SimeonSimeonovIvanov/AVR-LPC/Scheme and Board/v.0.0.5/v.0.0.5 (Bottom - Component Side - Mirror).pdf

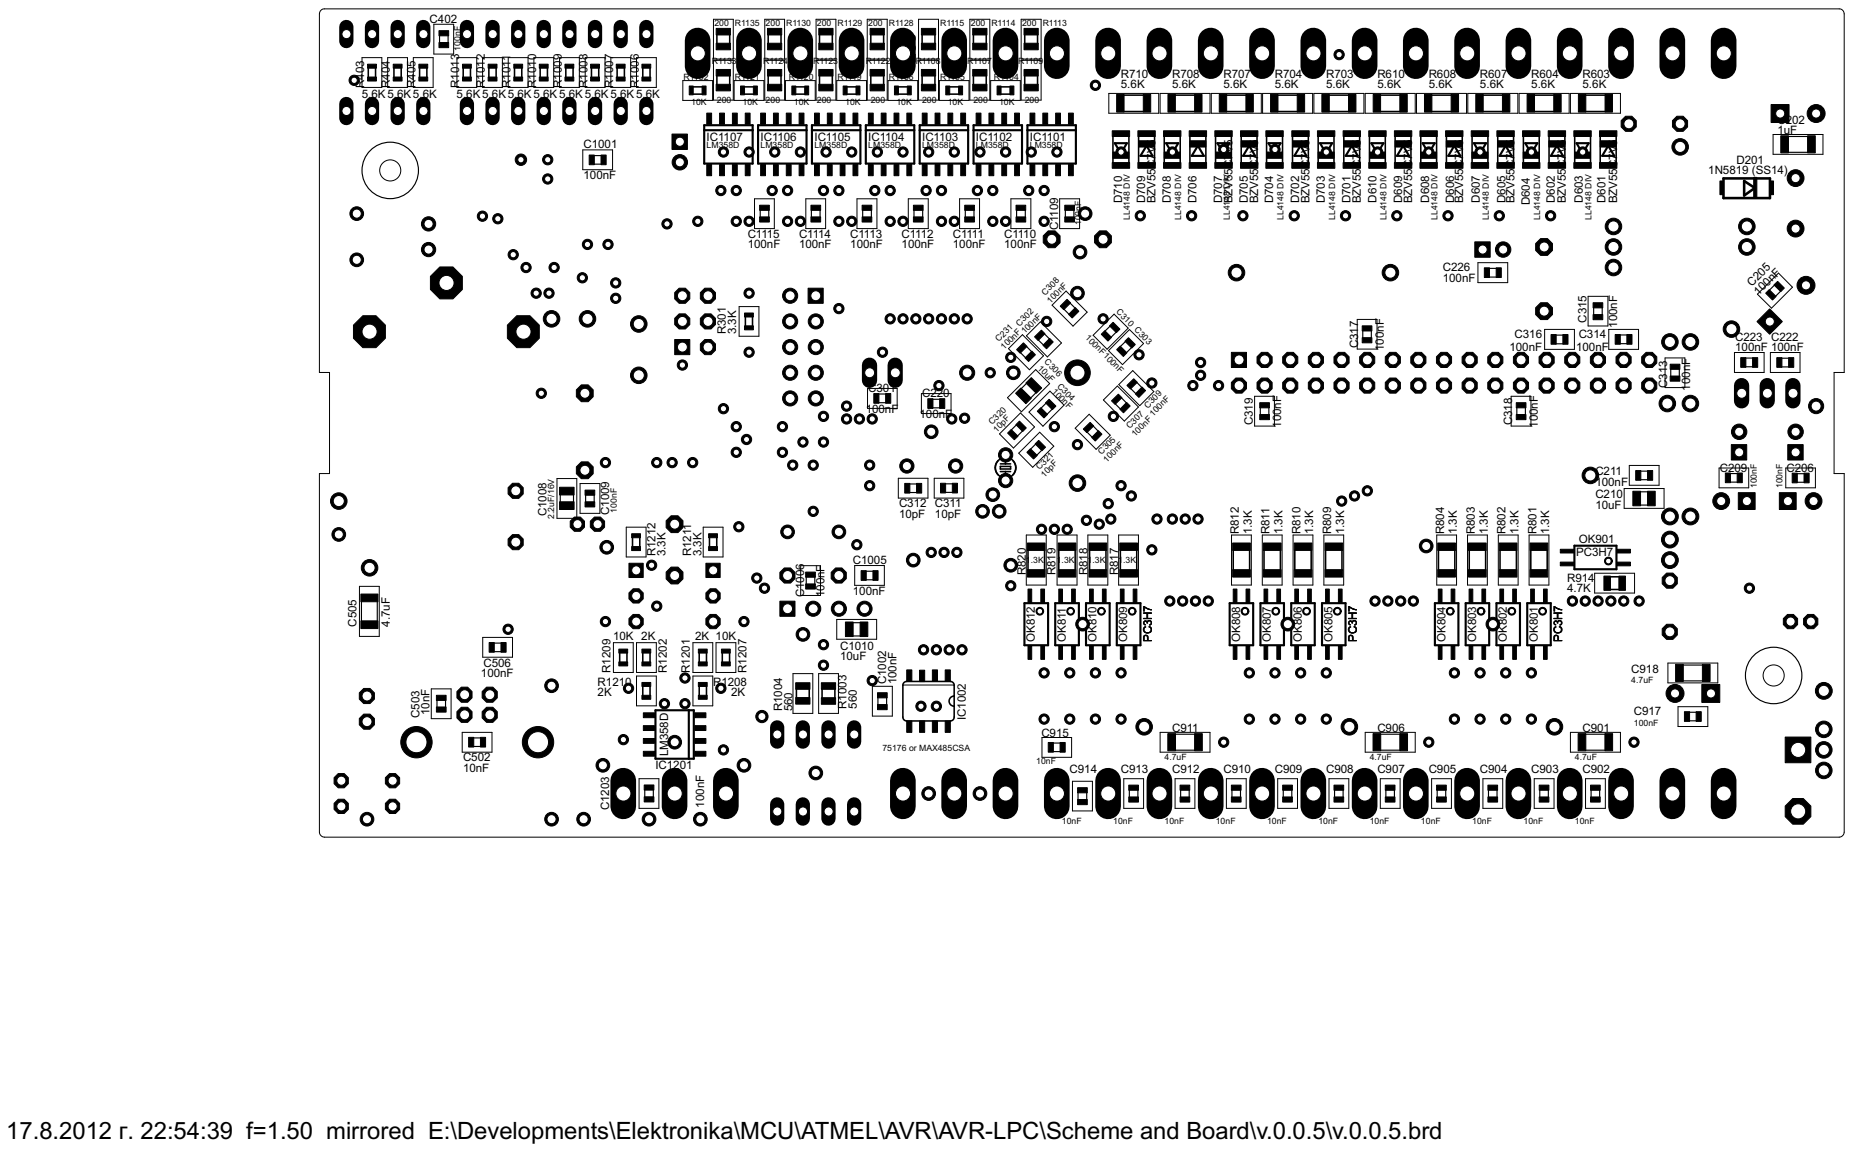
[picture p32: page 1]

17.8.2012 г. 22:54:39 f=1.50 mirrored E:\Developments\Elektronika\MCU\ATMEL\AVR\AVR-LPC\Scheme and Board\v.0.0.5\v.0.0.5.brd
