SimeonSimeonovIvanov/AVR-LPC/Scheme and Board/v.0.0.3/v.0.0.3 (Component Side).pdf

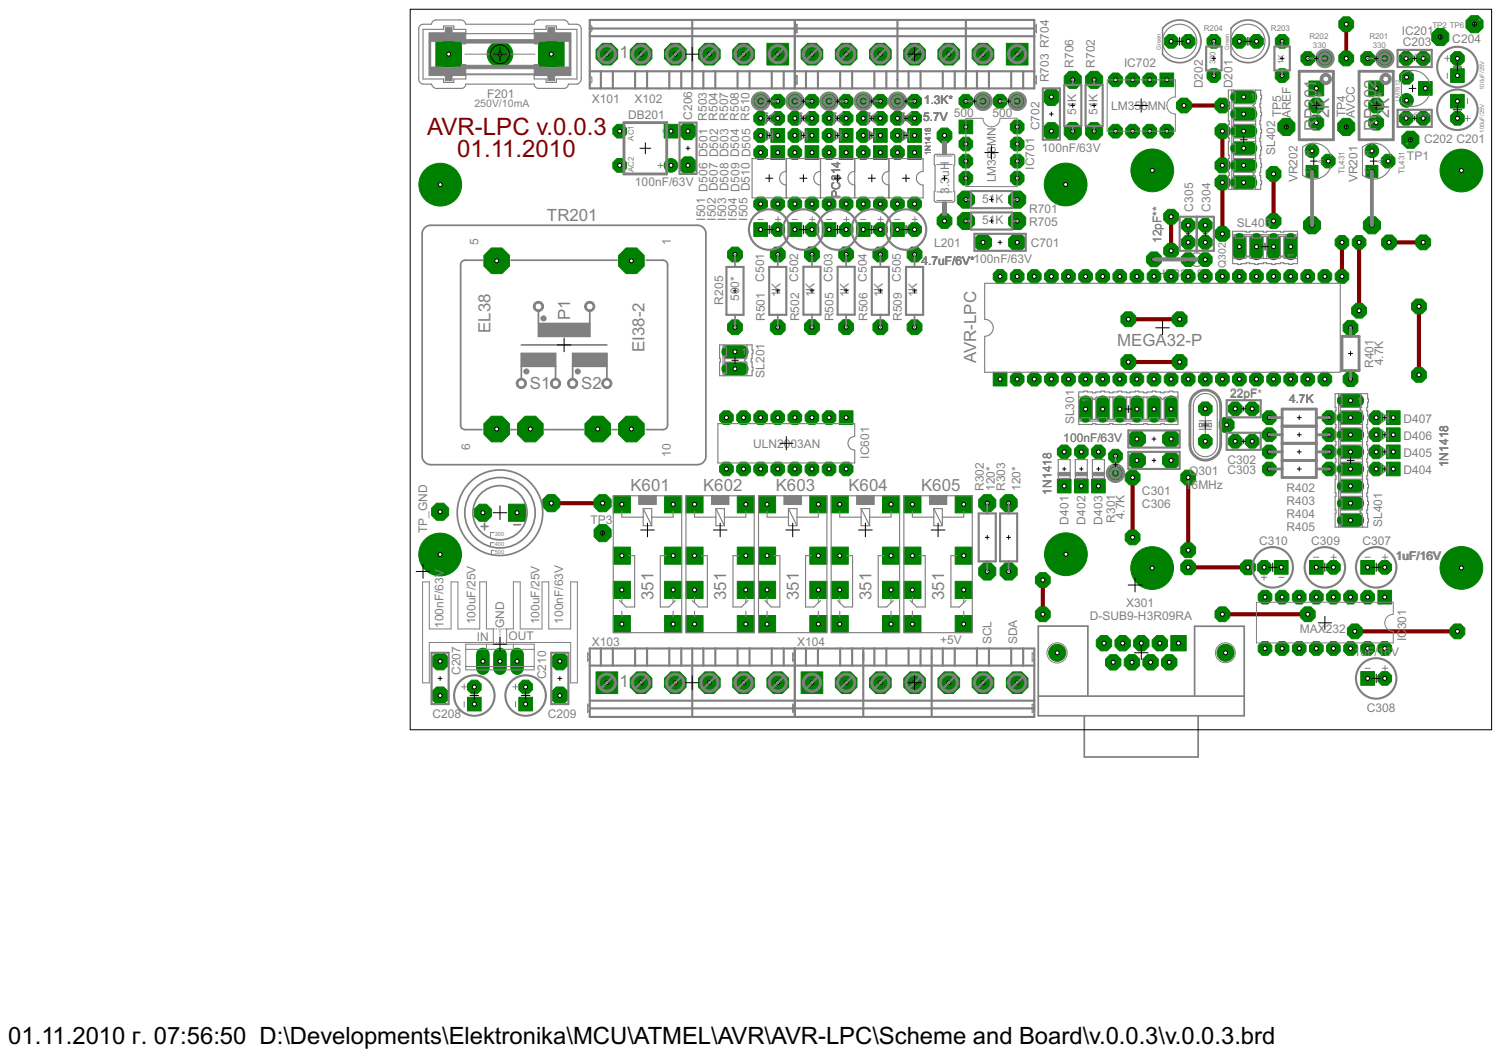
[picture p33: page 1]

01.11.2010 г. 07:56:50 D:\Developments\Elektronika\MCU\ATMEL\AVR\AVR-LPC\Scheme and Board\v.0.0.3\v.0.0.3.brd
