SimeonSimeonovIvanov/AVR-LPC/Scheme and Board/v.0.0.6/v.0.0.6 (All Side).pdf

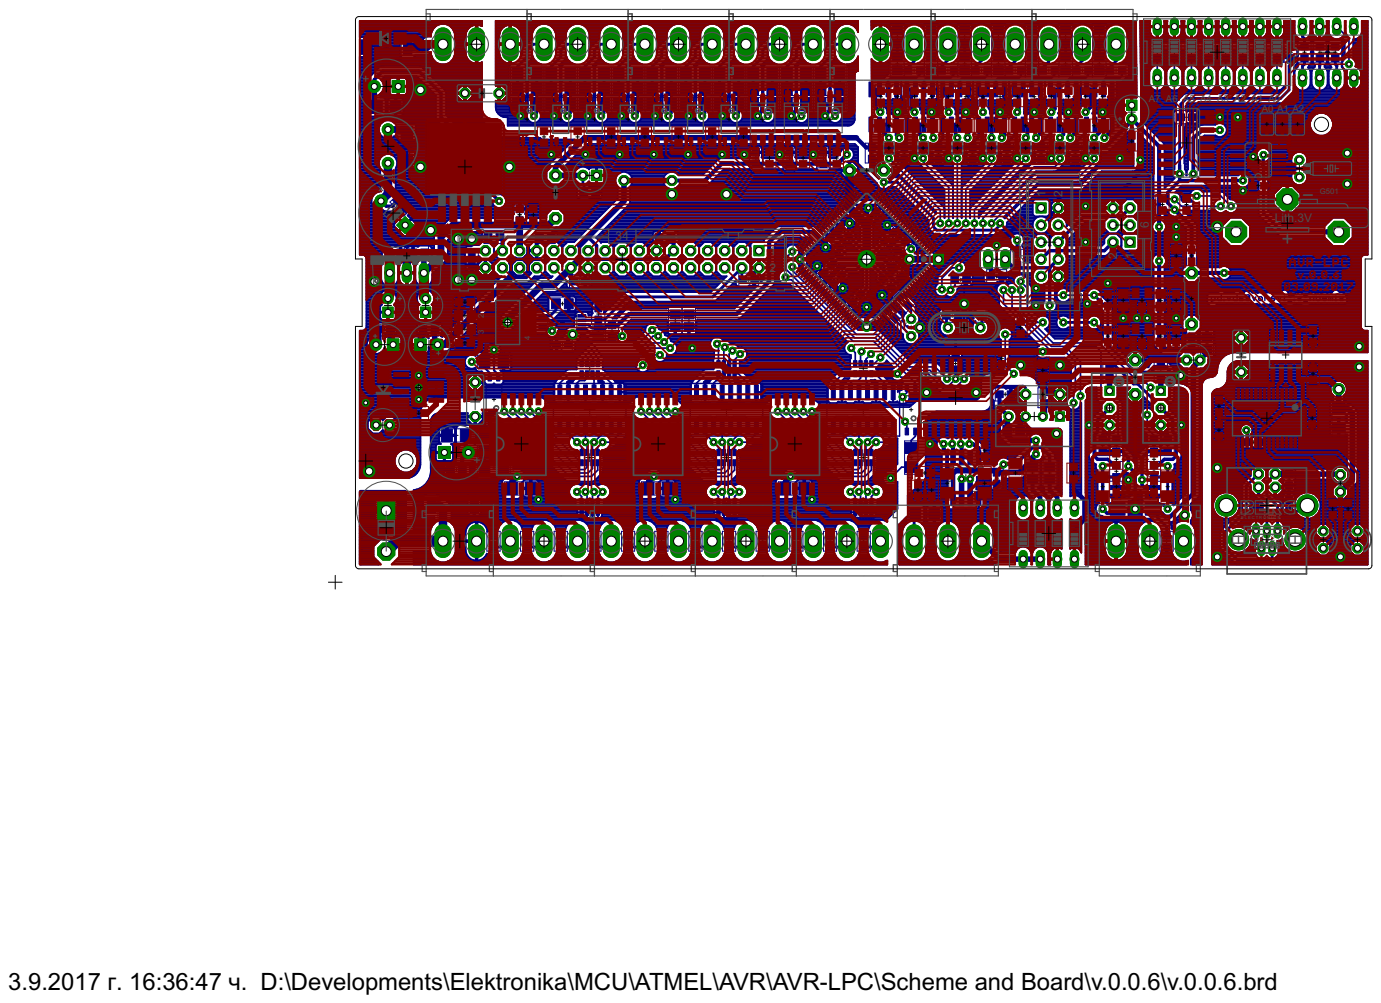
[picture p34: page 1]

3.9.2017 г. 16:36:47 ч. D:\Developments\Elektronika\MCU\ATMEL\AVR\AVR-LPC\Scheme and Board\v.0.0.6\v.0.0.6.brd
