SimeonSimeonovIvanov/AVR-LPC/Scheme and Board/v.0.0.9/v.0.0.9 (All Side).pdf

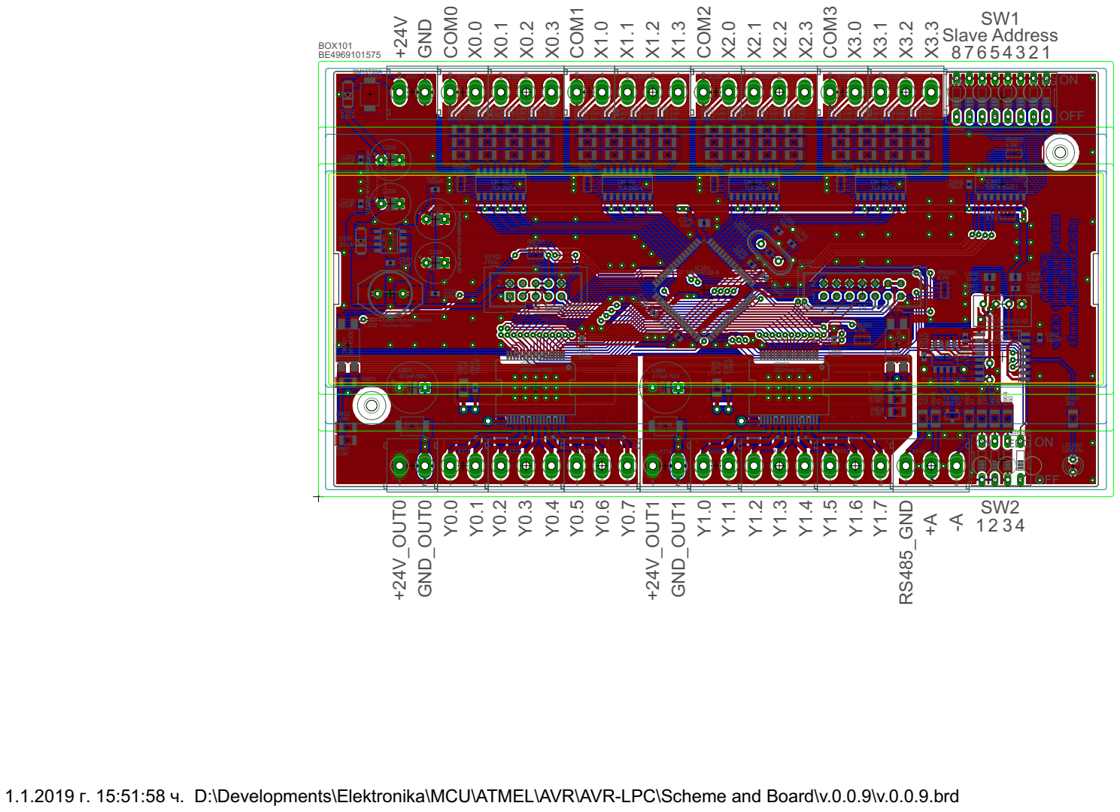
[picture p35: page 1]

D102 SS14 | OFF

E 220uF 50V LOW ESR-Fujicon CE 220uF 50V LOW ESR-Fujicon

CE 68uF 50V LOW ESR-Fujicon

CE 68uF 50V LOW ESR-Fujico

1.1.2019 г. 15:51:58 ч. D:\Developments\Elektronika\MCU\ATMEL\AVR\AVR-LPC\Scheme and Board\v.0.0.9\v.0.0.9.brd
