SimeonSimeonovIvanov/AVR-LPC/Scheme and Board/v.0.1.0/v.0.1.0 (All Side).pdf

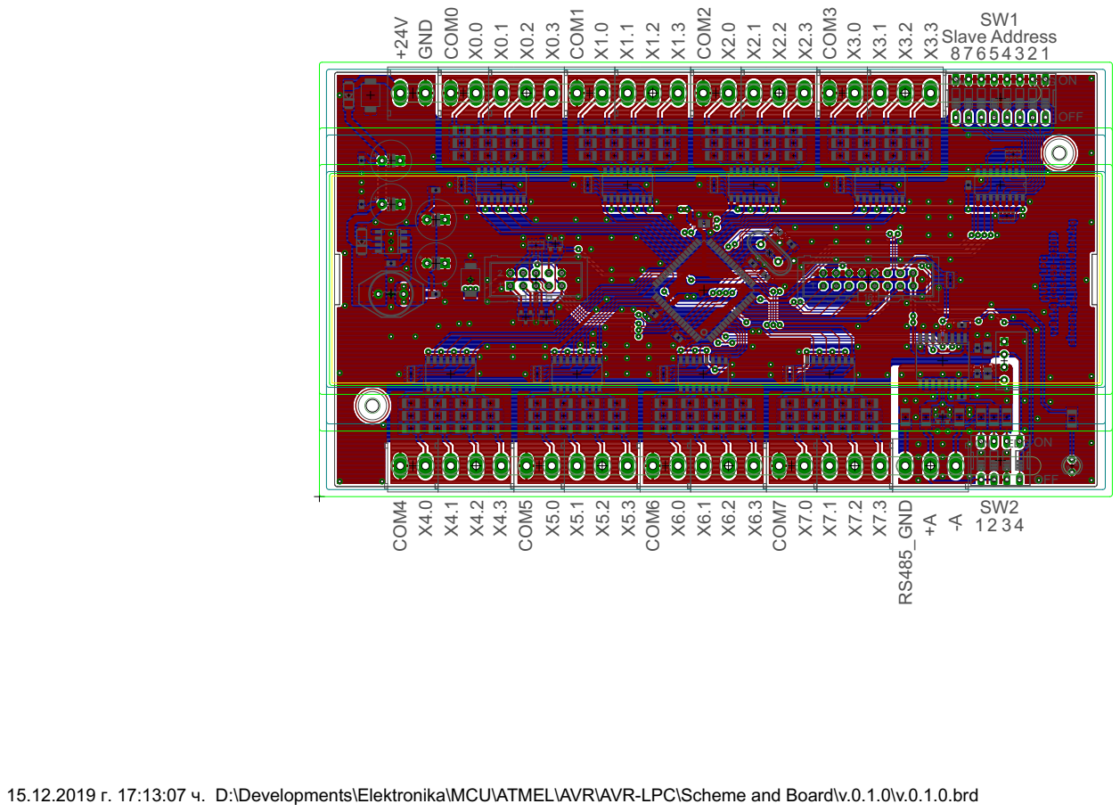
[picture p36: page 1]

15.12.2019 г. 17:13:07 ч. D:\Developments\Elektronika\MCU\ATMEL\AVR\AVR-LPC\Scheme and Board\v.0.1.0\v.0.1.0.brd
