SimeonSimeonovIvanov/AVR-LPC/Scheme and Board/v.0.1.6/v.0.1.6 (All Side).pdf

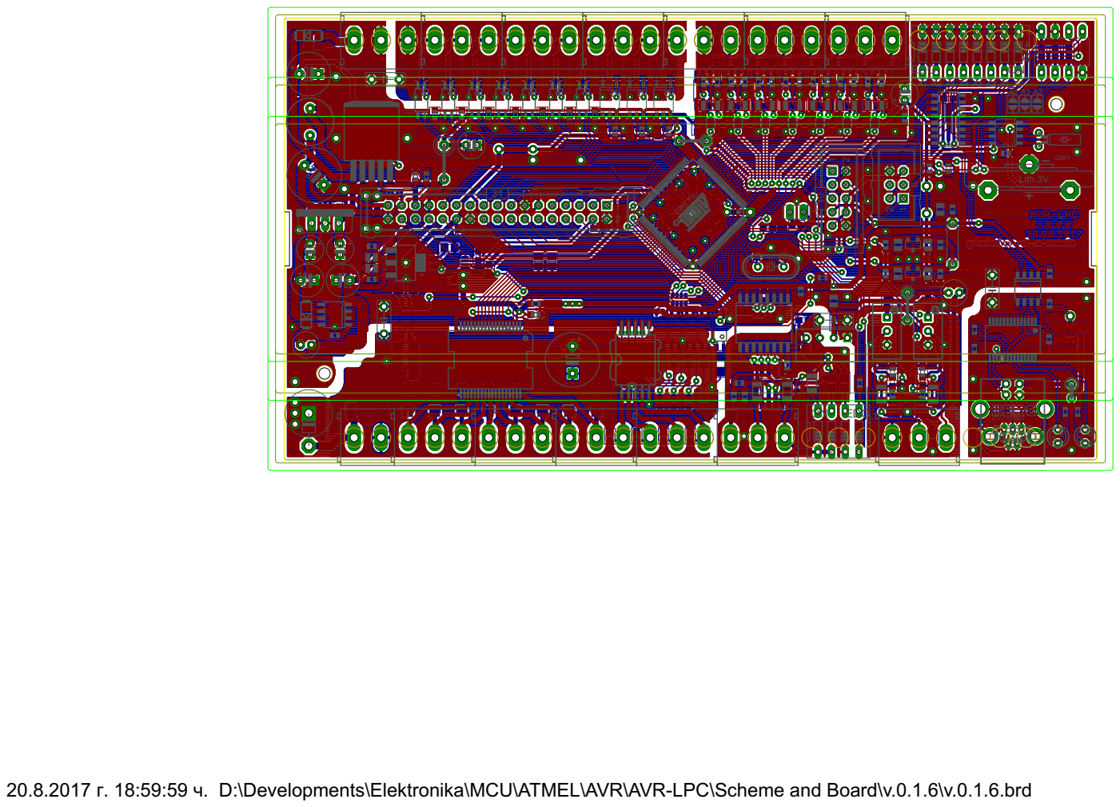
[picture p37: page 1]

20.8.2017 г. 18:59:59 ч. D:\Developments\Elektronika\MCU\ATMEL\AVR\AVR-LPC\Scheme and Board\v.0.1.6\v.0.1.6.brd
