SimeonSimeonovIvanov/AVR-LPC/Scheme and Board/v.0.1.8/v.0.1.8 (All Side).pdf

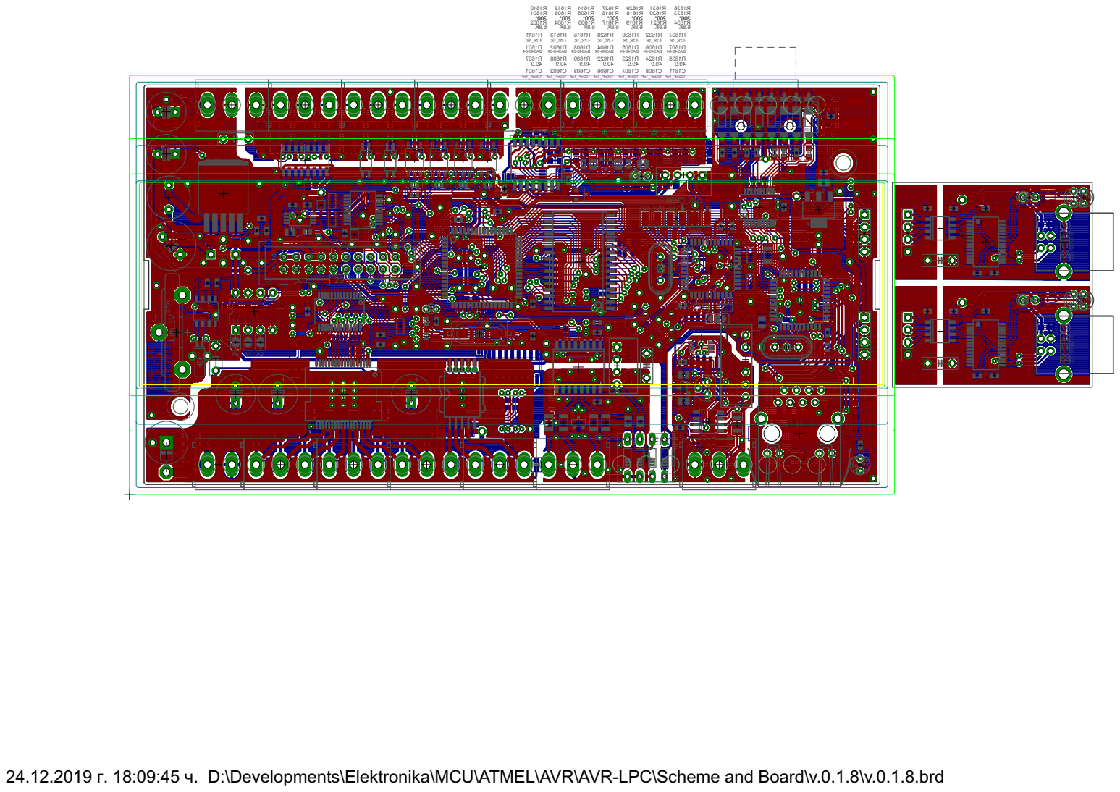
[picture p38: page 1]

24.12.2019 г. 18:09:45 ч. D:\Developments\Elektronika\MCU\ATMEL\AVR\AVR-LPC\Scheme and Board\v.0.1.8\v.0.1.8.brd
