SimeonSimeonovIvanov/AVR-LPC/Scheme and Board/v.0.0.8/v.0.0.8 (Top Place).pdf

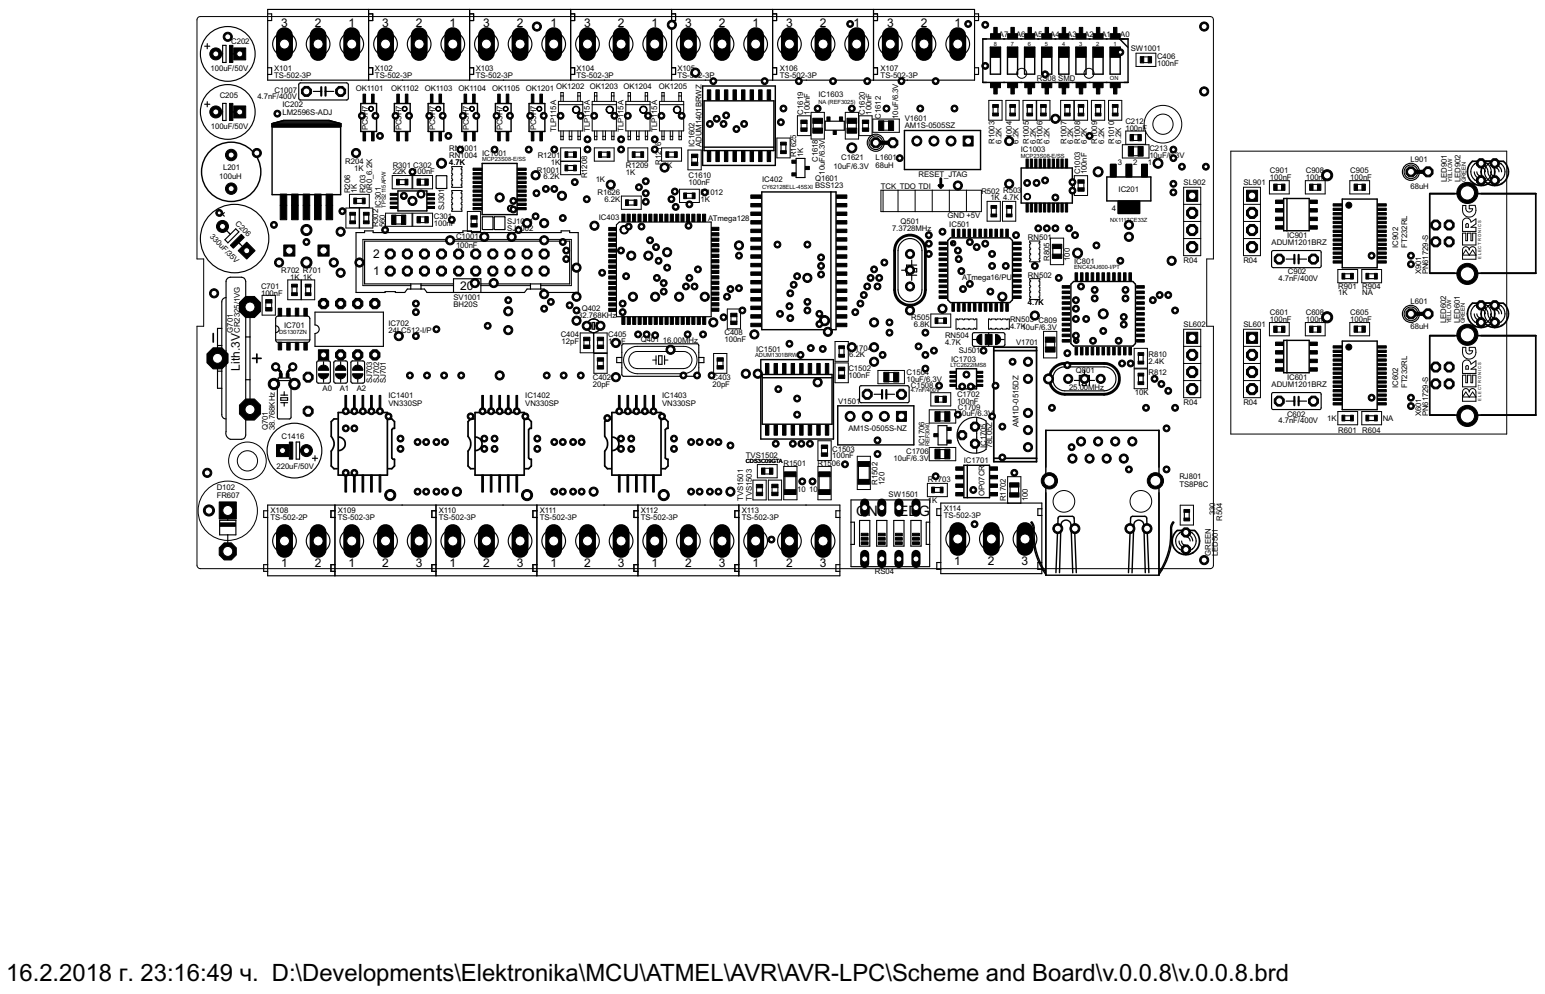
[picture p39: page 1]

16.2.2018 г. 23:16:49 ч. D:\Developments\Elektronika\MCU\ATMEL\AVR\AVR-LPC\Scheme and Board\v.0.0.8\v.0.0.8.brd
