SimeonSimeonovIvanov/AVR-LPC/Scheme and Board/v.0.0.0/v.0.0.0 (Bottom Side).pdf

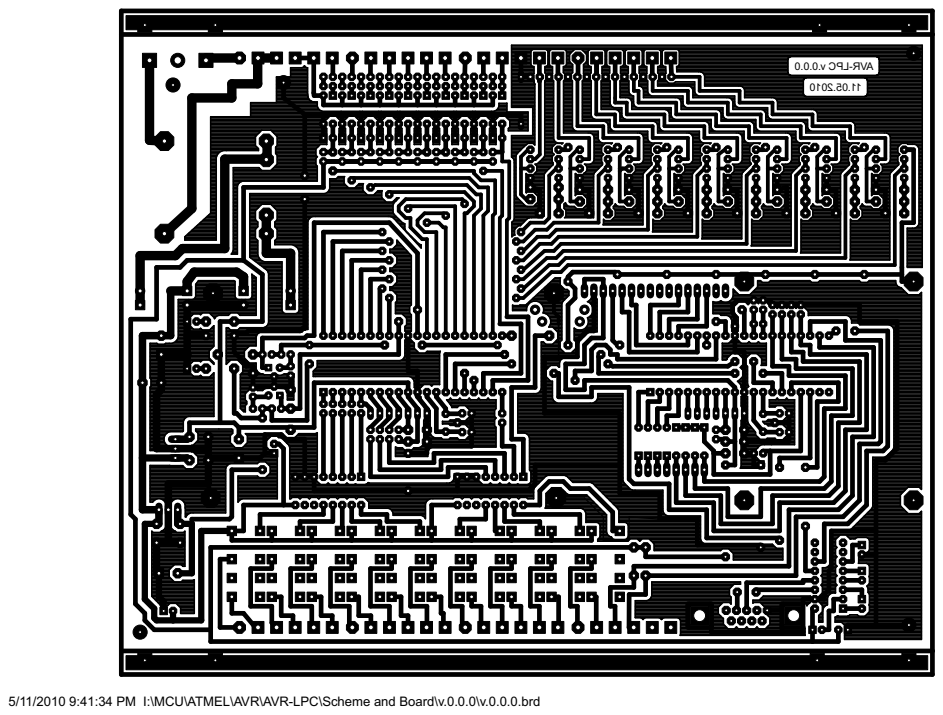
[picture p40: page 1]

5/11/2010 9:41:34 PM I:\MCU\ATMEL\AVR\AVR-LPC\Scheme and Board\v.0.0.0\v.0.0.0.brd
