SimeonSimeonovIvanov/AVR-LPC/Scheme and Board/v.0.0.0/v.0.0.0.pdf

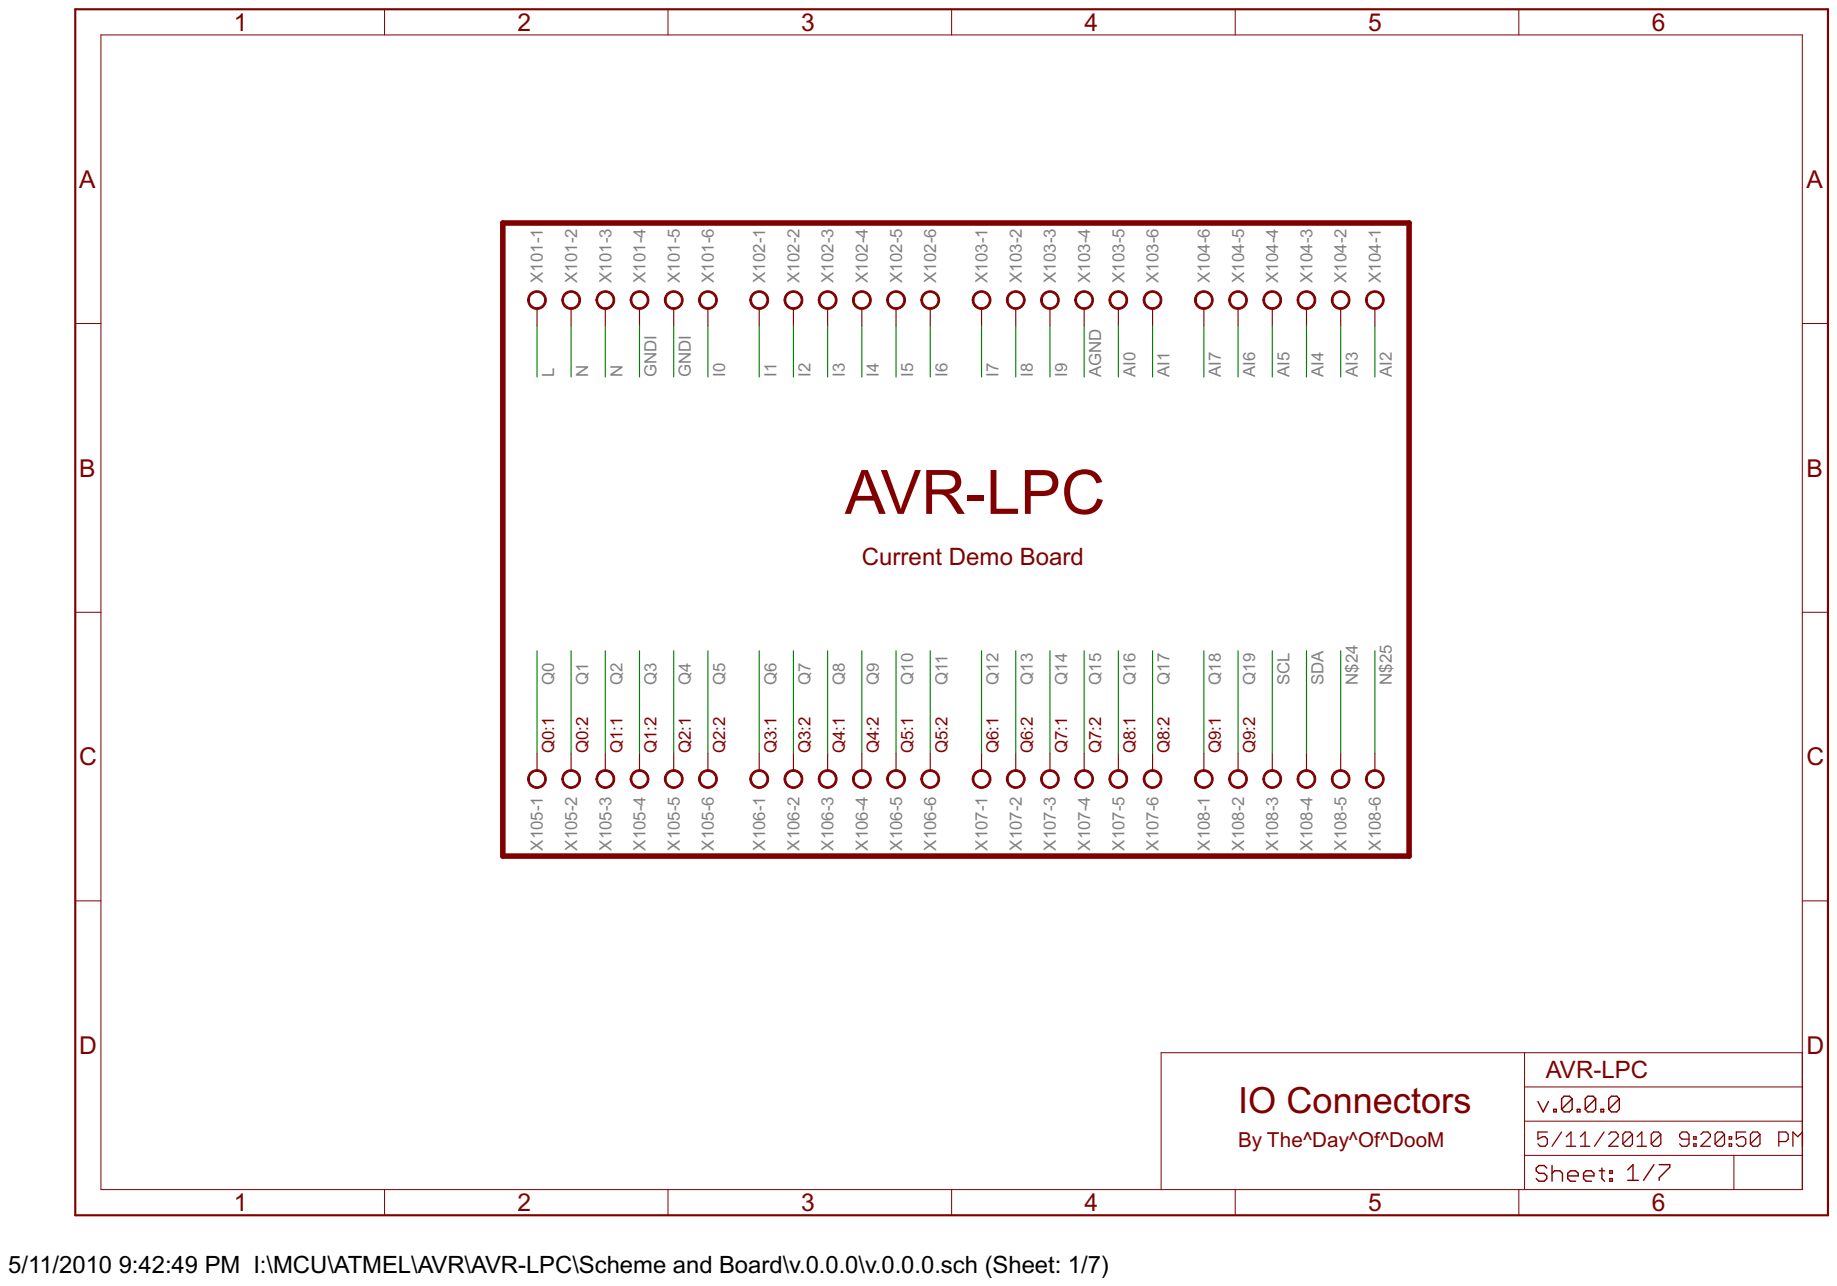
[picture p41: page 1]

By The^Day^Of^DooM

5/11/2010 9:42:49 PM I:\MCU\ATMEL\AVR\AVR-LPC\Scheme and Board\v.0.0.0\v.0.0.0.sch (Sheet: 1/7)

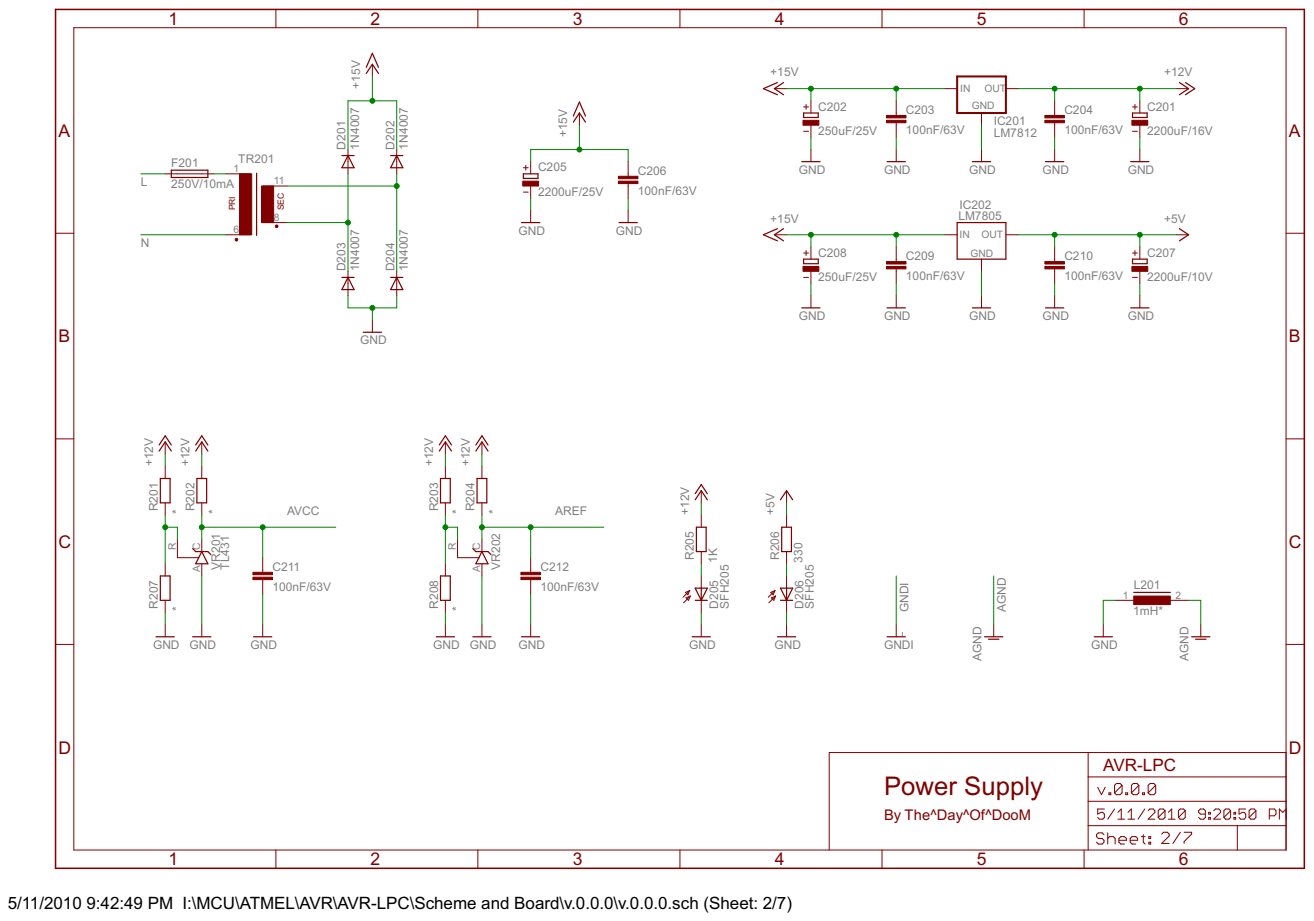
[picture p42: page 2]

By The^Day^Of^DooM

5/11/2010 9:42:49 PM I:\MCU\ATMEL\AVR\AVR-LPC\Scheme and Board\v.0.0.0\v.0.0.0.sch (Sheet: 2/7)

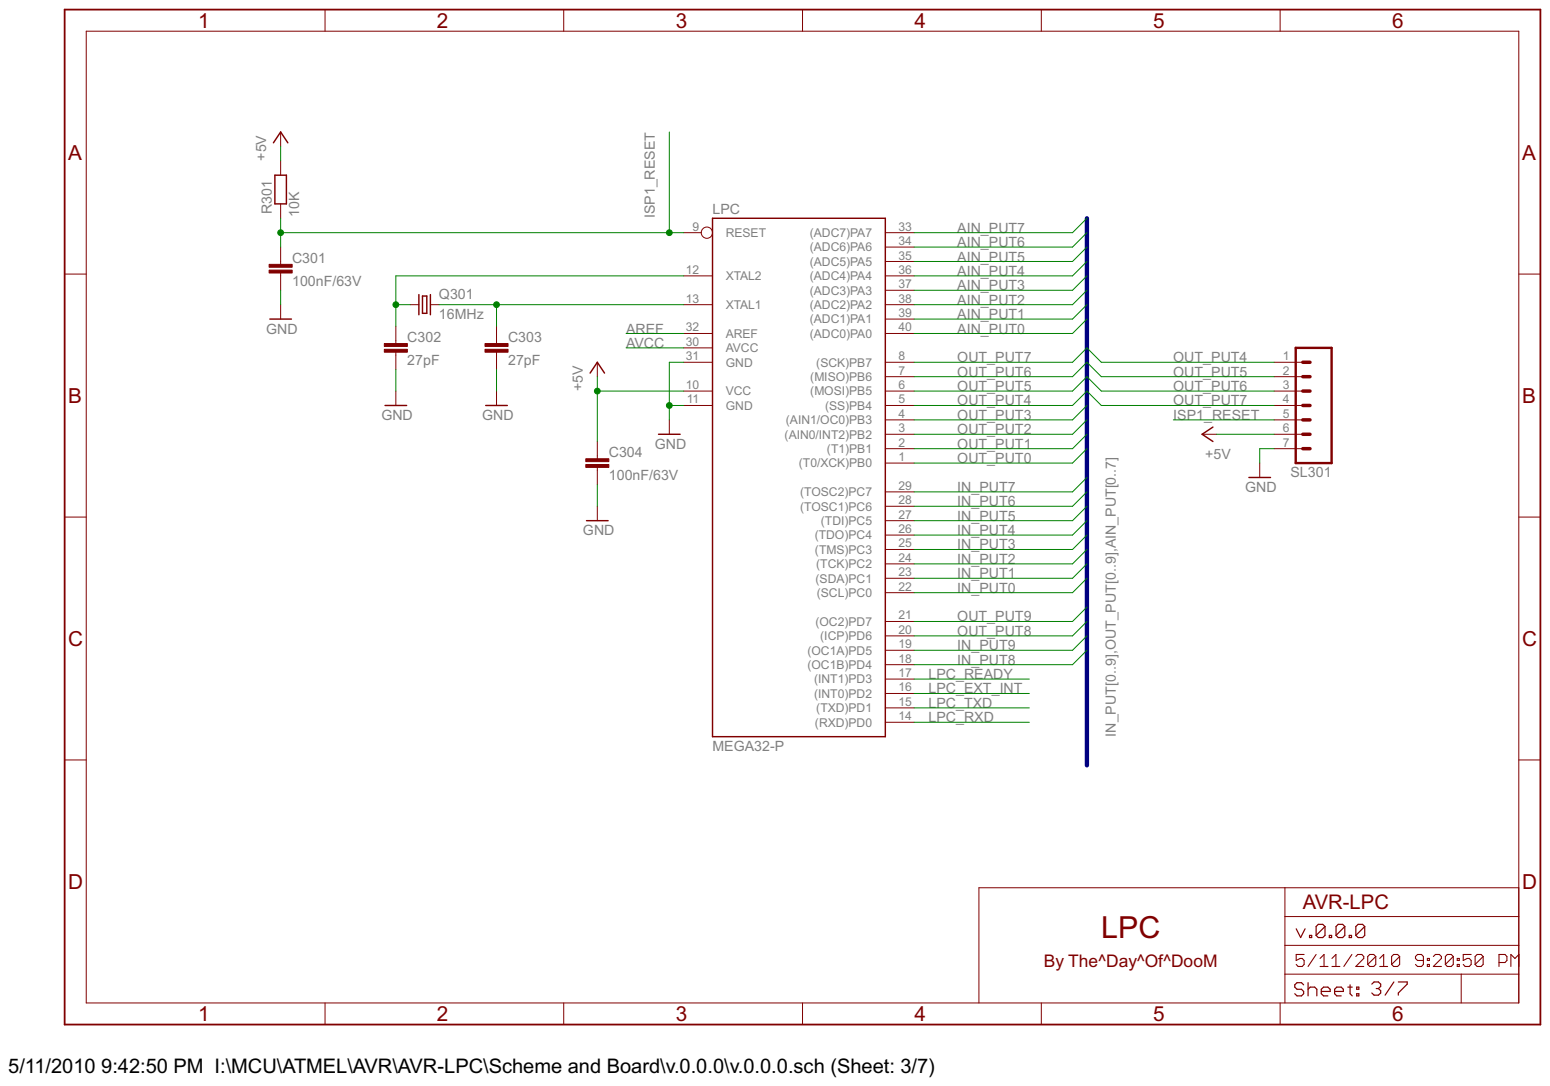
[picture p43: page 3]

By The^Day^Of^DooM

5/11/2010 9:42:50 PM I:\MCU\ATMEL\AVR\AVR-LPC\Scheme and Board\v.0.0.0\v.0.0.0.sch (Sheet: 3/7)

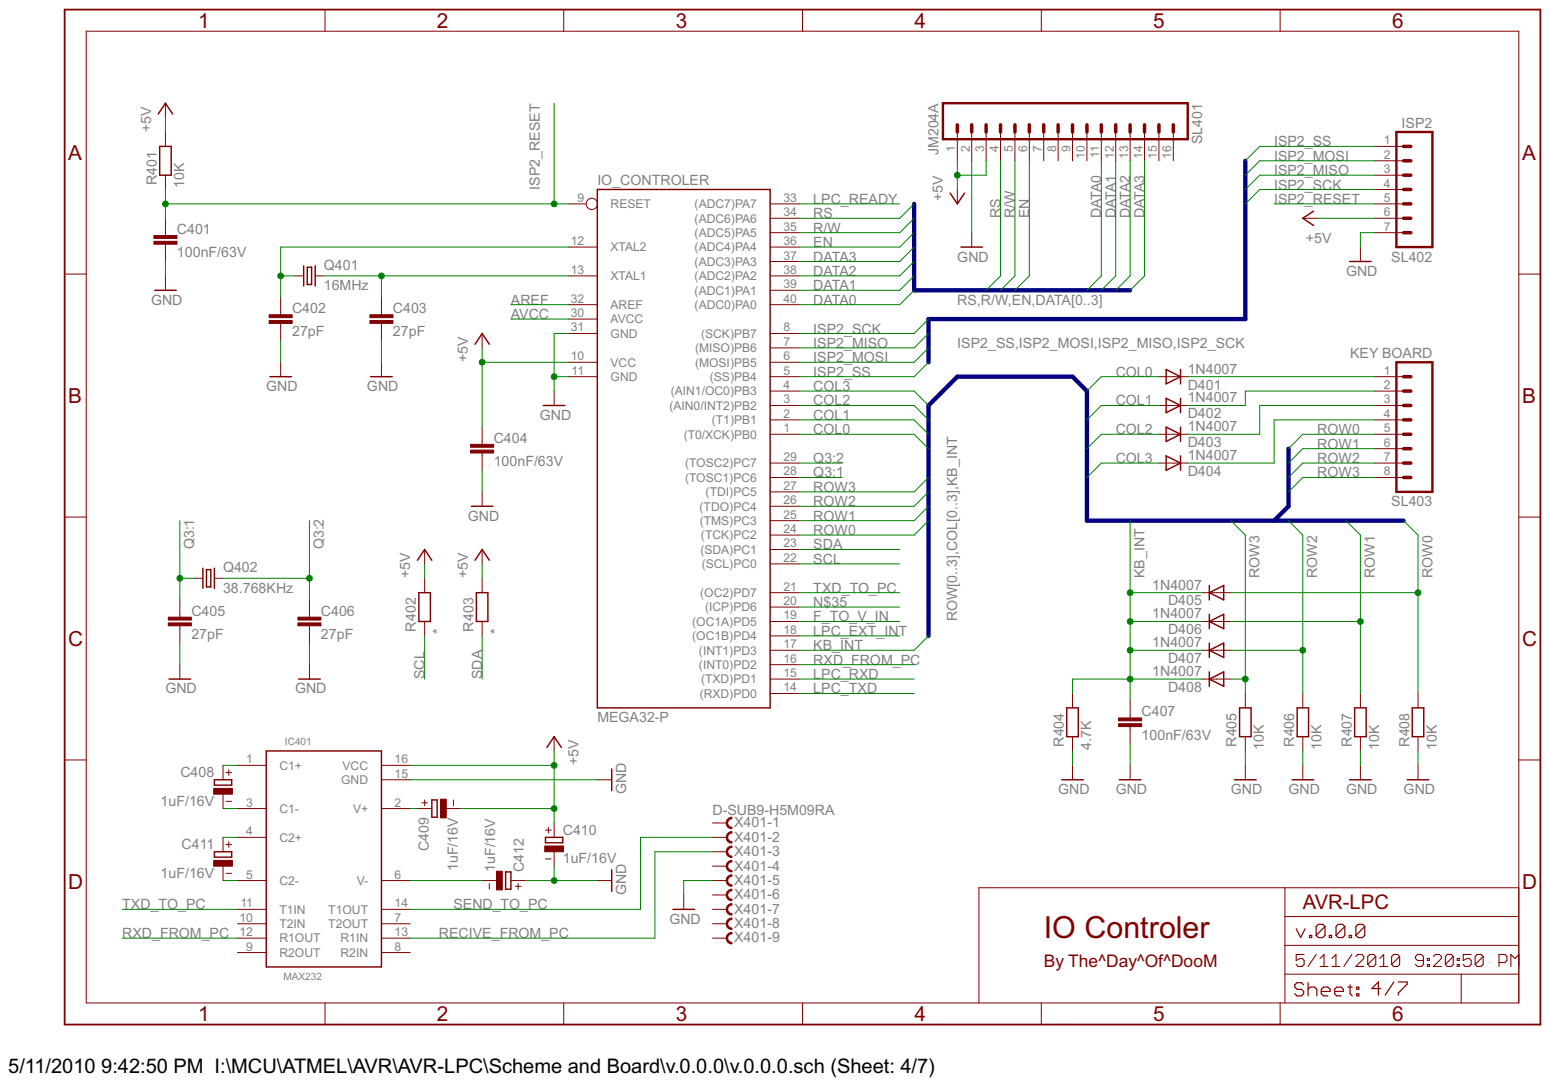
[picture p44: page 4]

W[0..3],COL[0..3],KB_INT RS,R/W,EN,DATA[0..3]

By The^Day^Of^DooM

5/11/2010 9:42:50 PM I:\MCU\ATMEL\AVR\AVR-LPC\Scheme and Board\v.0.0.0\v.0.0.0.sch (Sheet: 4/7)

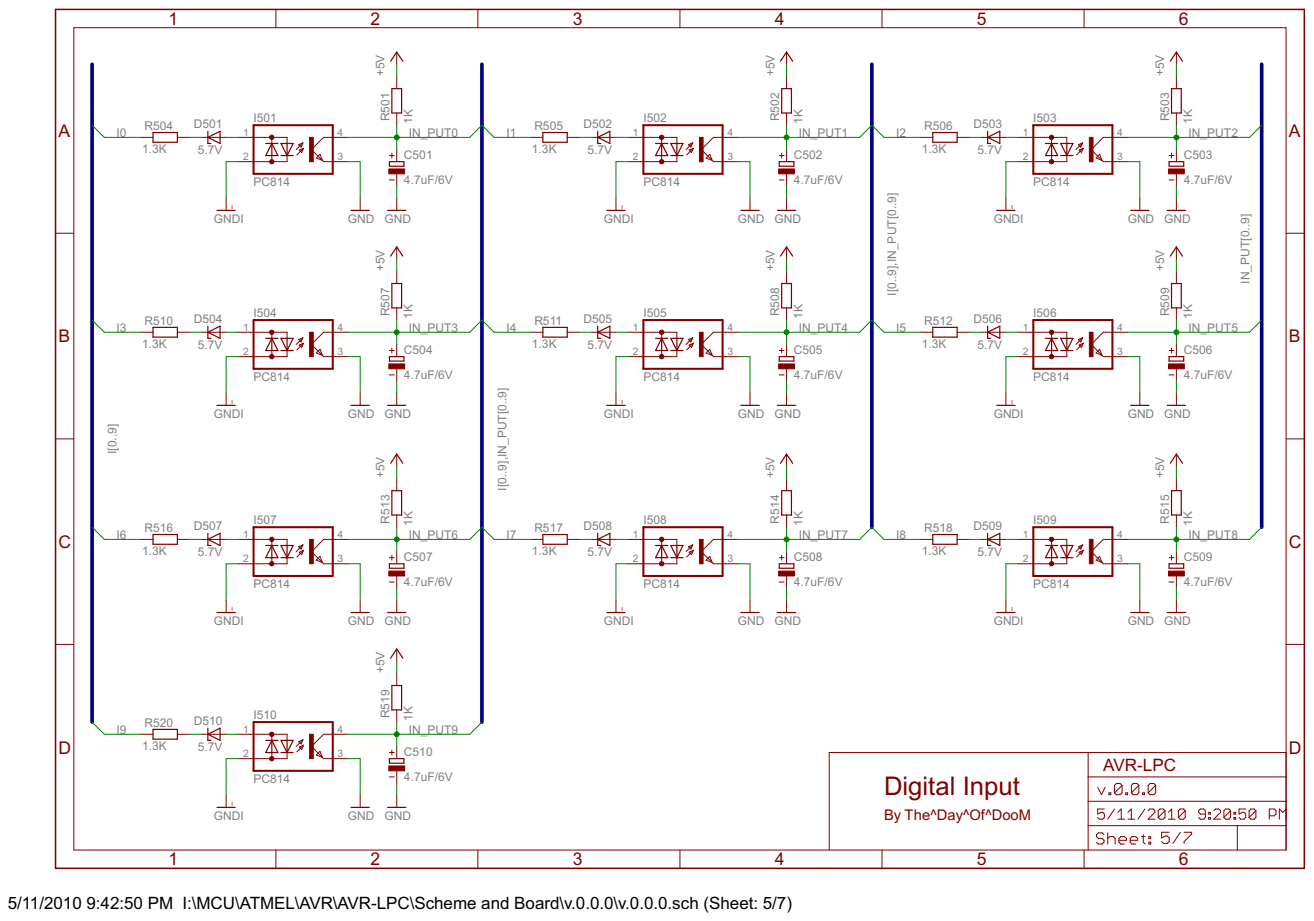
[picture p45: page 5]

By The^Day^Of^DooM

5/11/2010 9:42:50 PM I:\MCU\ATMEL\AVR\AVR-LPC\Scheme and Board\v.0.0.0\v.0.0.0.sch (Sheet: 5/7)

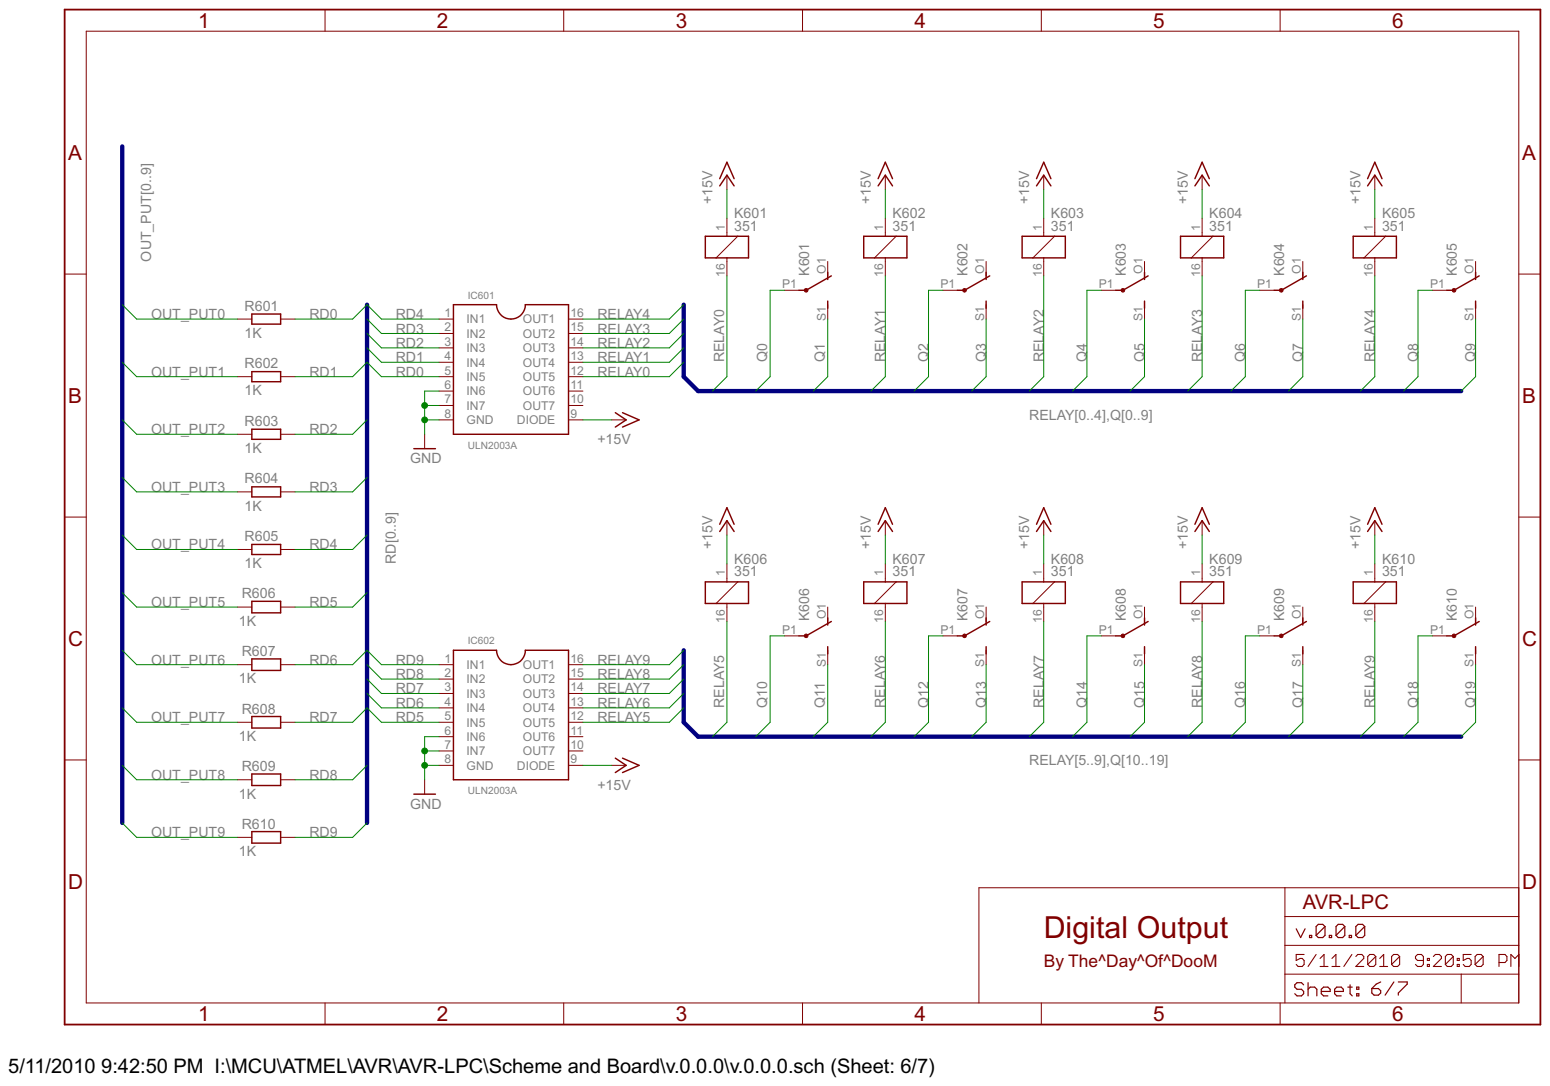
[picture p46: page 6]

By The^Day^Of^DooM

5/11/2010 9:42:50 PM I:\MCU\ATMEL\AVR\AVR-LPC\Scheme and Board\v.0.0.0\v.0.0.0.sch (Sheet: 6/7)

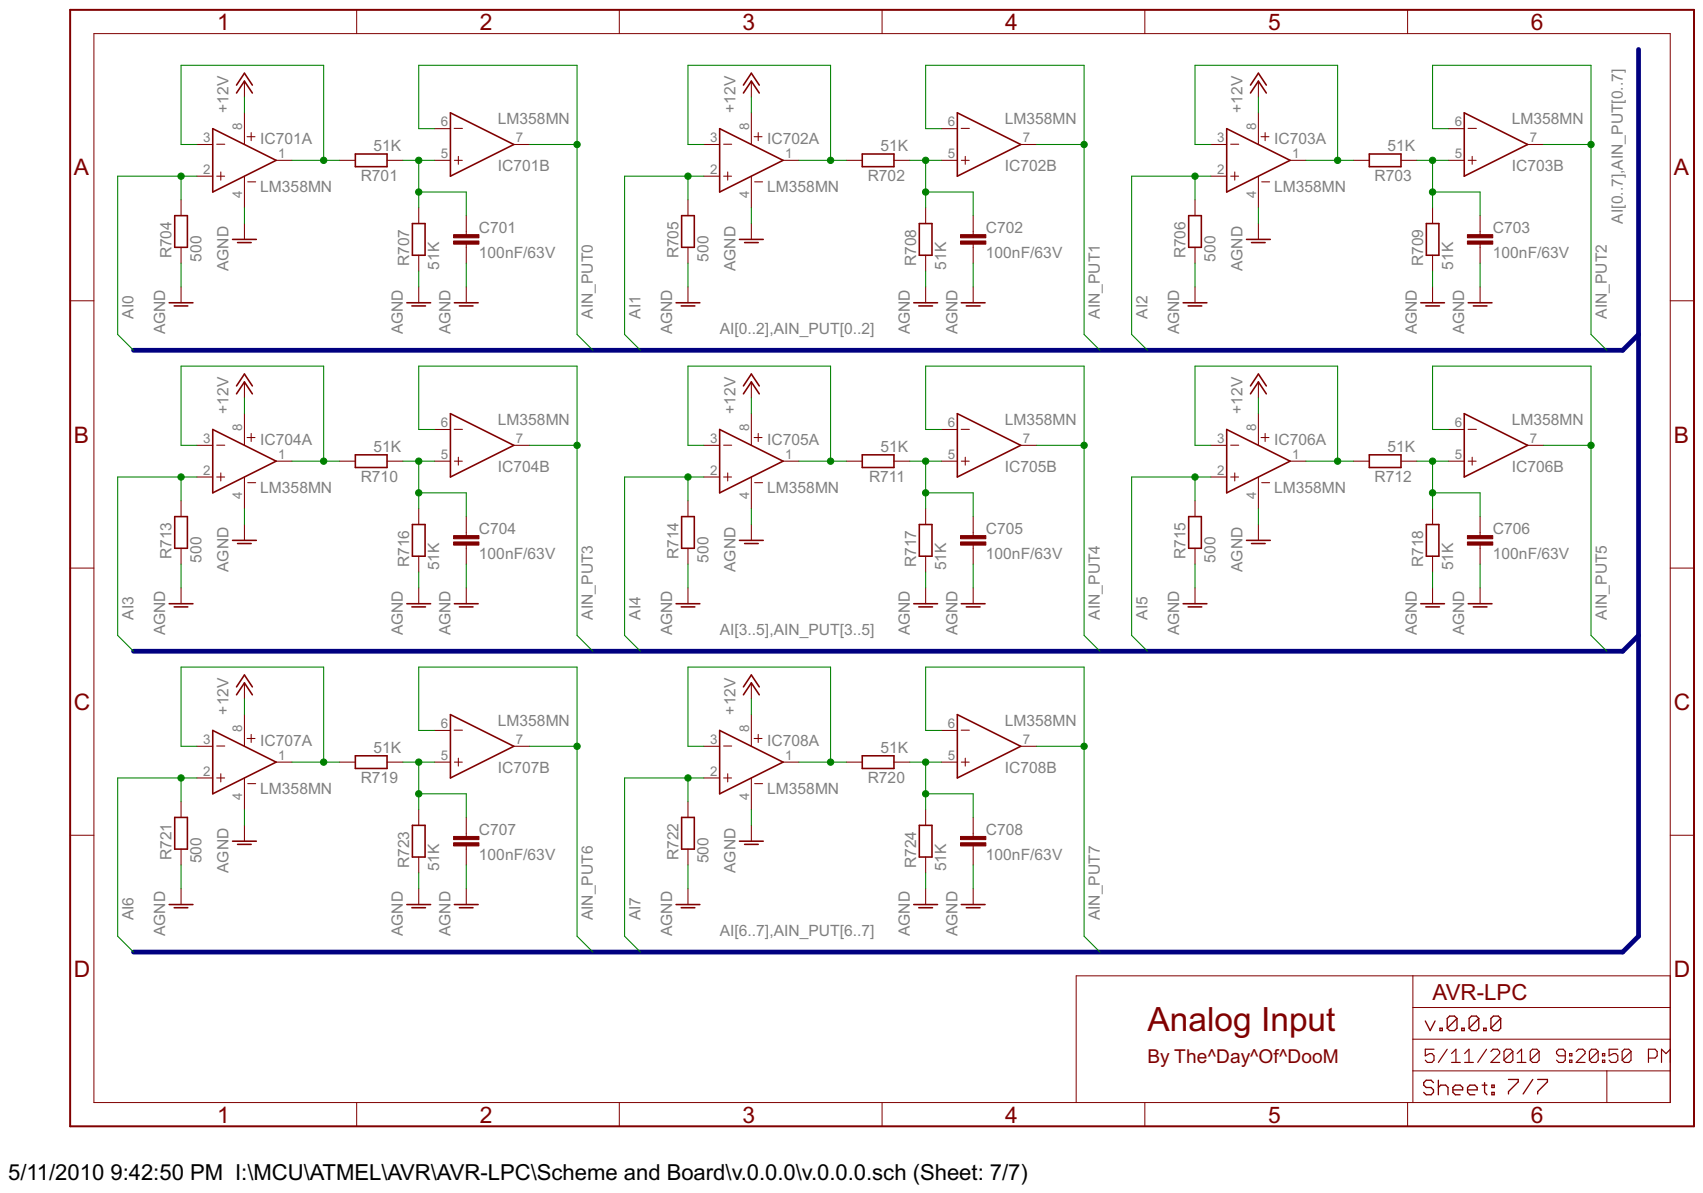
[picture p47: page 7]

By The^Day^Of^DooM

5/11/2010 9:42:50 PM I:\MCU\ATMEL\AVR\AVR-LPC\Scheme and Board\v.0.0.0\v.0.0.0.sch (Sheet: 7/7)
