SimeonSimeonovIvanov/AVR-LPC/Scheme and Board/v.0.0.1/v.0.0.1 (Bottom Side).pdf

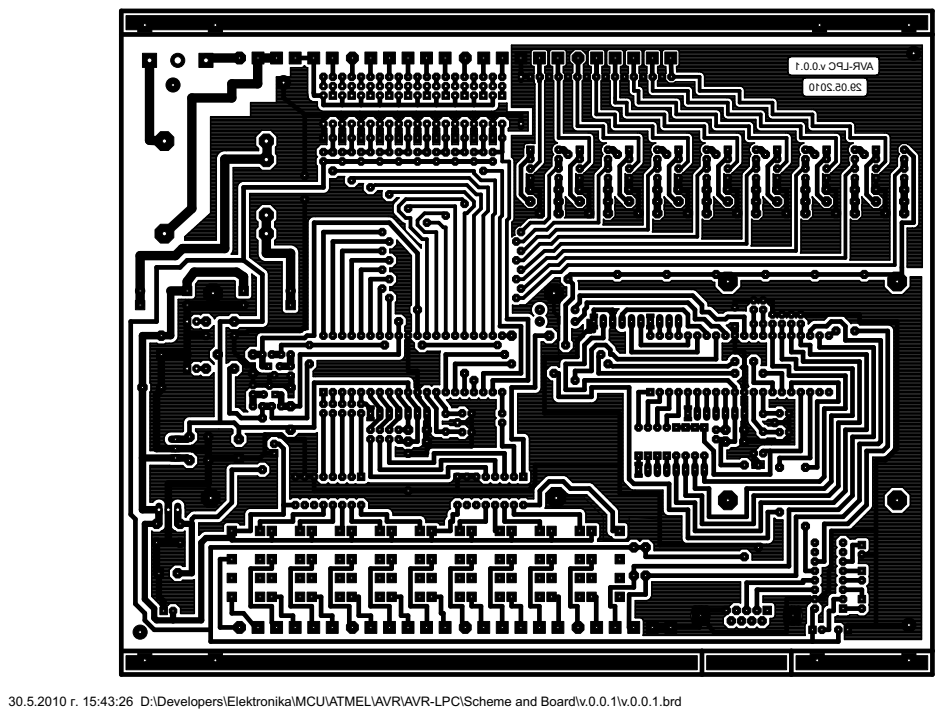
[picture p48: page 1]

30.5.2010 г. 15:43:26 D:\Developers\Elektronika\MCU\ATMEL\AVR\AVR-LPC\Scheme and Board\v.0.0.1\v.0.0.1.brd
