SimeonSimeonovIvanov/AVR-LPC/Scheme and Board/v.0.0.1/v.0.0.1.pdf

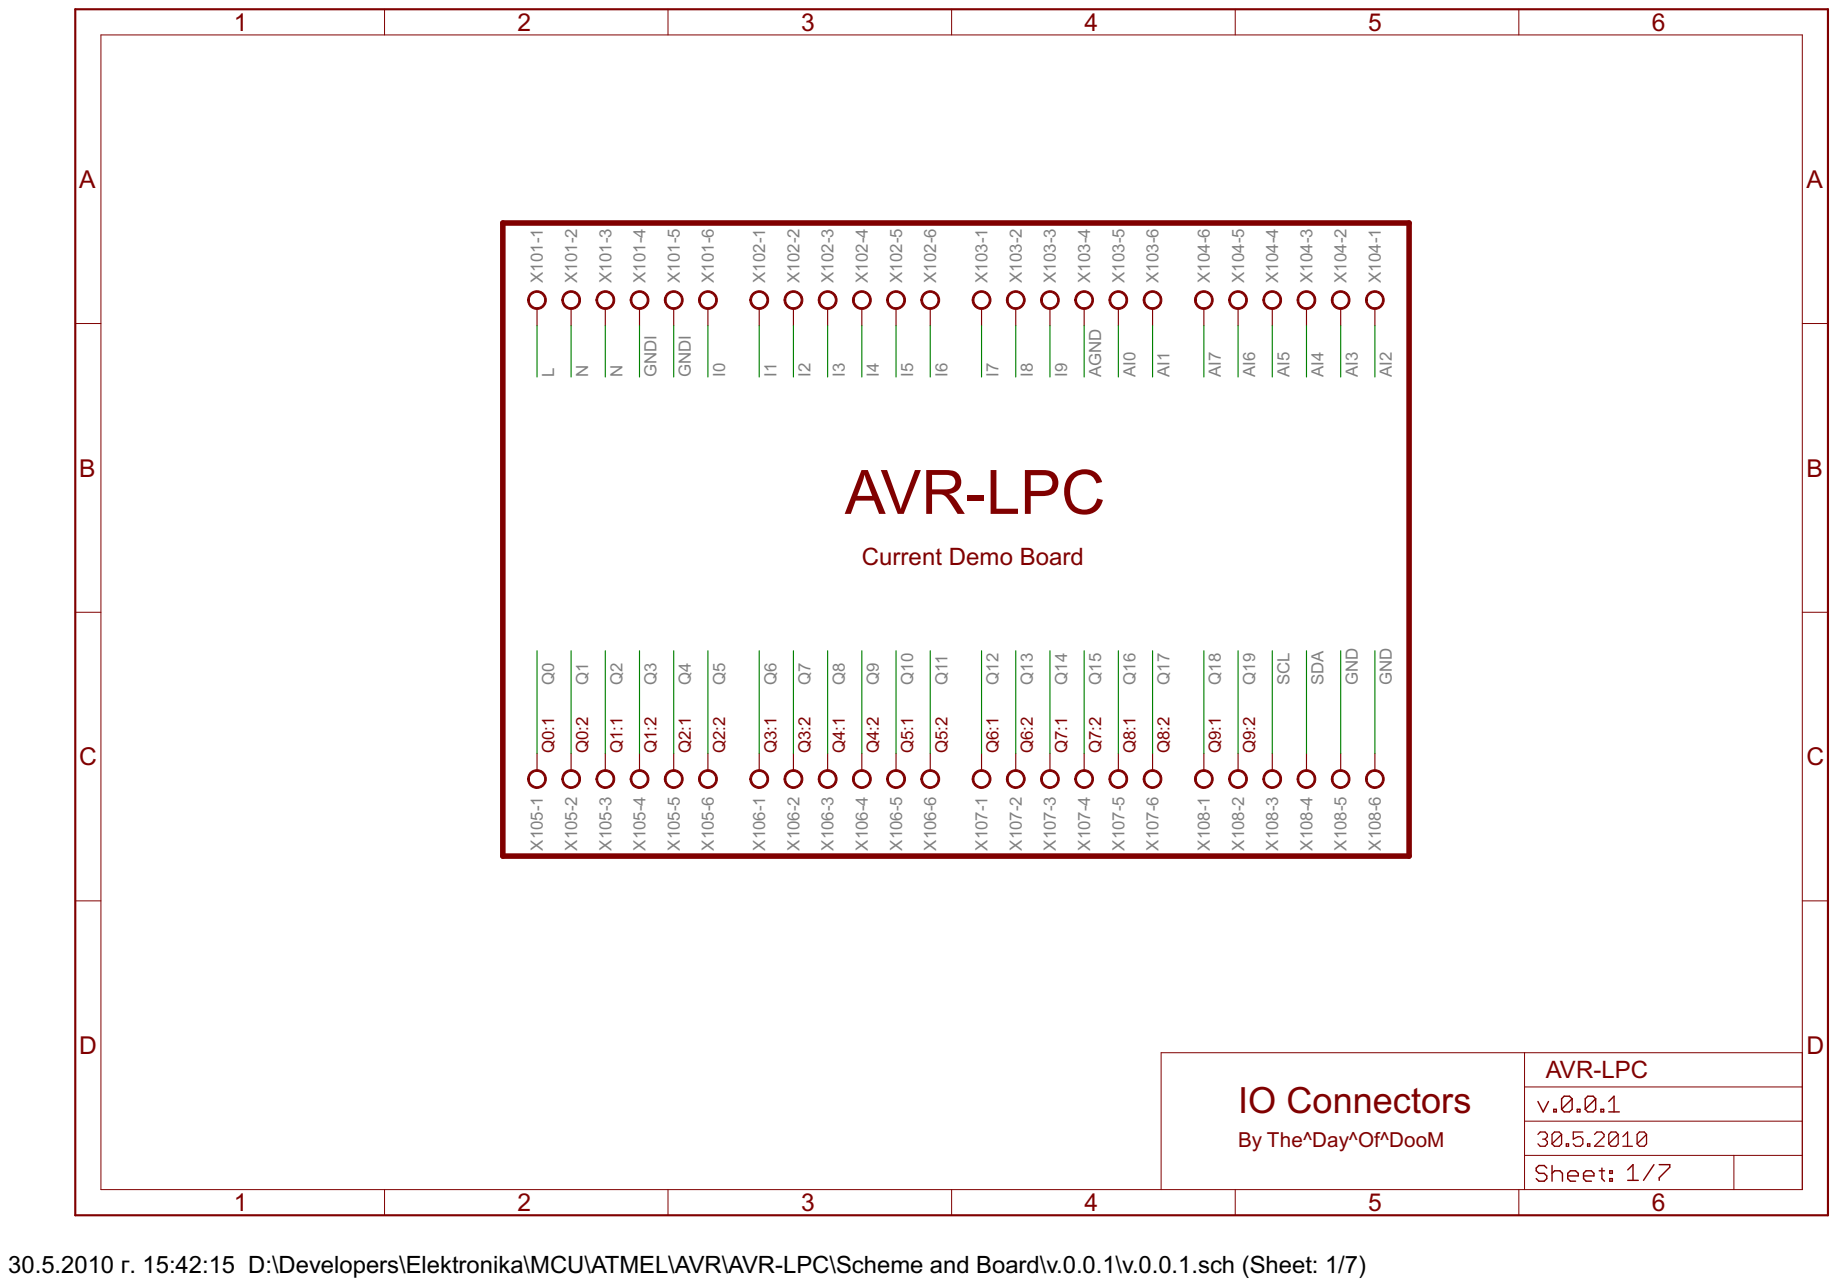
[picture p49: page 1]

By The^Day^Of^DooM

30.5.2010 г. 15:42:15 D:\Developers\Elektronika\MCU\ATMEL\AVR\AVR-LPC\Scheme and Board\v.0.0.1\v.0.0.1.sch (Sheet: 1/7)

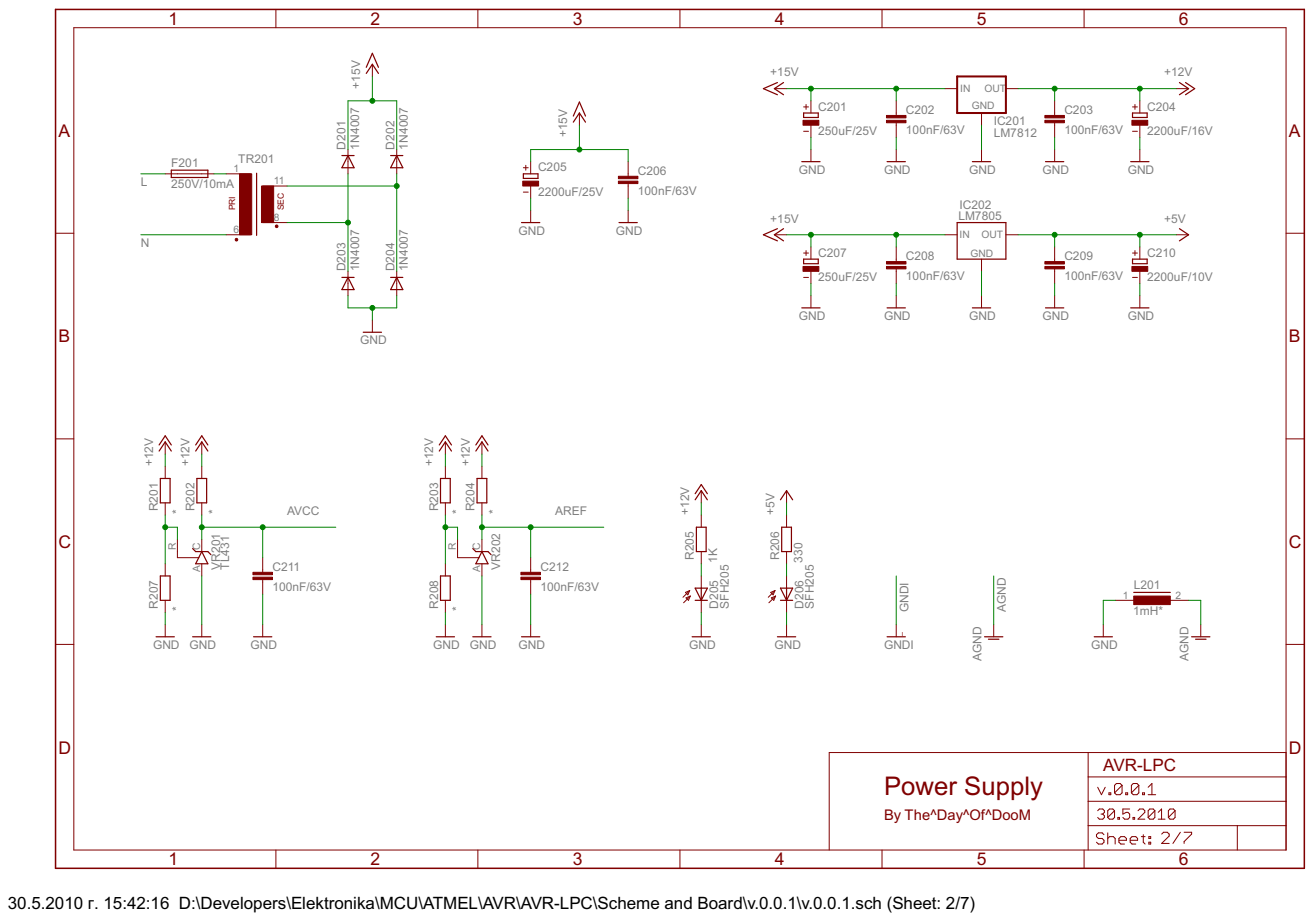
[picture p50: page 2]

By The^Day^Of^DooM

30.5.2010 г. 15:42:16 D:\Developers\Elektronika\MCU\ATMEL\AVR\AVR-LPC\Scheme and Board\v.0.0.1\v.0.0.1.sch (Sheet: 2/7)

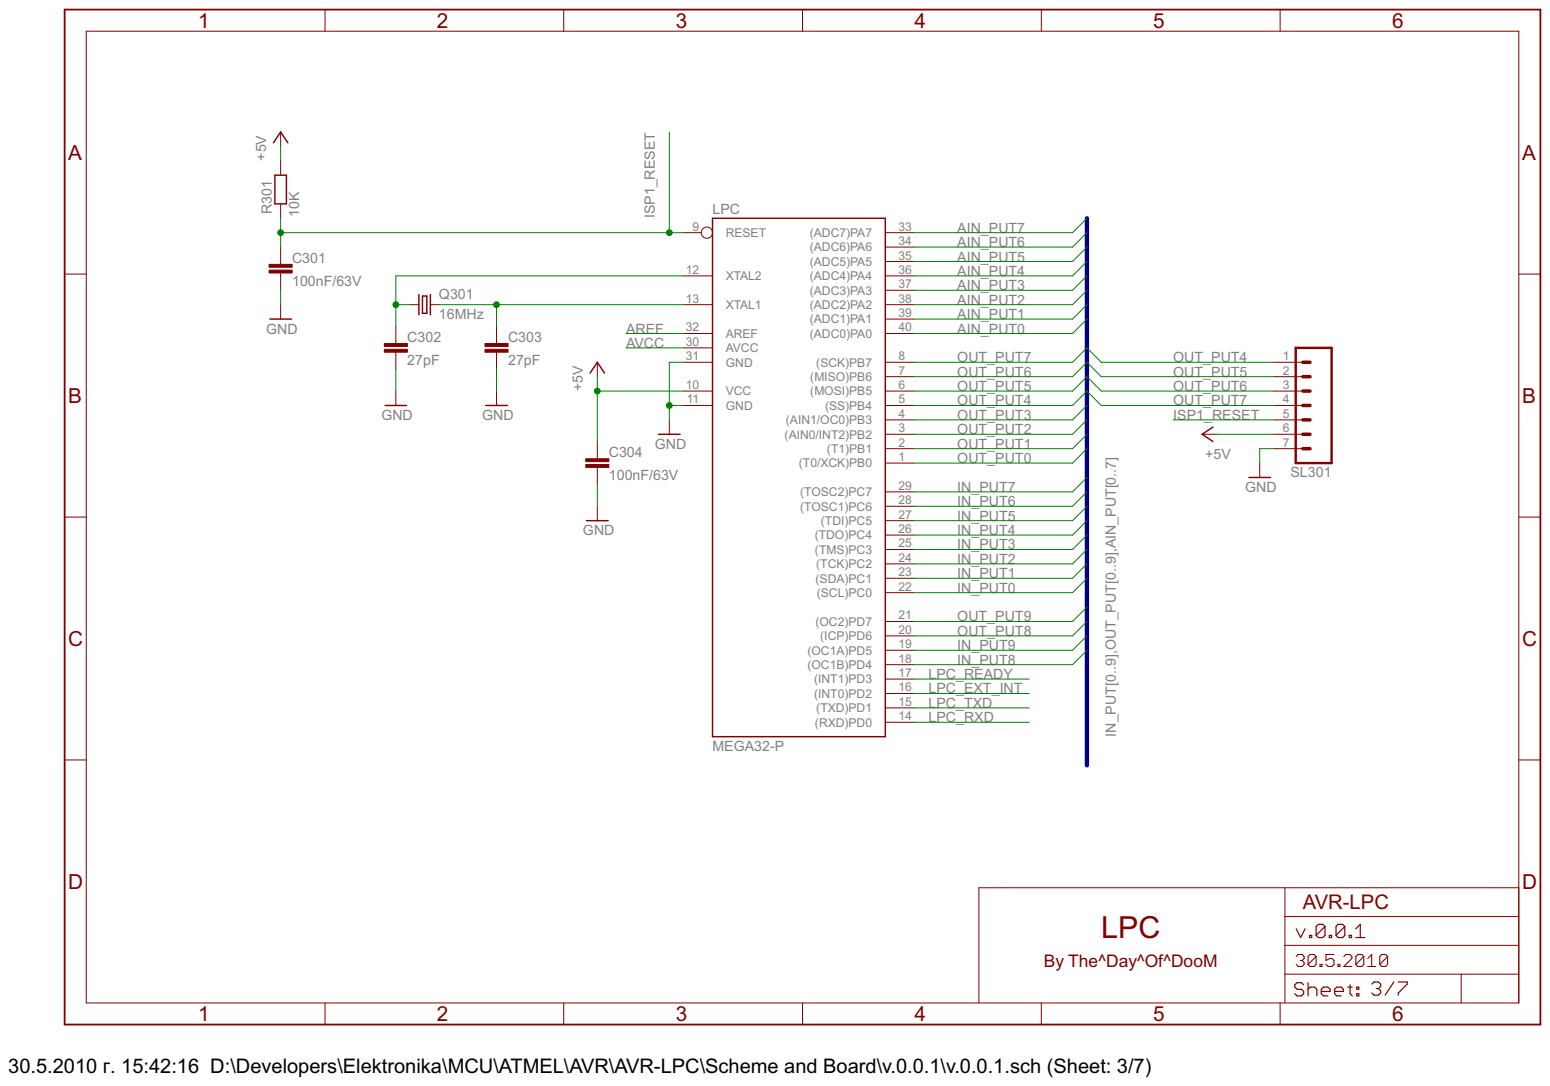
[picture p51: page 3]

By The^Day^Of^DooM

30.5.2010 г. 15:42:16 D:\Developers\Elektronika\MCU\ATMEL\AVR\AVR-LPC\Scheme and Board\v.0.0.1\v.0.0.1.sch (Sheet: 3/7)

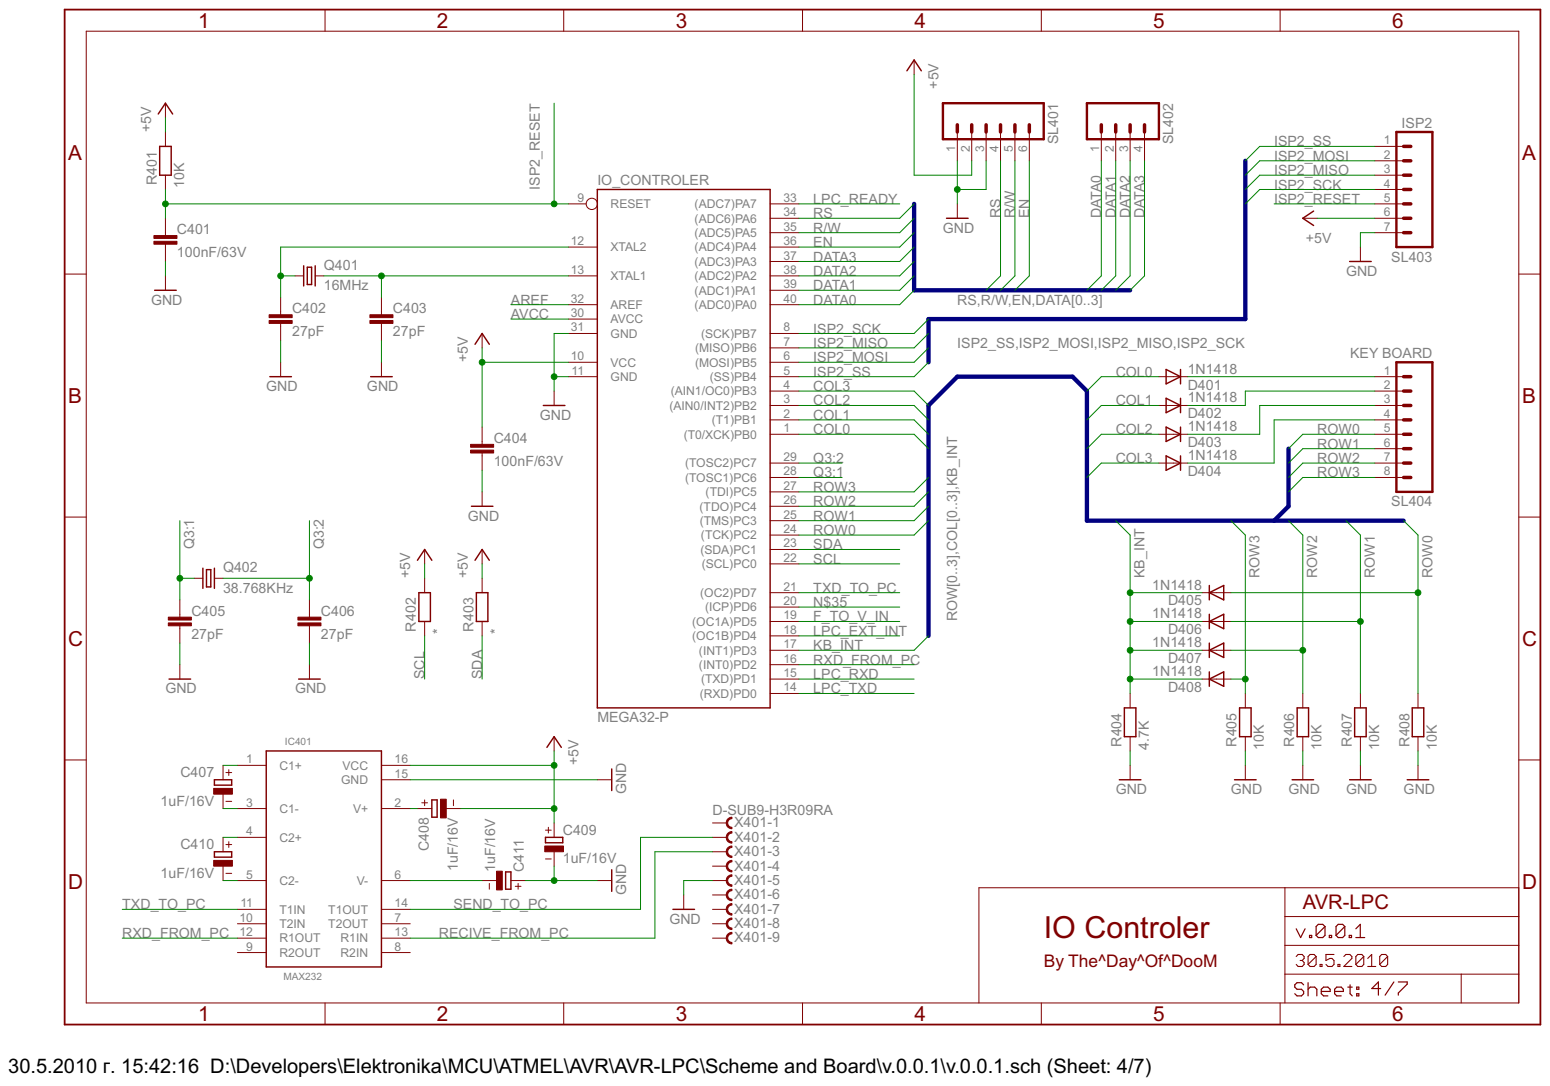
[picture p52: page 4]

W[0..3],COL[0..3],KB_INT RS,R/W,EN,DATA[0..3]

By The^Day^Of^DooM

30.5.2010 г. 15:42:16 D:\Developers\Elektronika\MCU\ATMEL\AVR\AVR-LPC\Scheme and Board\v.0.0.1\v.0.0.1.sch (Sheet: 4/7)

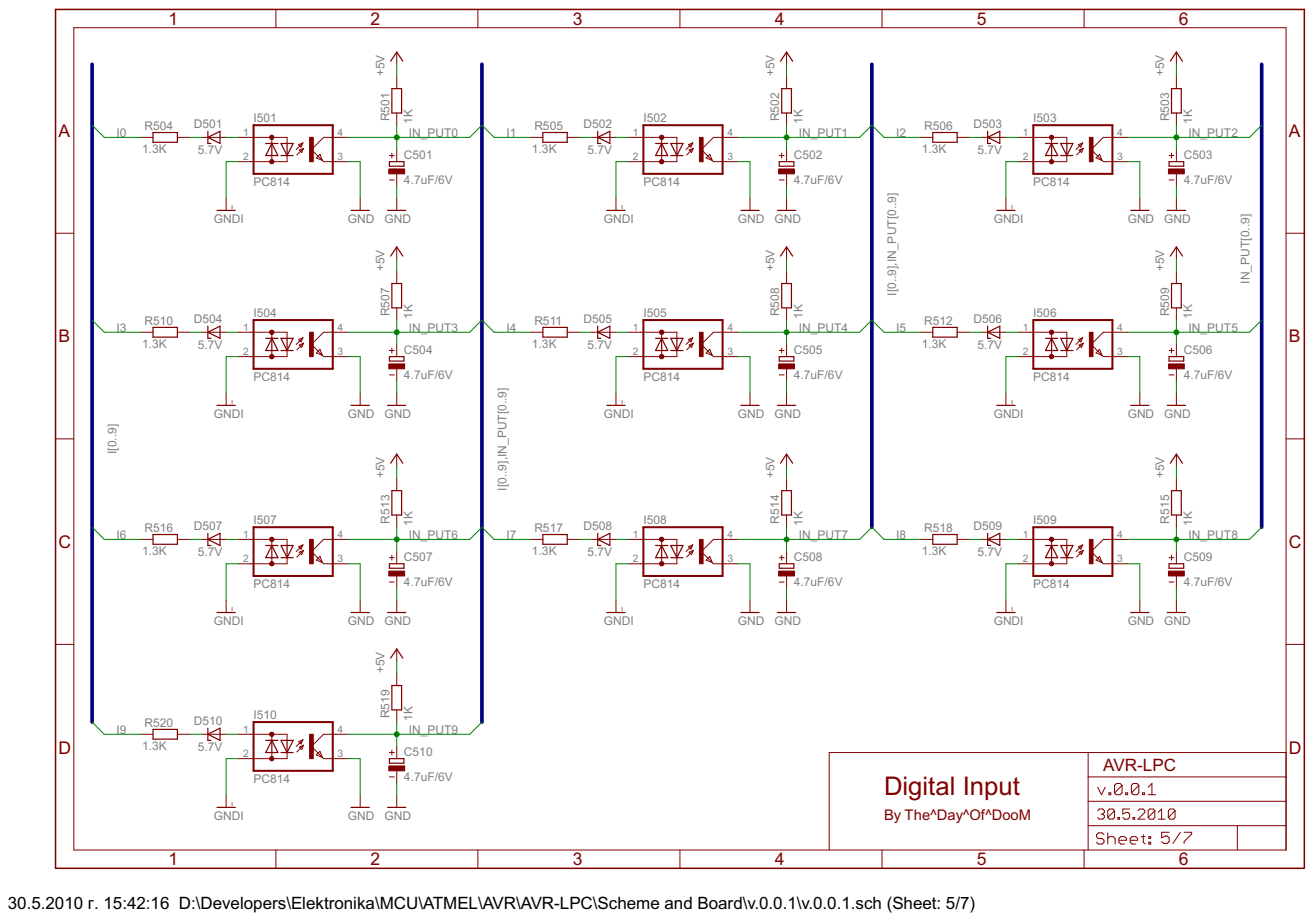
[picture p53: page 5]

By The^Day^Of^DooM

30.5.2010 г. 15:42:16 D:\Developers\Elektronika\MCU\ATMEL\AVR\AVR-LPC\Scheme and Board\v.0.0.1\v.0.0.1.sch (Sheet: 5/7)

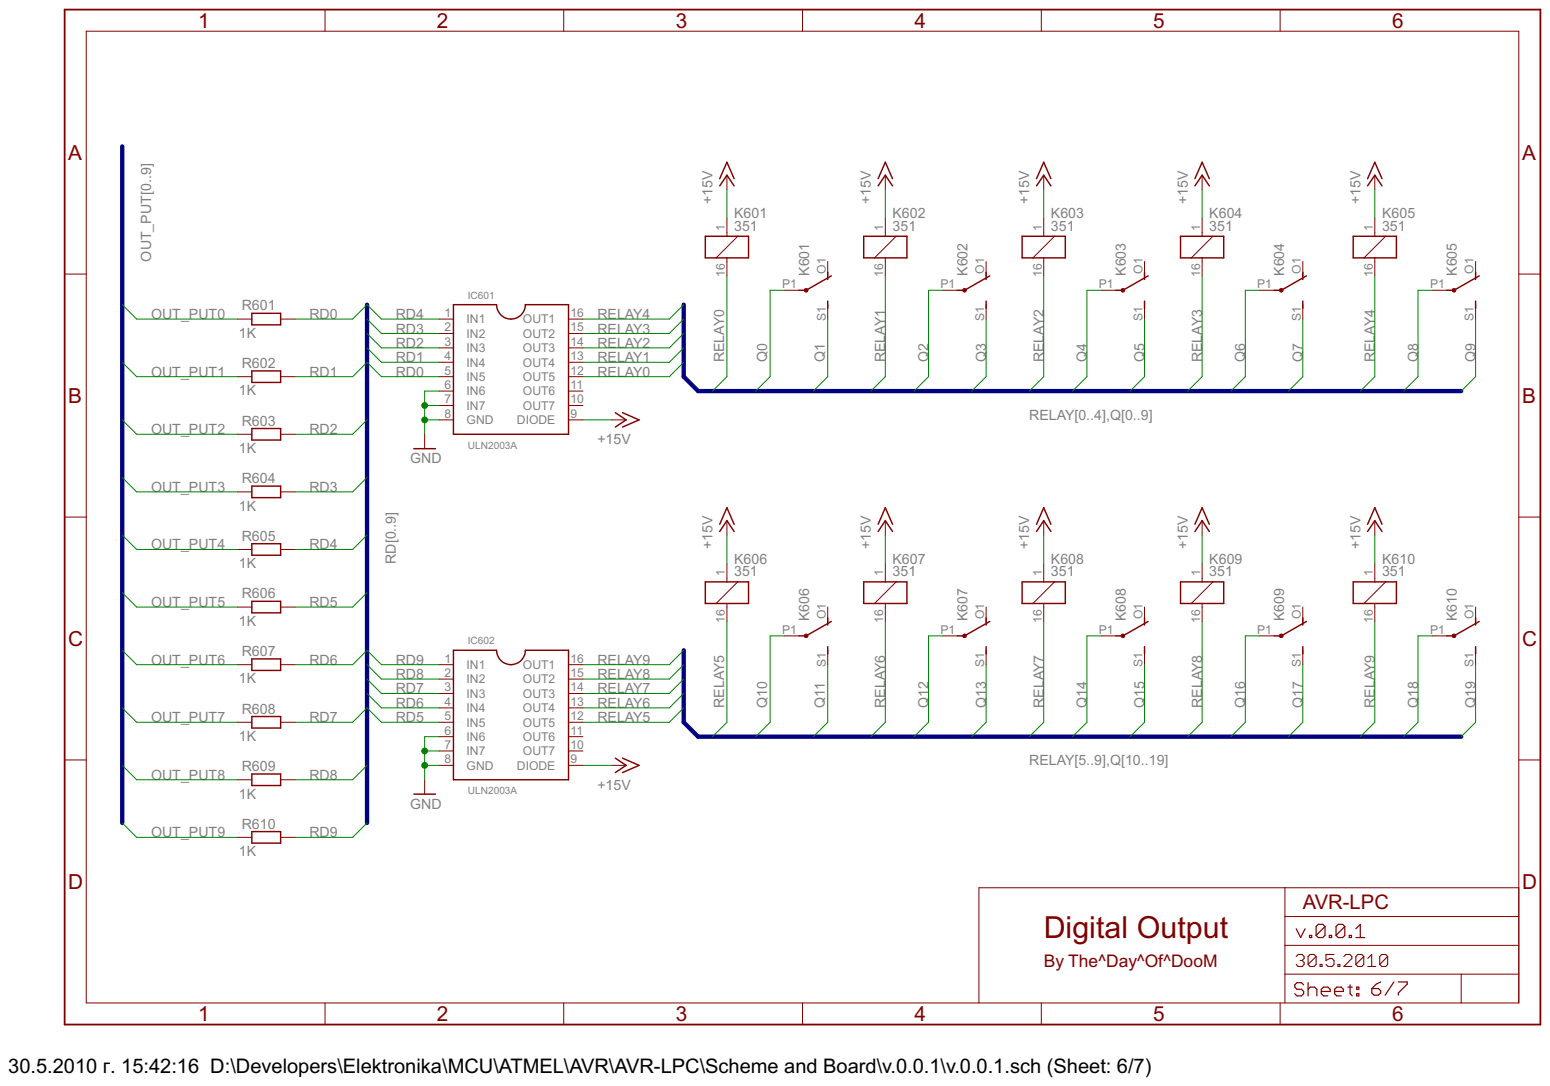
[picture p54: page 6]

By The^Day^Of^DooM

30.5.2010 г. 15:42:16 D:\Developers\Elektronika\MCU\ATMEL\AVR\AVR-LPC\Scheme and Board\v.0.0.1\v.0.0.1.sch (Sheet: 6/7)

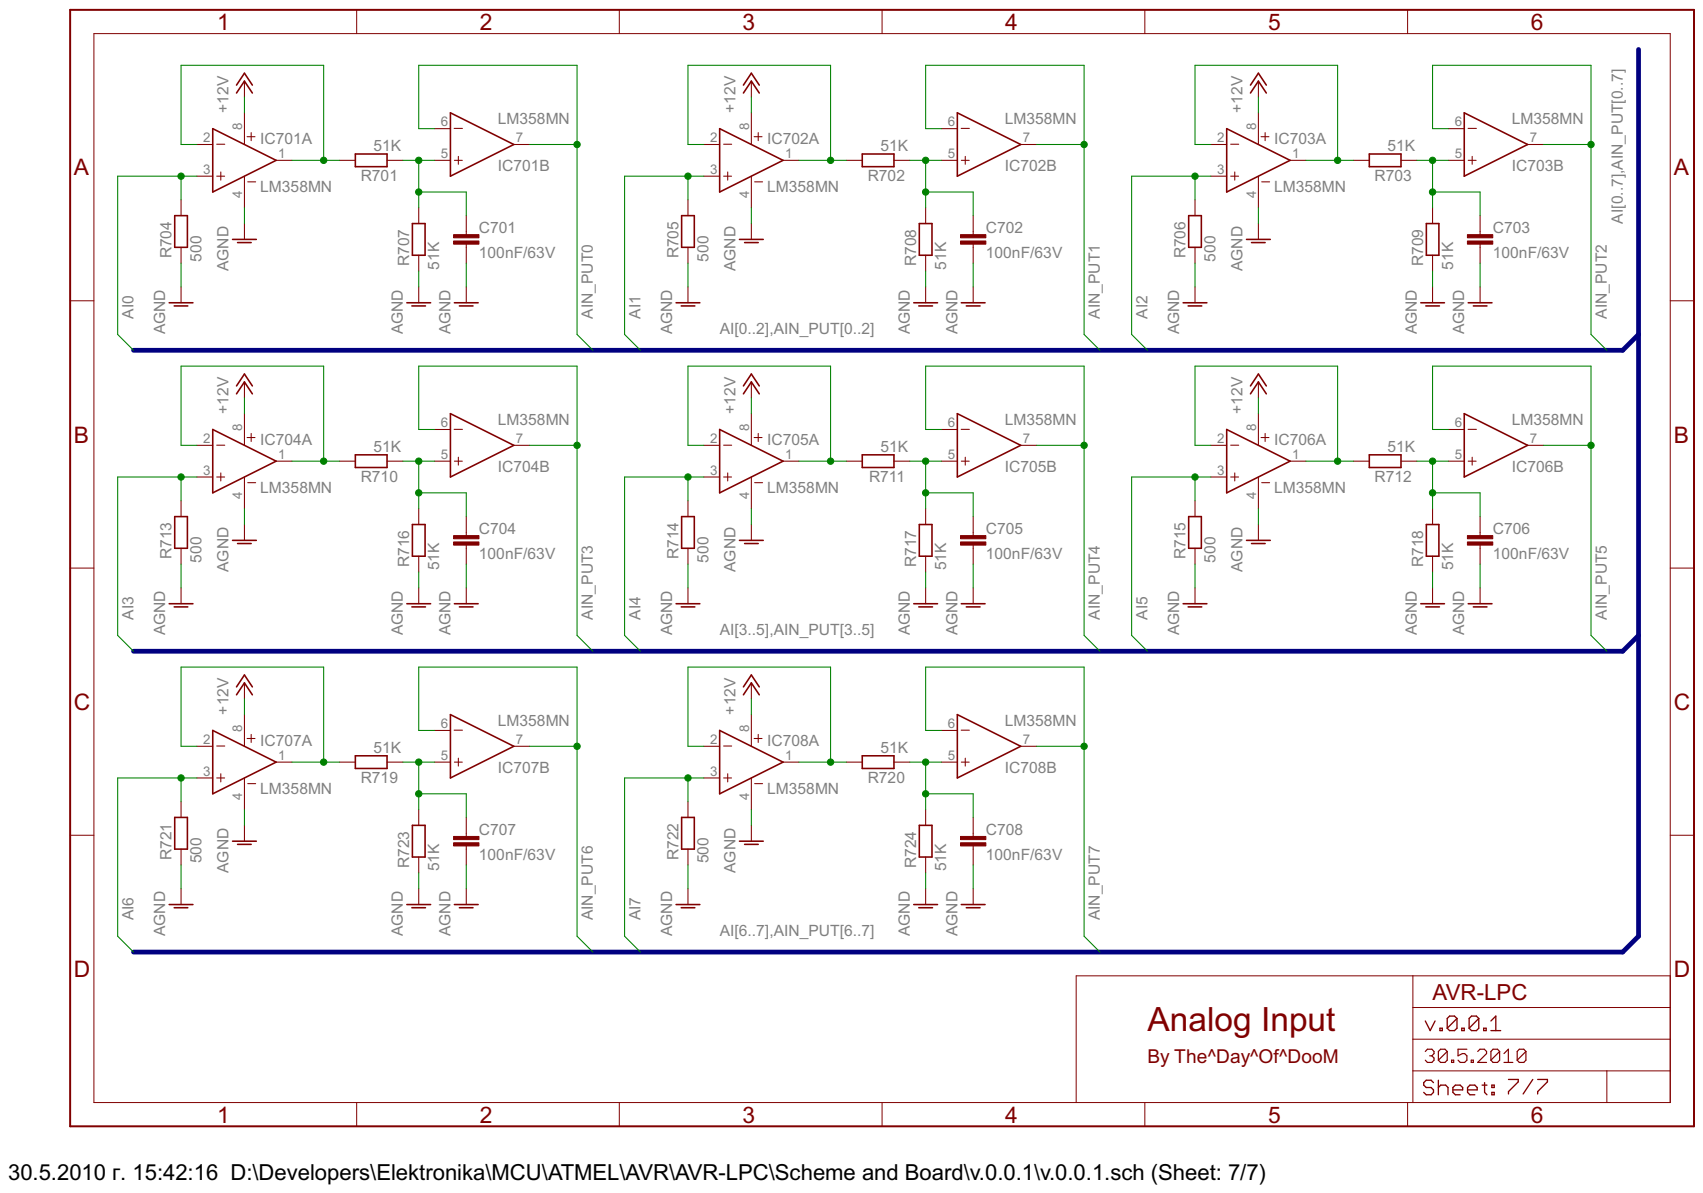
[picture p55: page 7]

By The^Day^Of^DooM

30.5.2010 г. 15:42:16 D:\Developers\Elektronika\MCU\ATMEL\AVR\AVR-LPC\Scheme and Board\v.0.0.1\v.0.0.1.sch (Sheet: 7/7)
