SimeonSimeonovIvanov/AVR-LPC/Scheme and Board/v.0.0.2/v.0.0.2 (Bottom Side).pdf

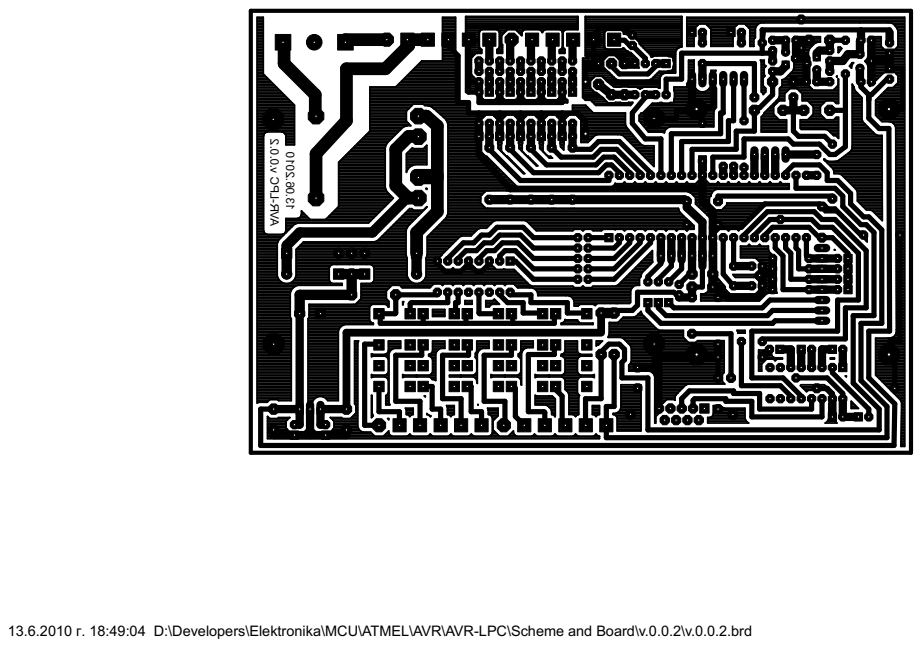
[picture p56: page 1]

13.6.2010 г. 18:49:04 D:\Developers\Elektronika\MCU\ATMEL\AVR\AVR-LPC\Scheme and Board\v.0.0.2\v.0.0.2.brd
