SimeonSimeonovIvanov/AVR-LPC/Scheme and Board/v.0.0.2/v.0.0.2.pdf

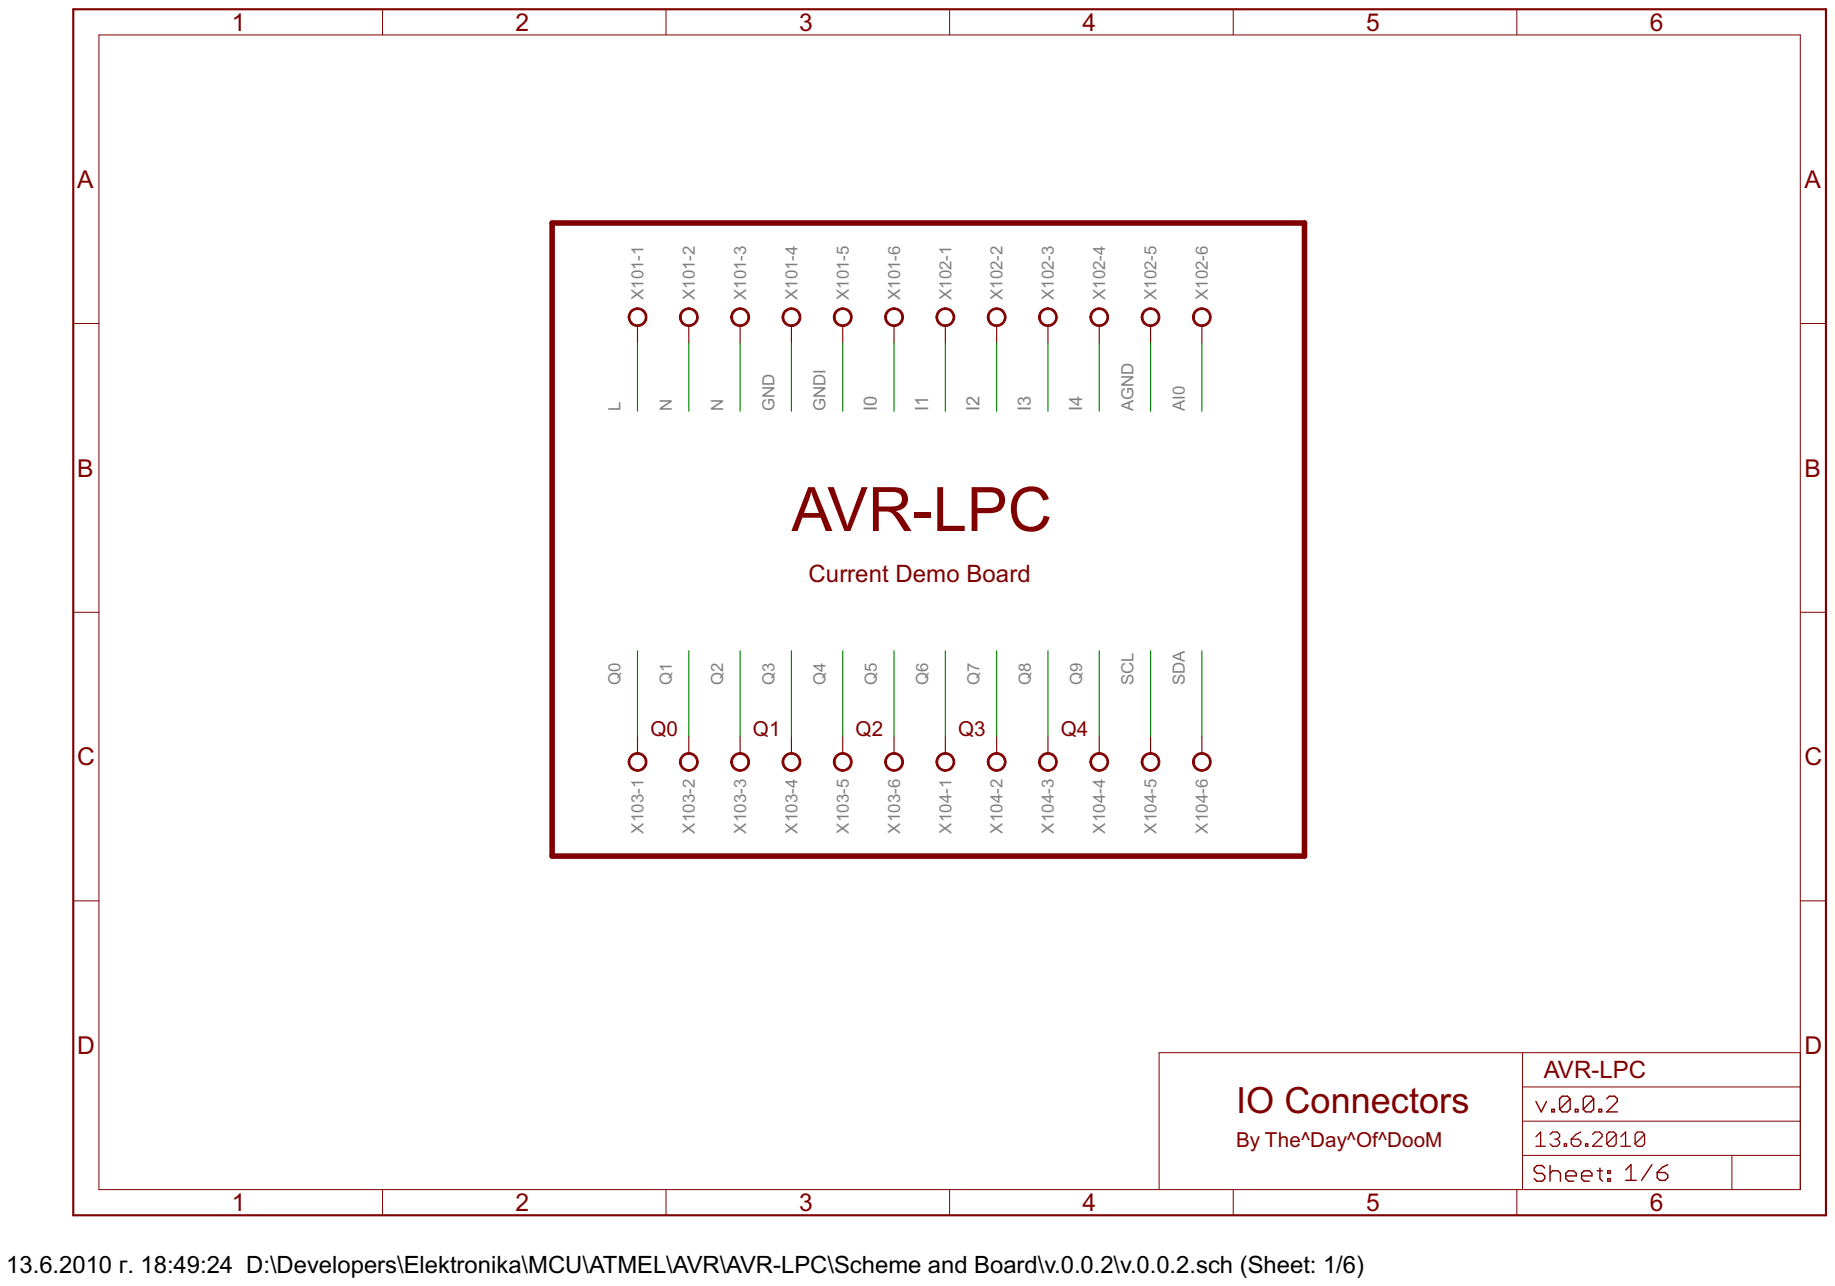
[picture p57: page 1]

By The^Day^Of^DooM

13.6.2010 г. 18:49:24 D:\Developers\Elektronika\MCU\ATMEL\AVR\AVR-LPC\Scheme and Board\v.0.0.2\v.0.0.2.sch (Sheet: 1/6)

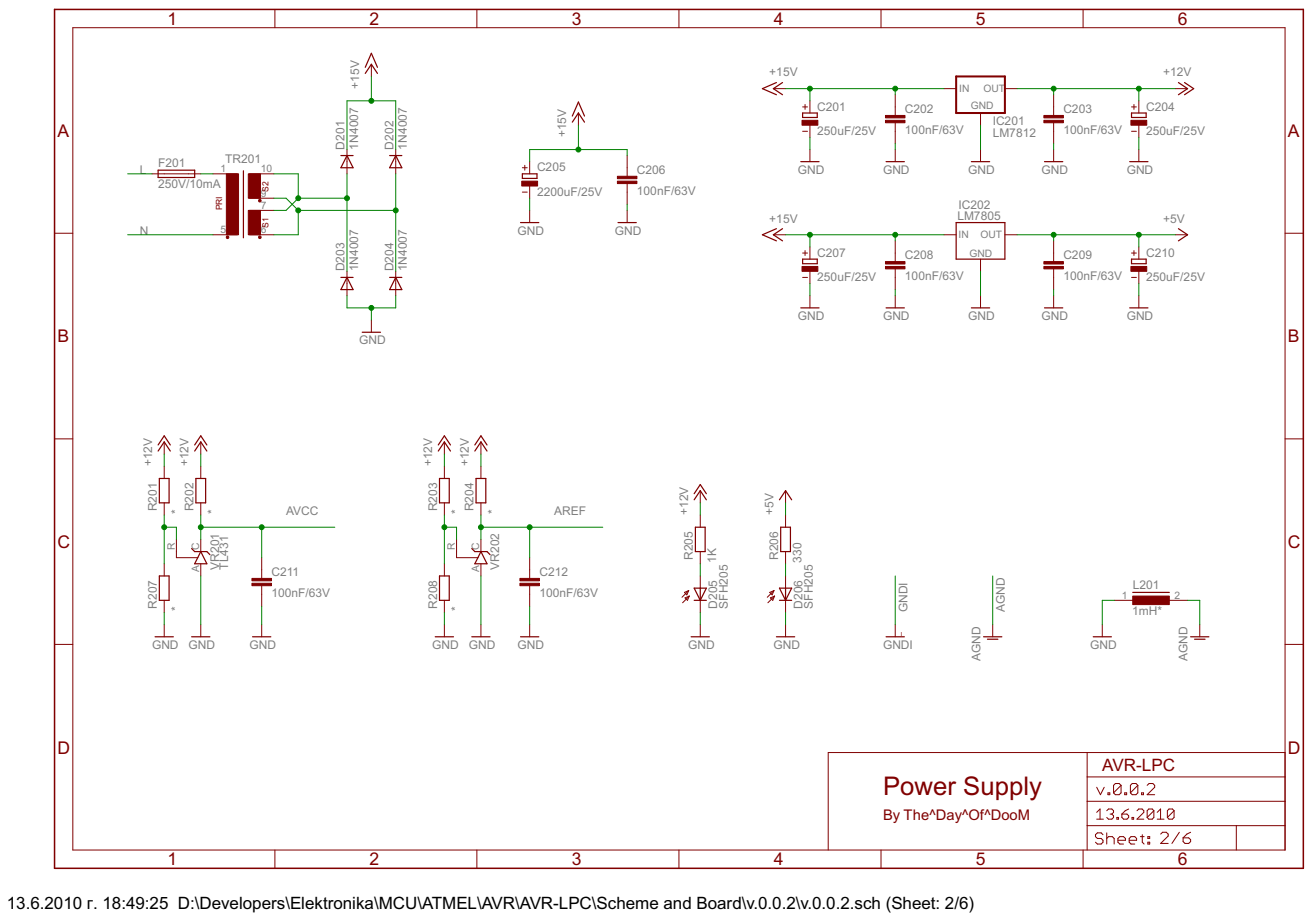
[picture p58: page 2]

By The^Day^Of^DooM

13.6.2010 г. 18:49:25 D:\Developers\Elektronika\MCU\ATMEL\AVR\AVR-LPC\Scheme and Board\v.0.0.2\v.0.0.2.sch (Sheet: 2/6)

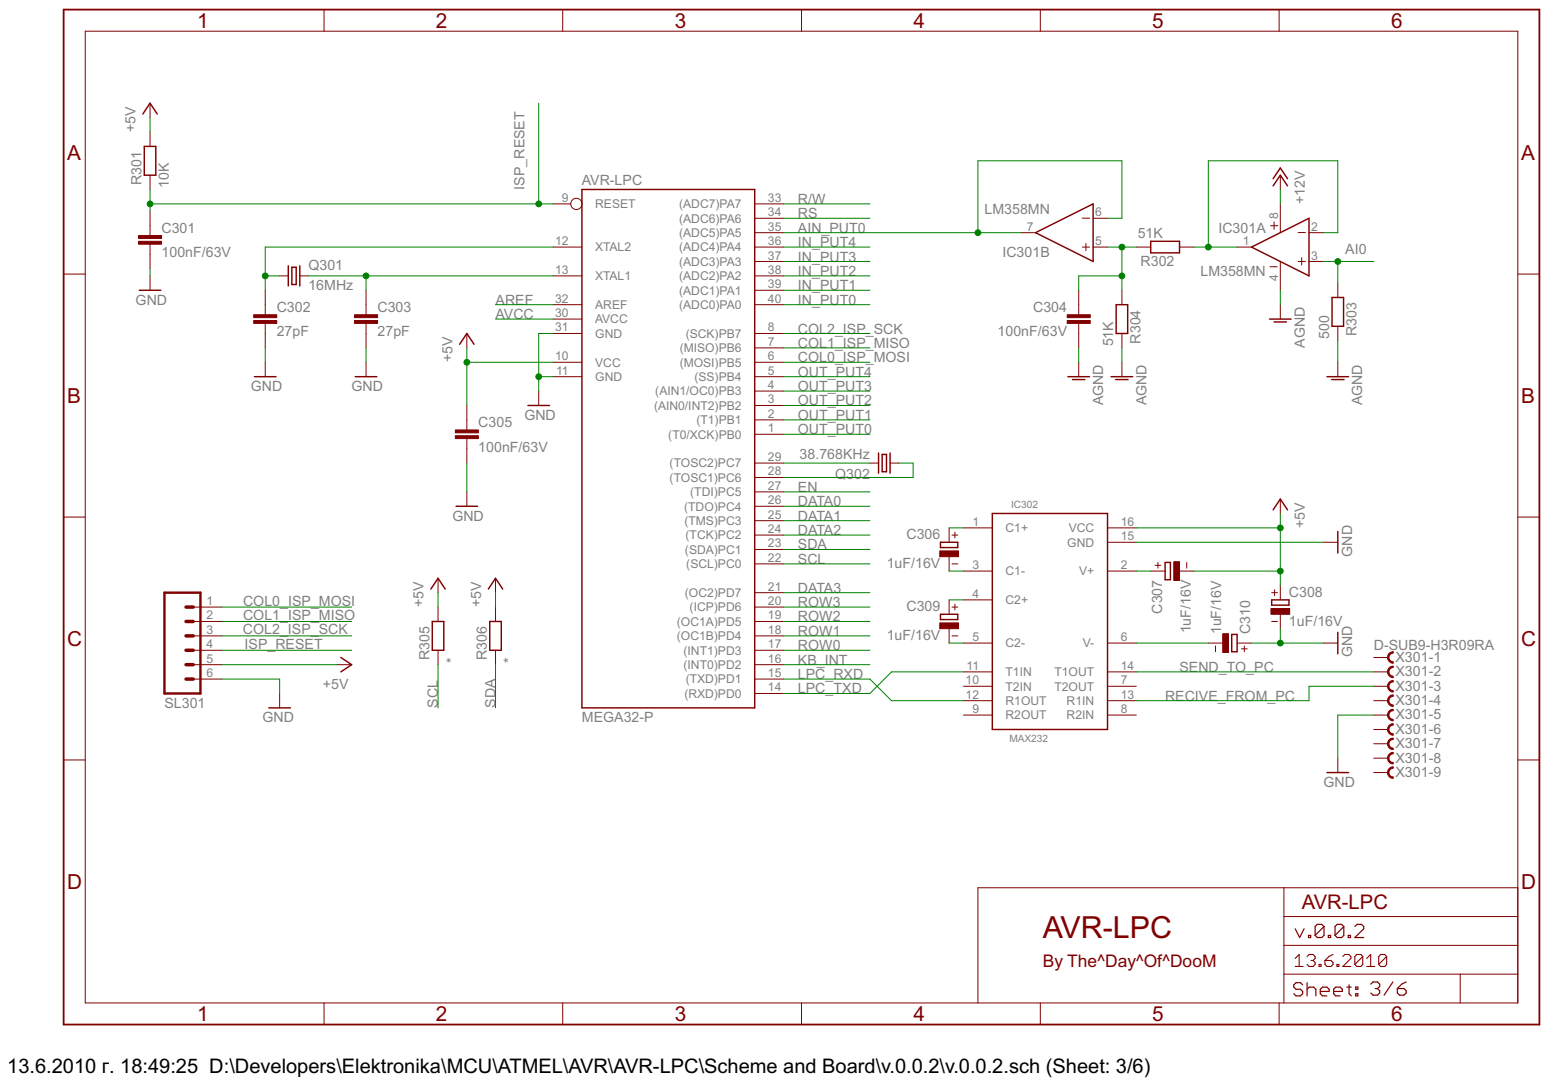
[picture p59: page 3]

By The^Day^Of^DooM

13.6.2010 г. 18:49:25 D:\Developers\Elektronika\MCU\ATMEL\AVR\AVR-LPC\Scheme and Board\v.0.0.2\v.0.0.2.sch (Sheet: 3/6)

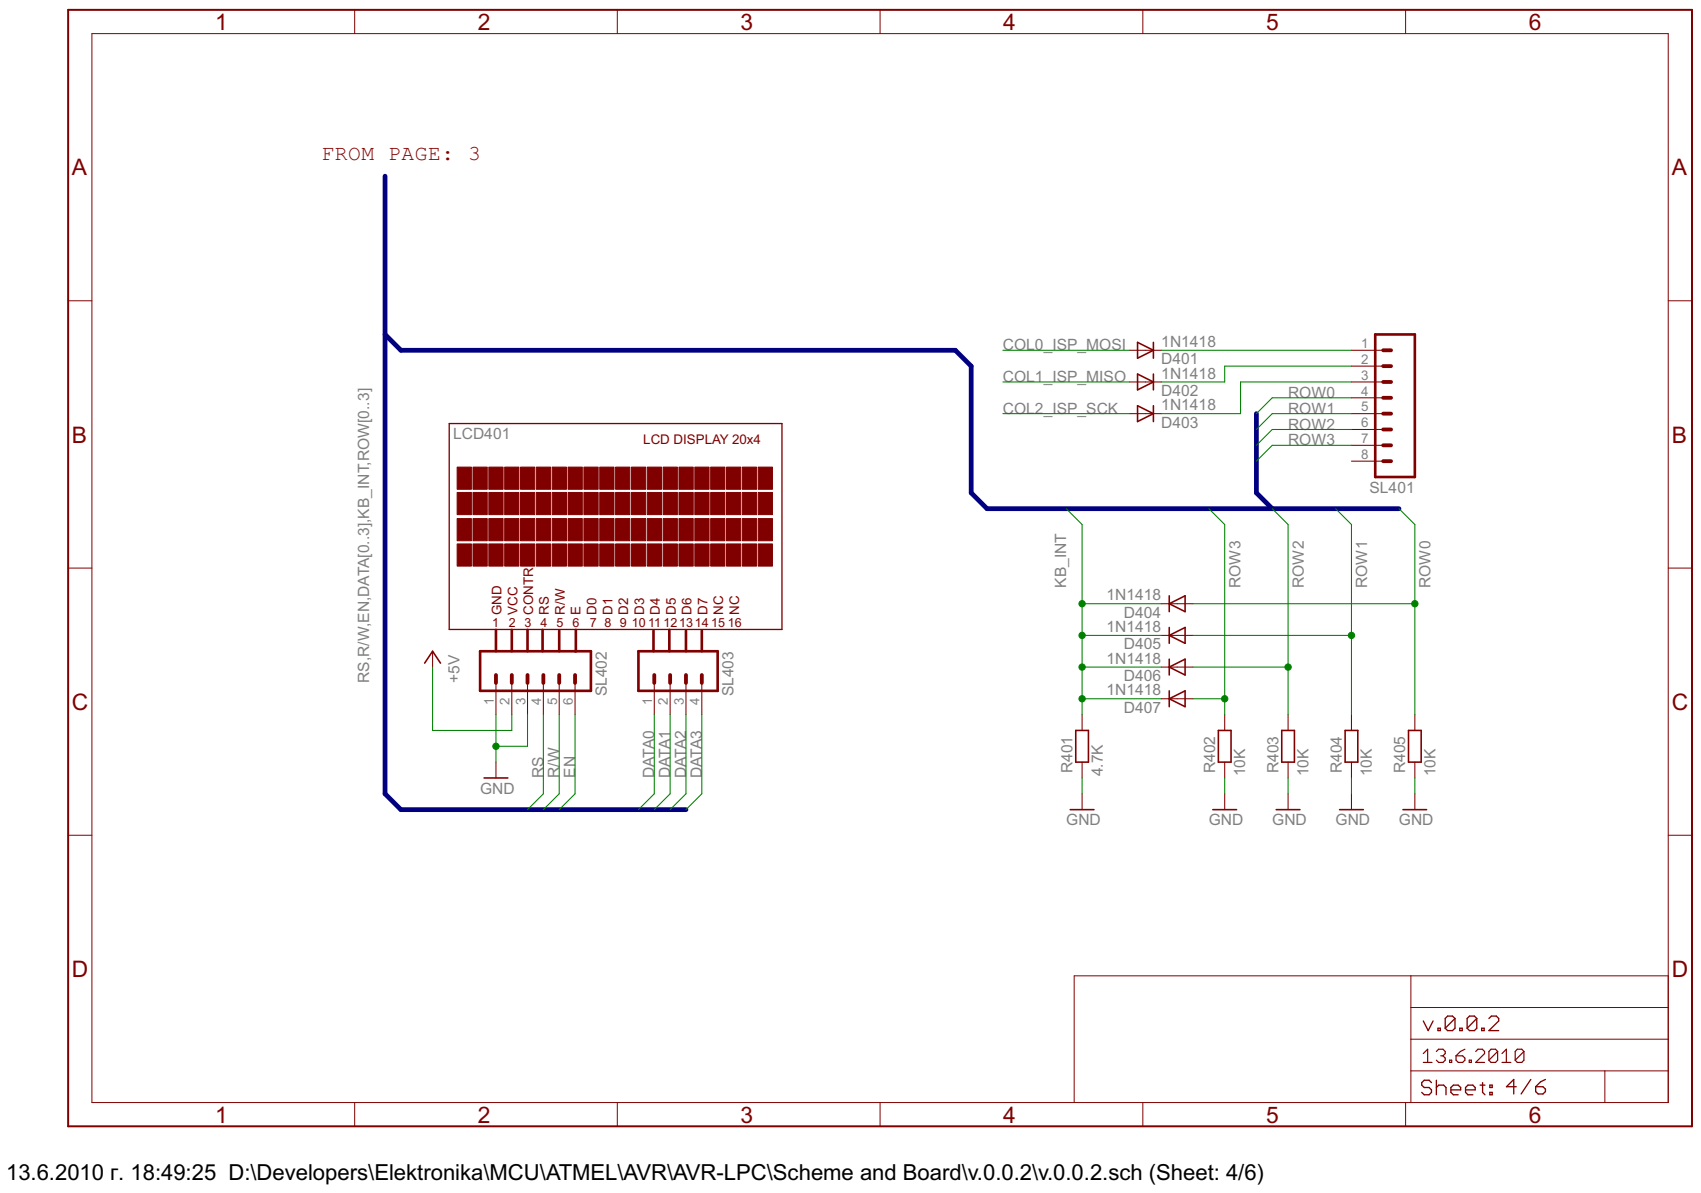
[picture p60: page 4]

RS,R/W,EN,DATA[0..3],KB_INT,RO

13.6.2010 г. 18:49:25 D:\Developers\Elektronika\MCU\ATMEL\AVR\AVR-LPC\Scheme and Board\v.0.0.2\v.0.0.2.sch (Sheet: 4/6)

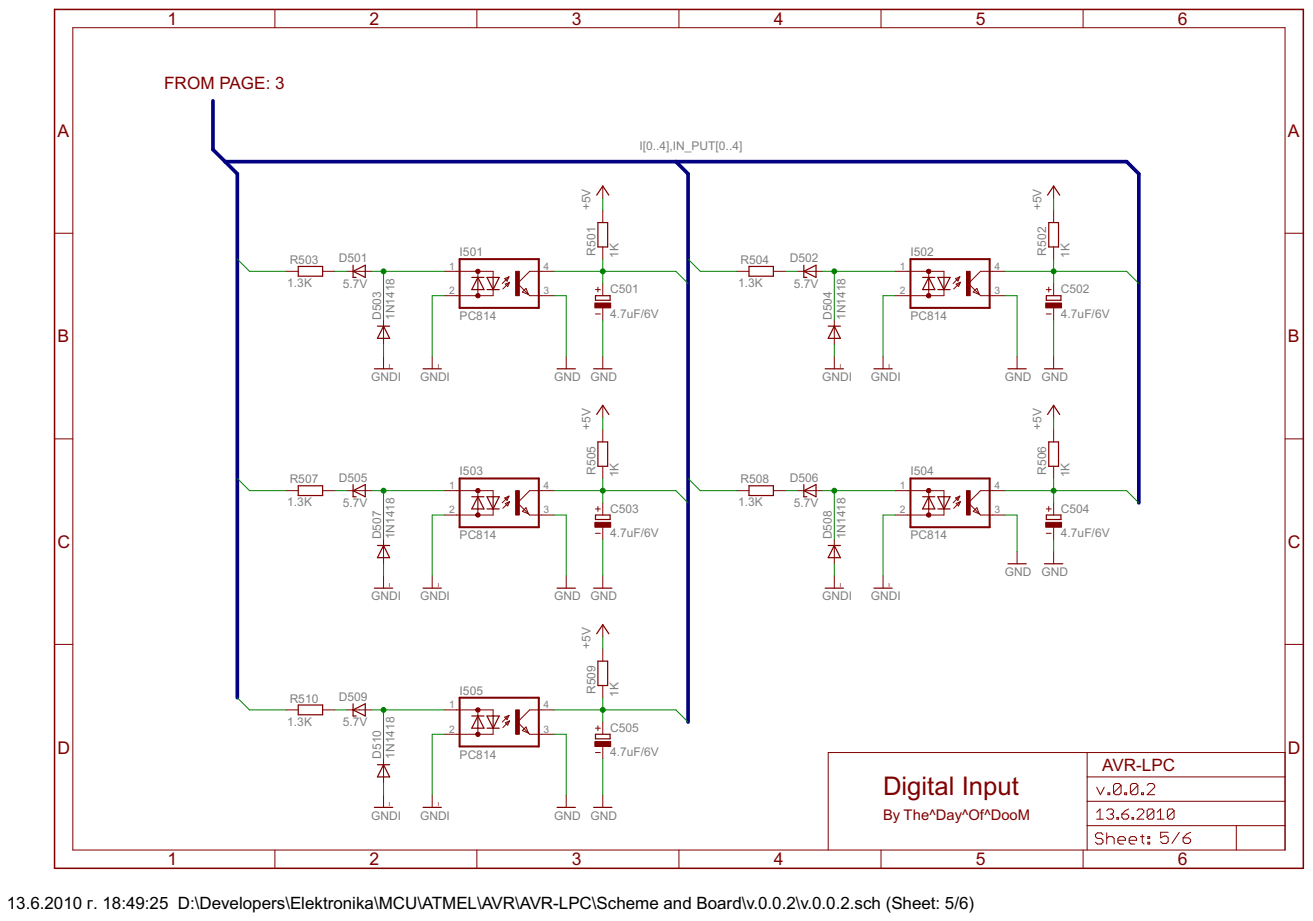
[picture p61: page 5]

By The^Day^Of^DooM

13.6.2010 г. 18:49:25 D:\Developers\Elektronika\MCU\ATMEL\AVR\AVR-LPC\Scheme and Board\v.0.0.2\v.0.0.2.sch (Sheet: 5/6)

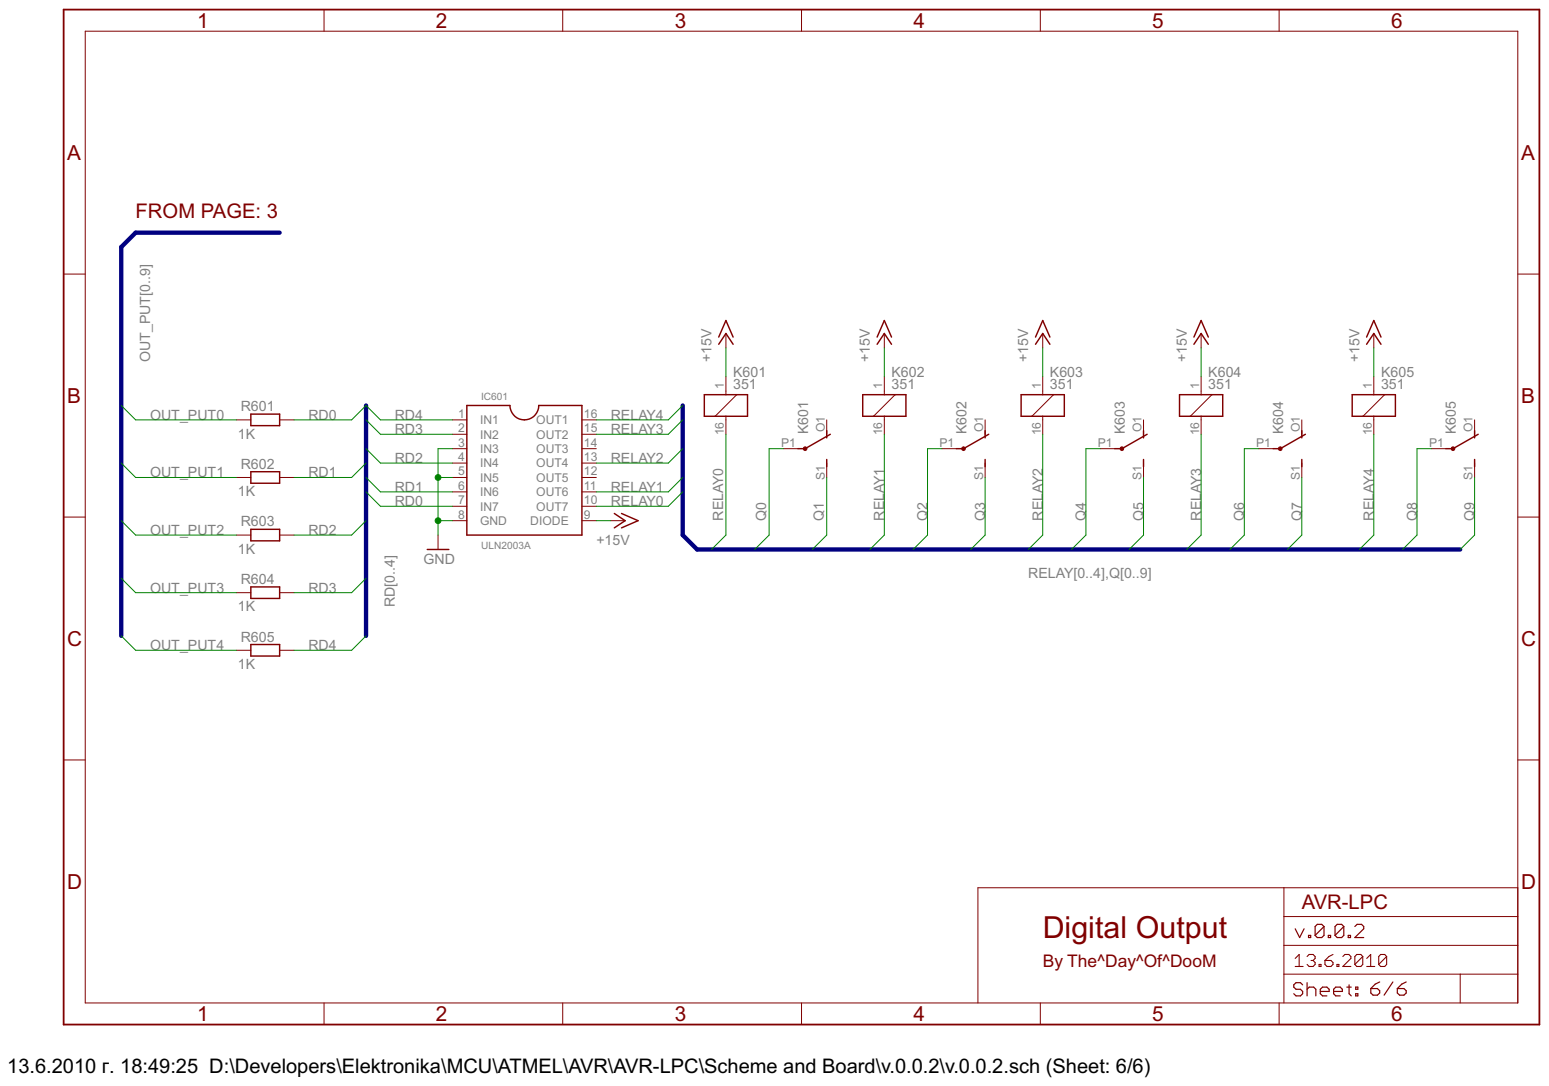
[picture p62: page 6]

By The^Day^Of^DooM

13.6.2010 г. 18:49:25 D:\Developers\Elektronika\MCU\ATMEL\AVR\AVR-LPC\Scheme and Board\v.0.0.2\v.0.0.2.sch (Sheet: 6/6)
