SimeonSimeonovIvanov/AVR-LPC/Scheme and Board/v.0.0.3/v.0.0.3.pdf

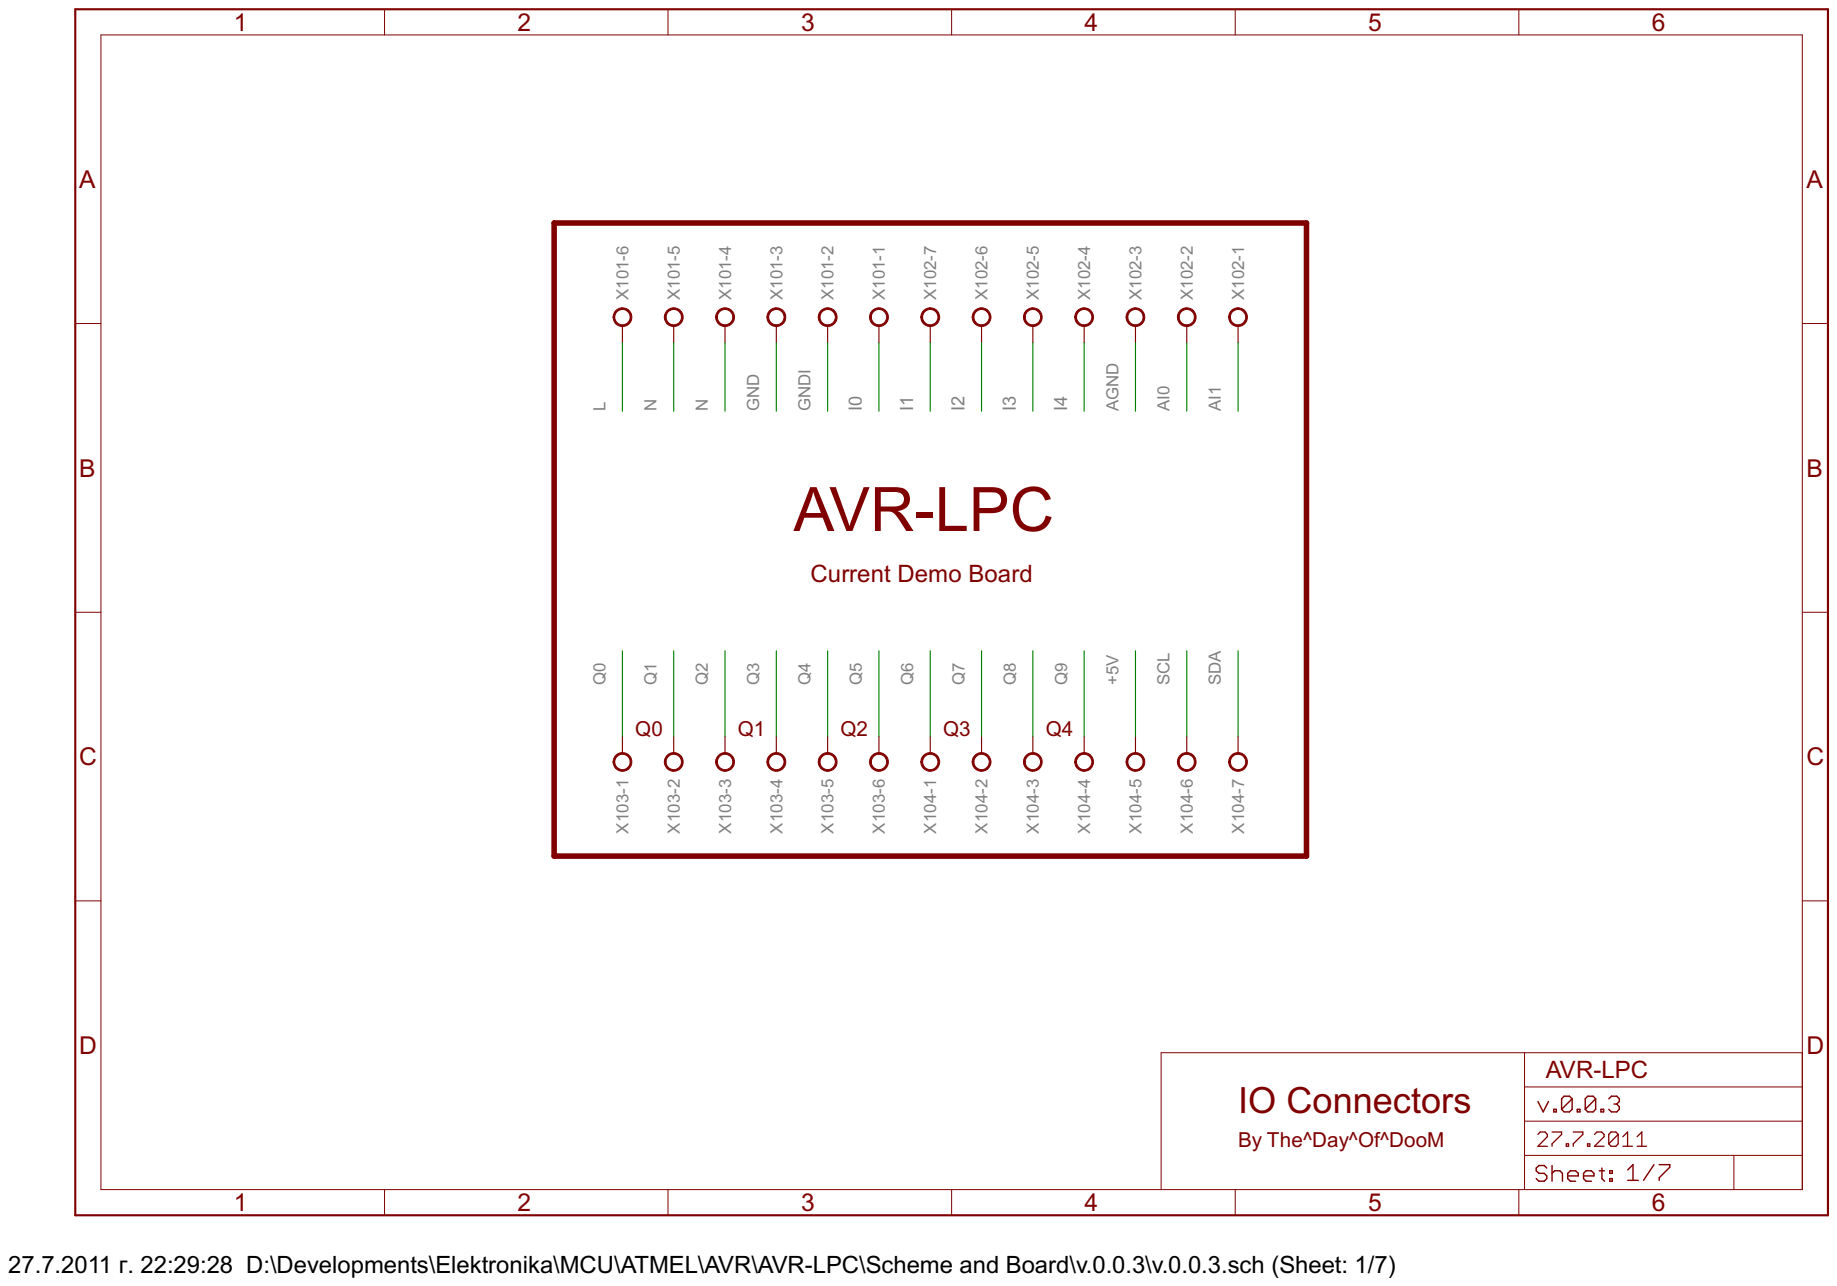
[picture p63: page 1]

By The^Day^Of^DooM

27.7.2011 г. 22:29:28 D:\Developments\Elektronika\MCU\ATMEL\AVR\AVR-LPC\Scheme and Board\v.0.0.3\v.0.0.3.sch (Sheet: 1/7)

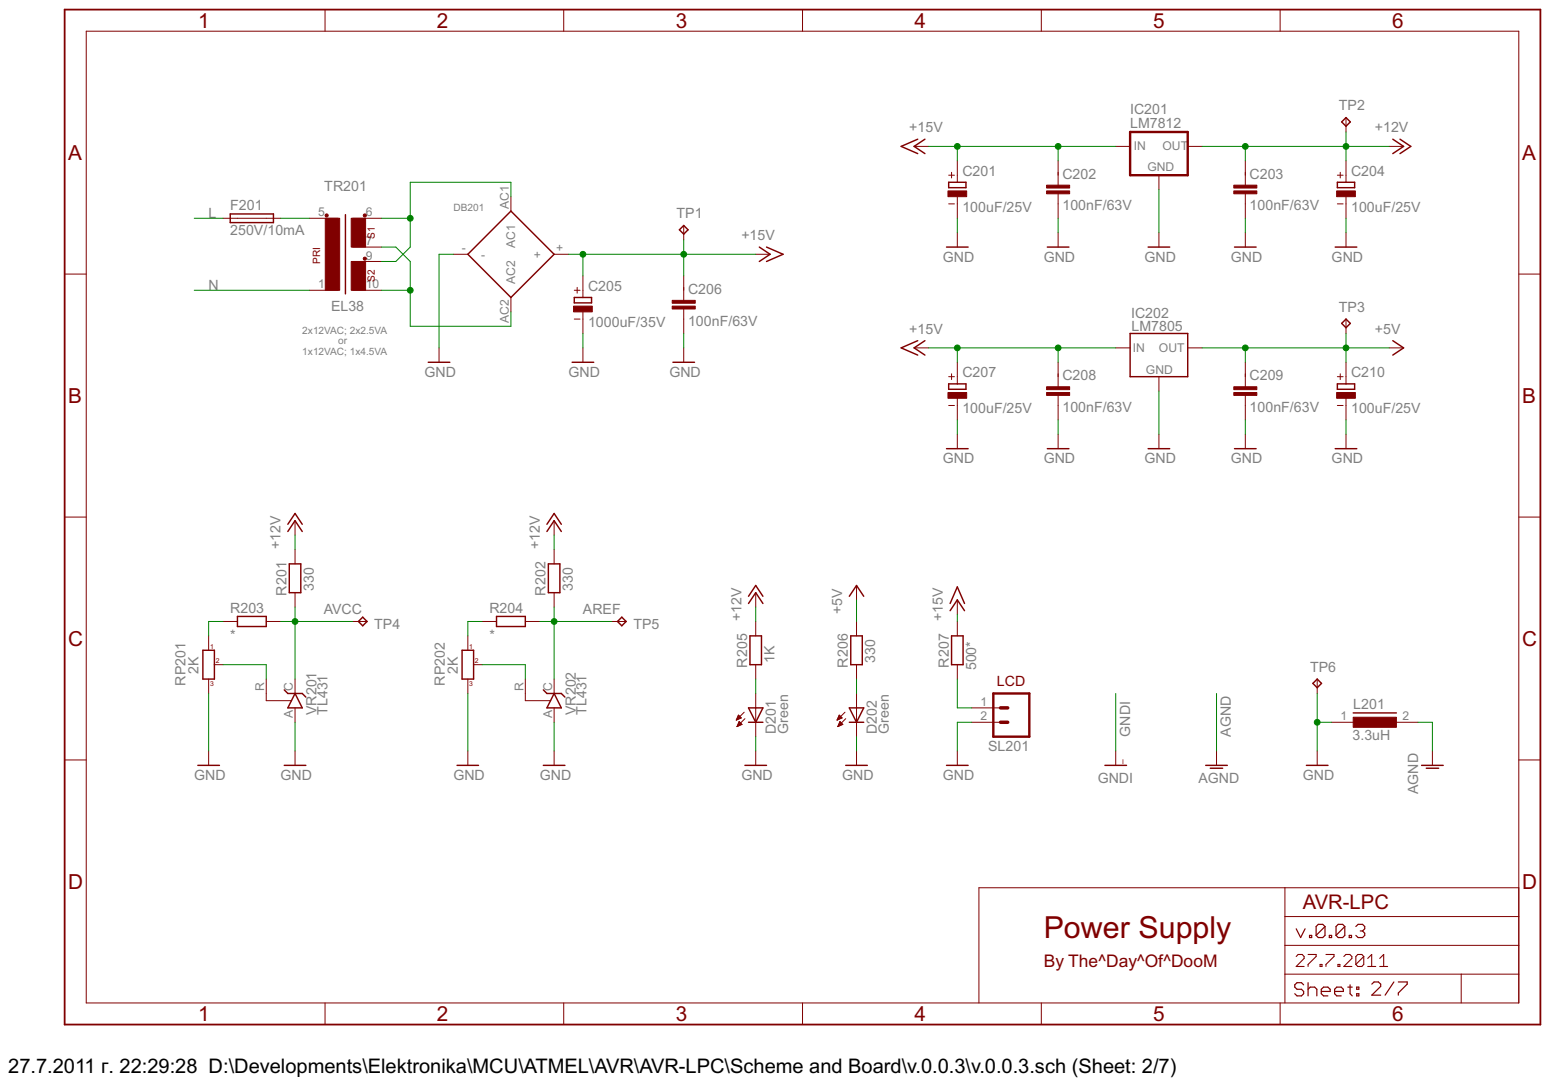
[picture p64: page 2]

By The^Day^Of^DooM

27.7.2011 г. 22:29:28 D:\Developments\Elektronika\MCU\ATMEL\AVR\AVR-LPC\Scheme and Board\v.0.0.3\v.0.0.3.sch (Sheet: 2/7)

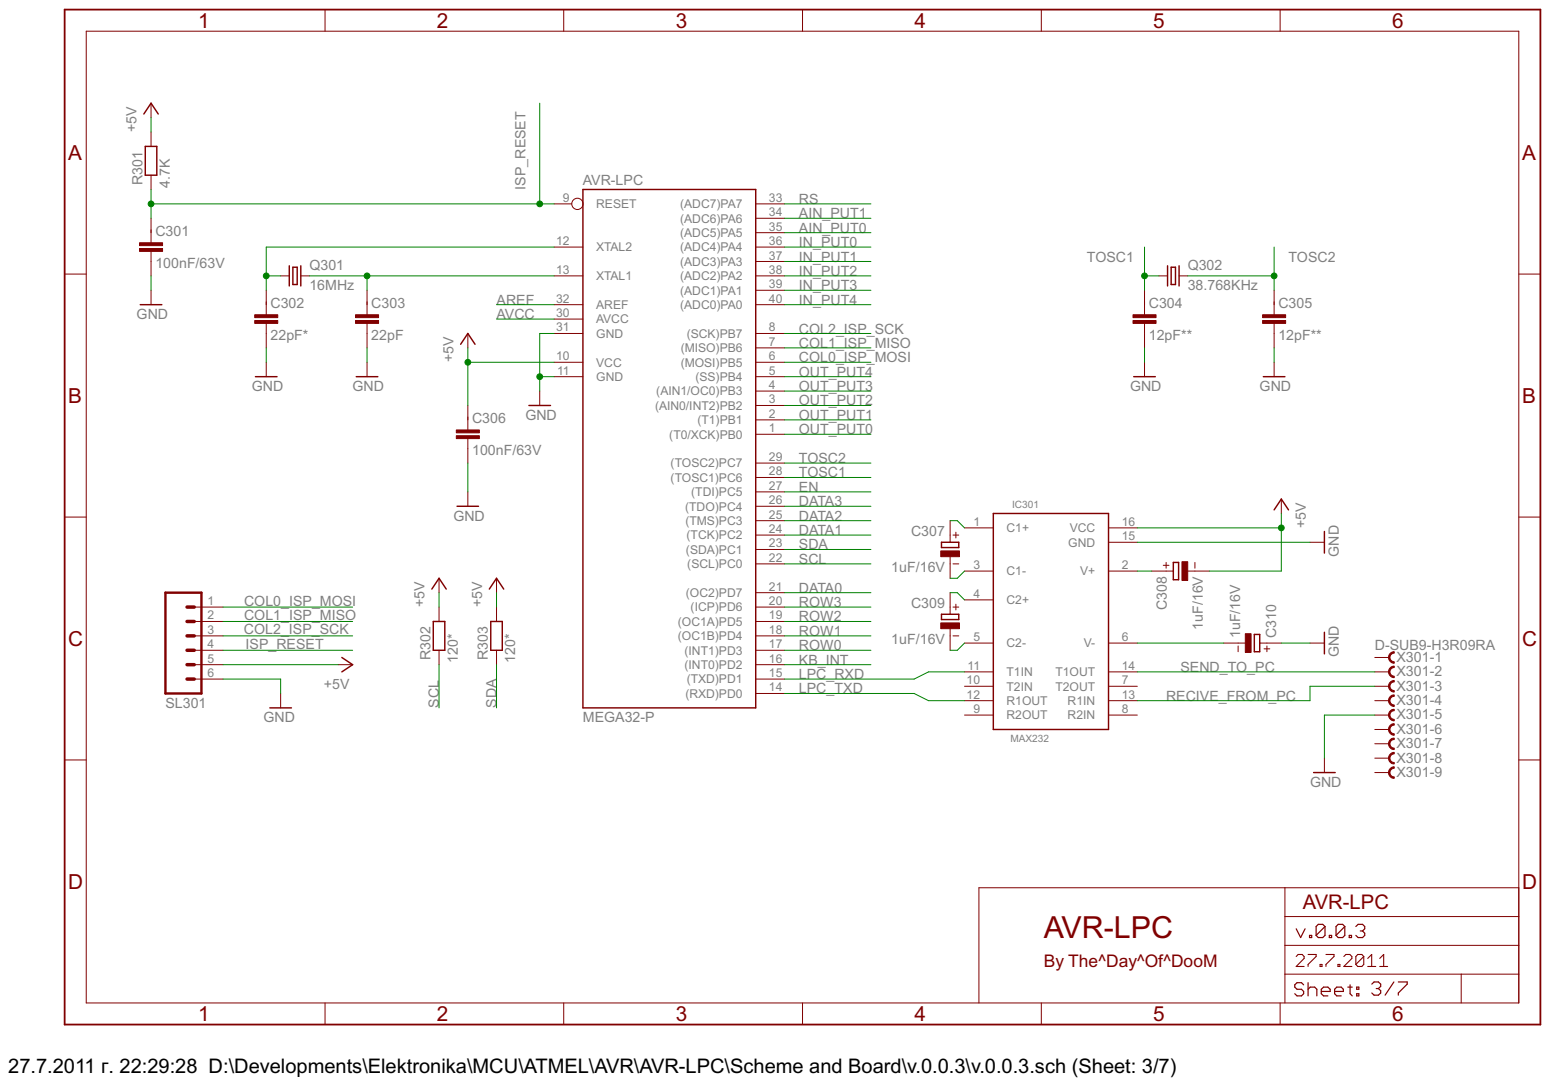
[picture p65: page 3]

By The^Day^Of^DooM

27.7.2011 г. 22:29:28 D:\Developments\Elektronika\MCU\ATMEL\AVR\AVR-LPC\Scheme and Board\v.0.0.3\v.0.0.3.sch (Sheet: 3/7)

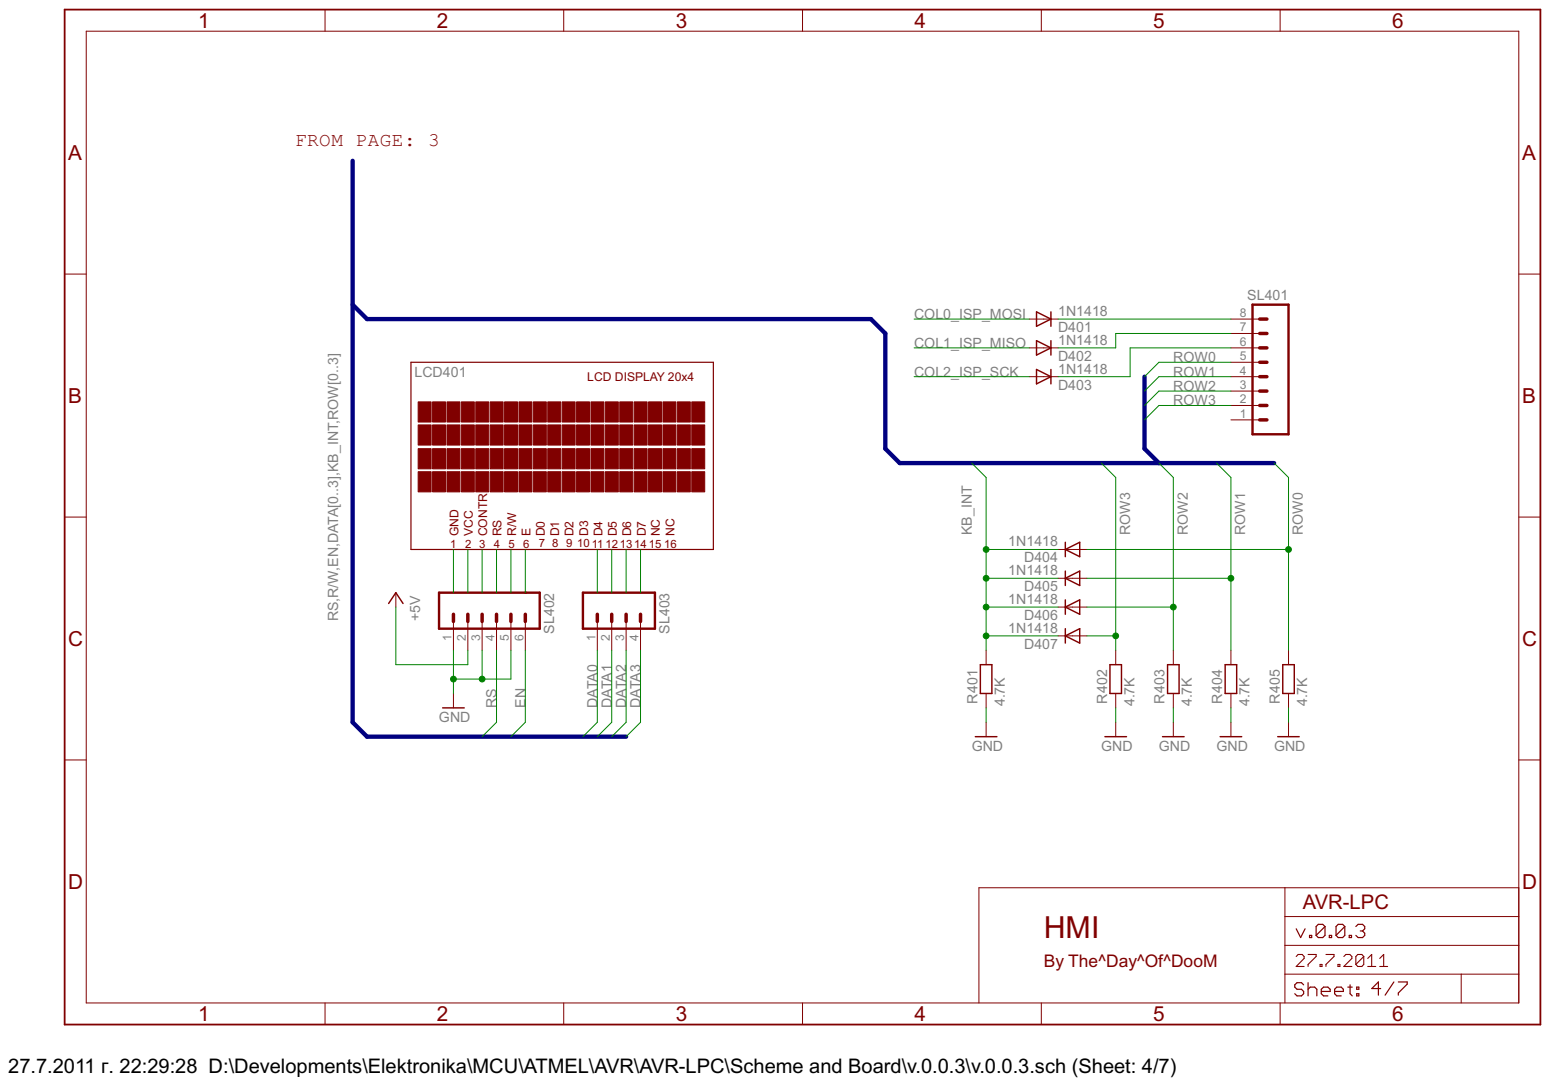
[picture p66: page 4]

RS,R/W,EN,DATA[0..3],KB_INT,RO

By The^Day^Of^DooM

27.7.2011 г. 22:29:28 D:\Developments\Elektronika\MCU\ATMEL\AVR\AVR-LPC\Scheme and Board\v.0.0.3\v.0.0.3.sch (Sheet: 4/7)

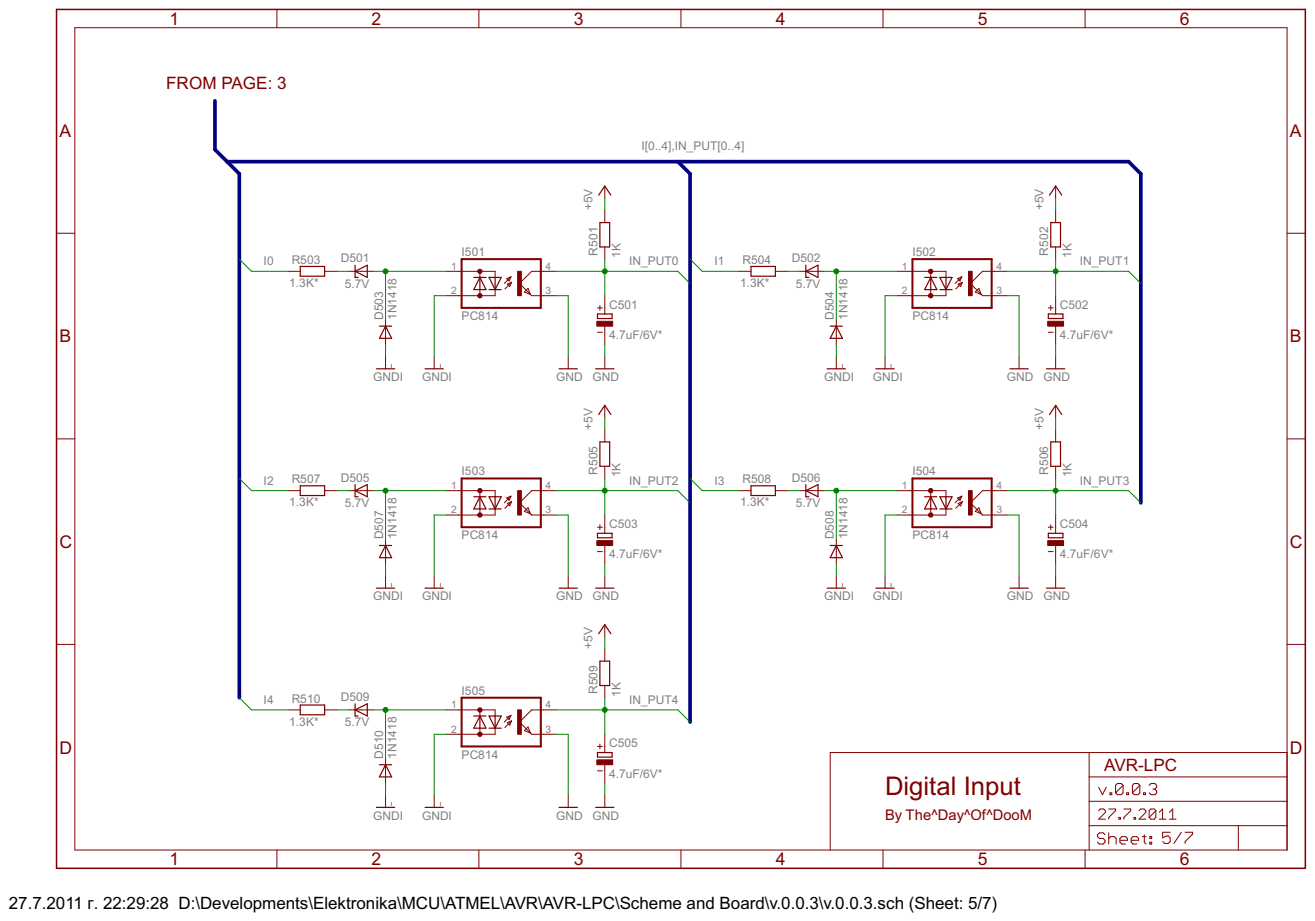
[picture p67: page 5]

By The^Day^Of^DooM

27.7.2011 г. 22:29:28 D:\Developments\Elektronika\MCU\ATMEL\AVR\AVR-LPC\Scheme and Board\v.0.0.3\v.0.0.3.sch (Sheet: 5/7)

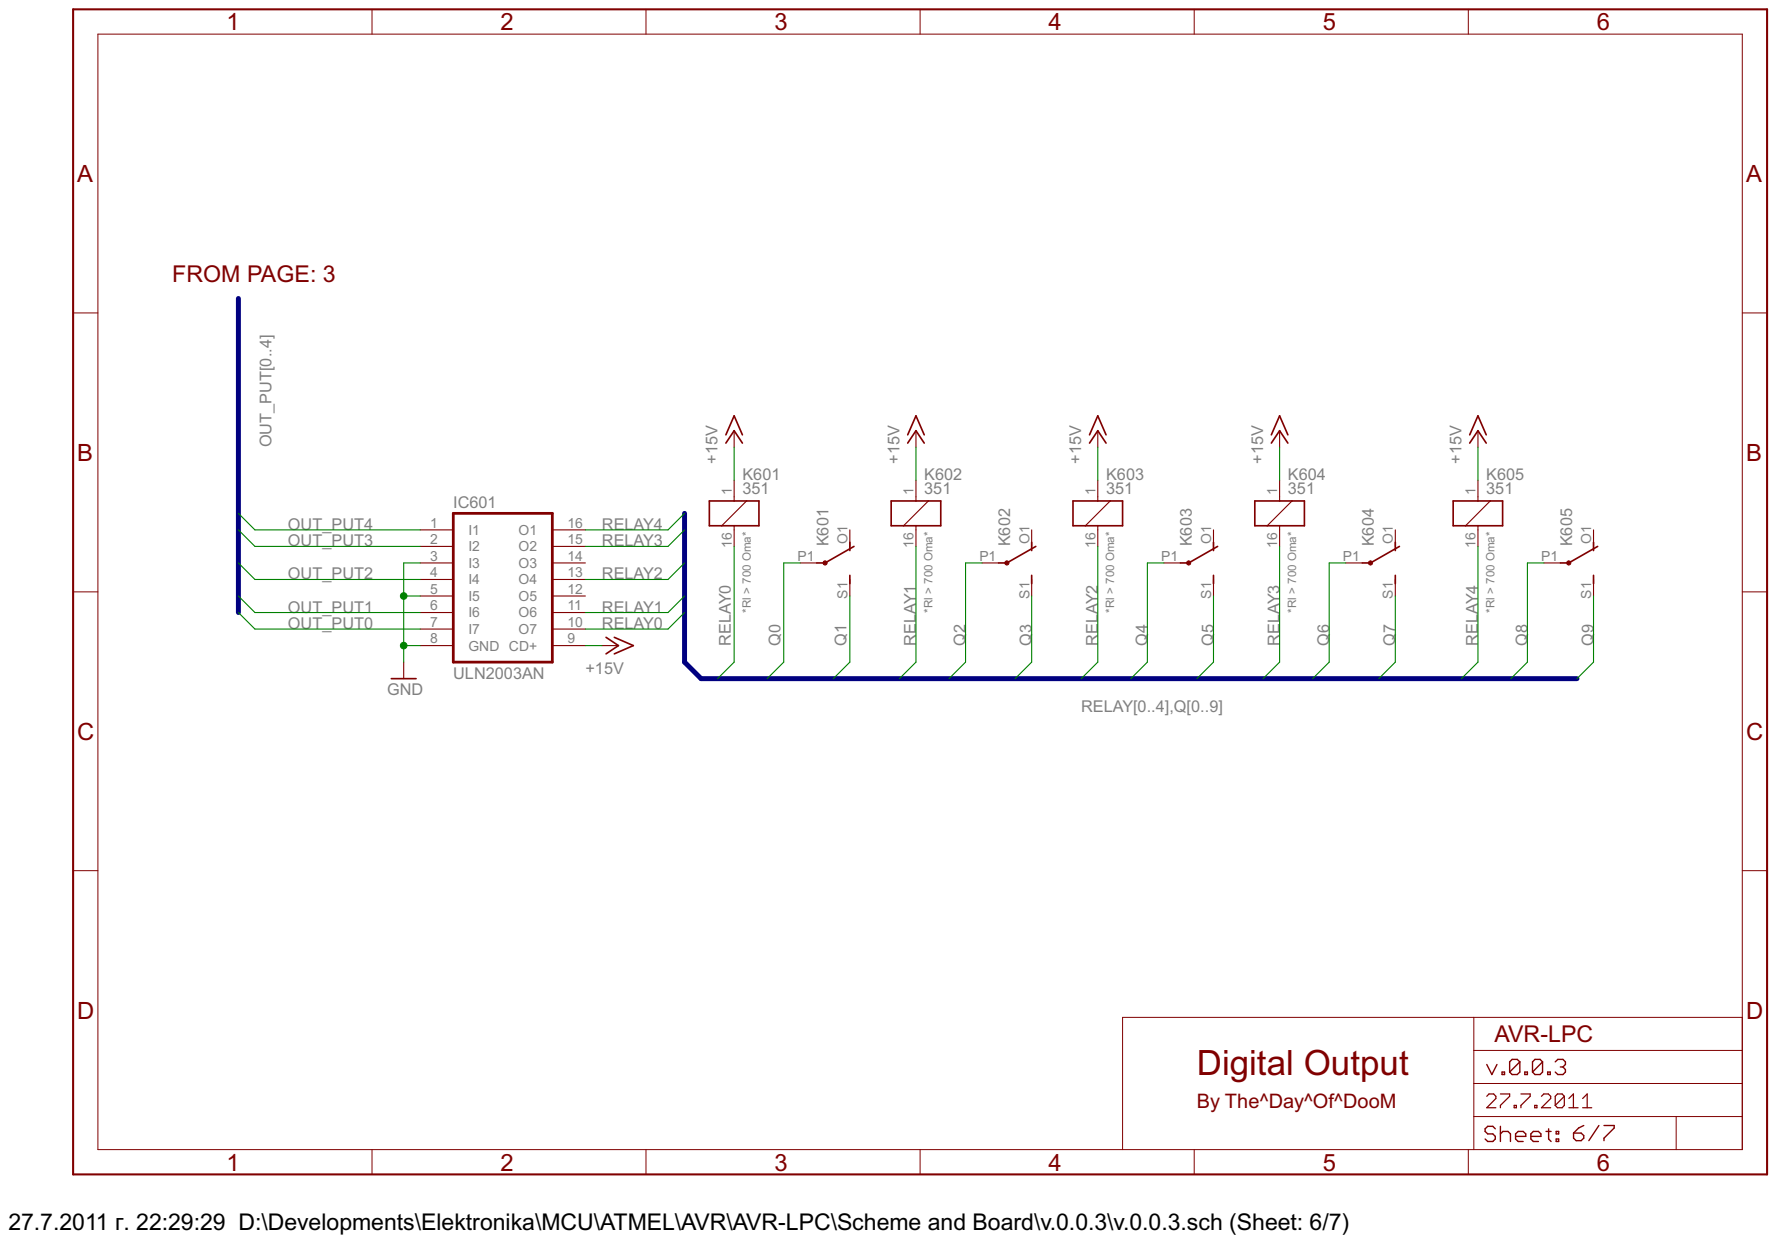
[picture p68: page 6]

By The^Day^Of^DooM

27.7.2011 г. 22:29:29 D:\Developments\Elektronika\MCU\ATMEL\AVR\AVR-LPC\Scheme and Board\v.0.0.3\v.0.0.3.sch (Sheet: 6/7)

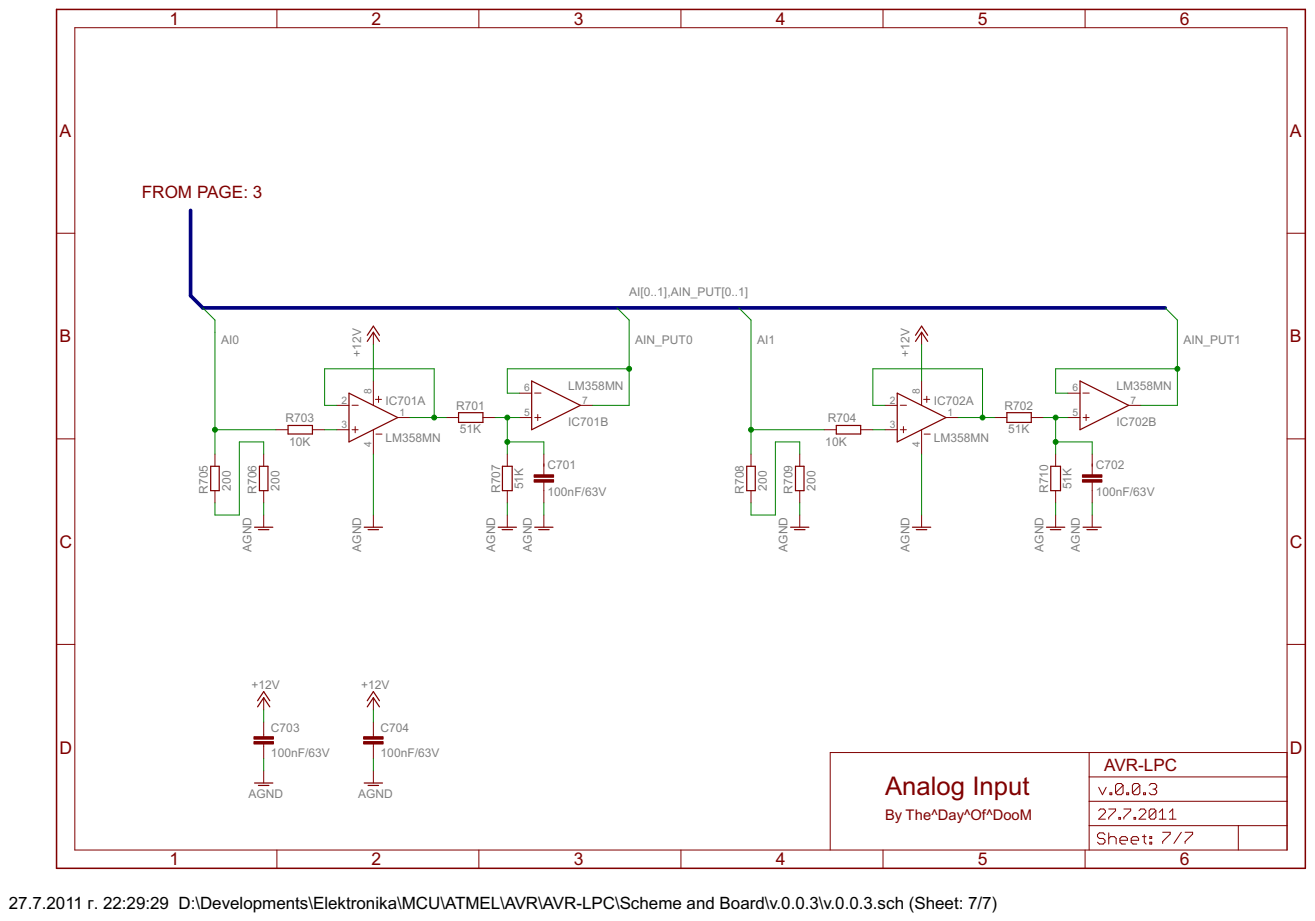
[picture p69: page 7]

By The^Day^Of^DooM

27.7.2011 г. 22:29:29 D:\Developments\Elektronika\MCU\ATMEL\AVR\AVR-LPC\Scheme and Board\v.0.0.3\v.0.0.3.sch (Sheet: 7/7)
