SimeonSimeonovIvanov/AVR-LPC/Scheme and Board/v.0.0.5/v.0.0.5 (Bottom Side).pdf

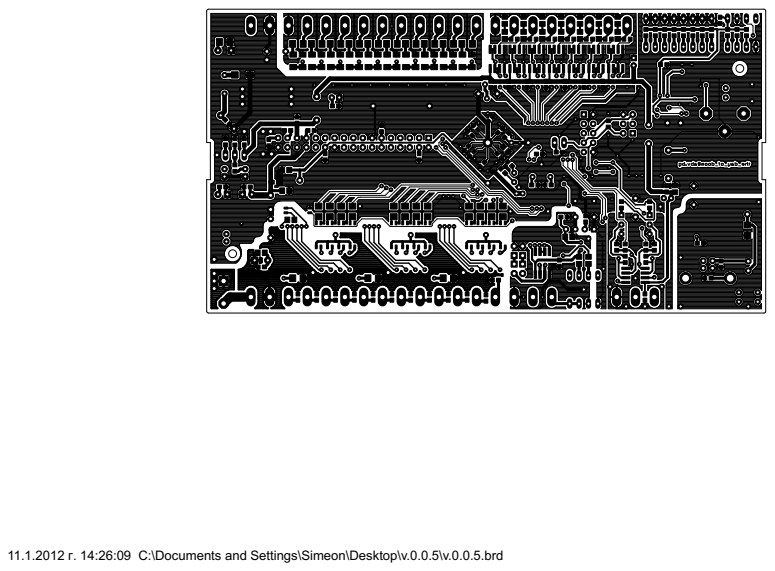
[picture p70: page 1]

11.1.2012 г. 14:26:09 C:\Documents and Settings\Simeon\Desktop\v.0.0.5\v.0.0.5.brd
