SimeonSimeonovIvanov/AVR-LPC/Scheme and Board/v.0.0.4/v.0.0.4 (All Side).pdf

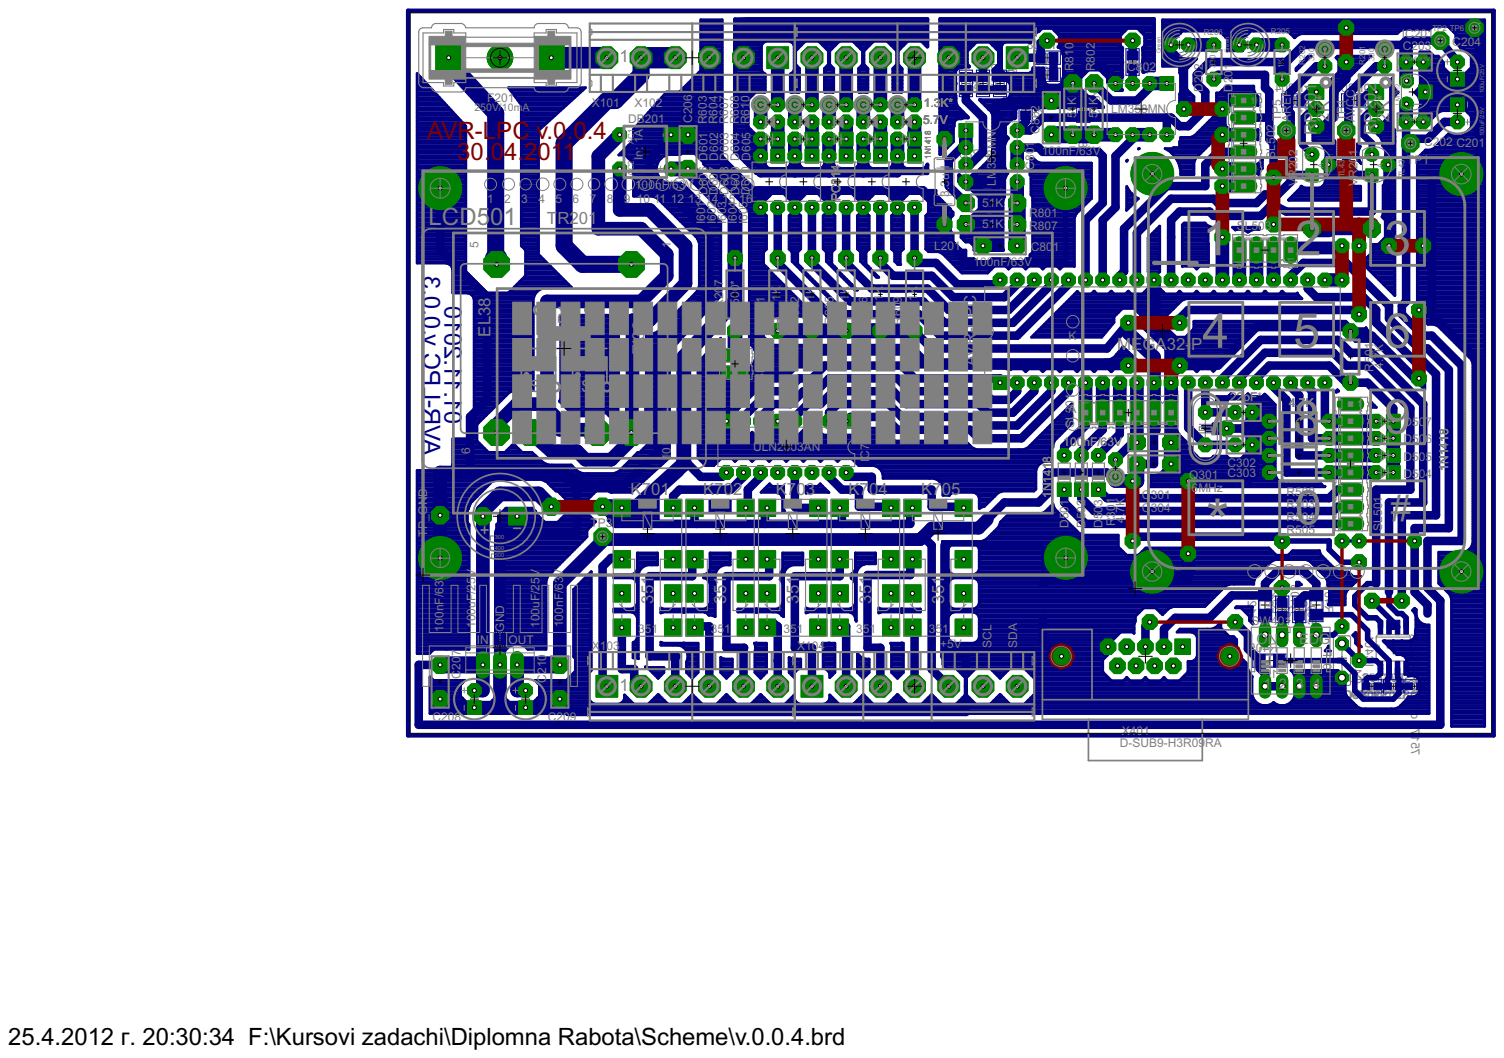
[picture p71: page 1]

25.4.2012 г. 20:30:34 F:\Kursovi zadachi\Diplomna Rabota\Scheme\v.0.0.4.brd
