SimeonSimeonovIvanov/AVR-LPC/Scheme and Board/v.0.0.4/v.0.0.4.pdf

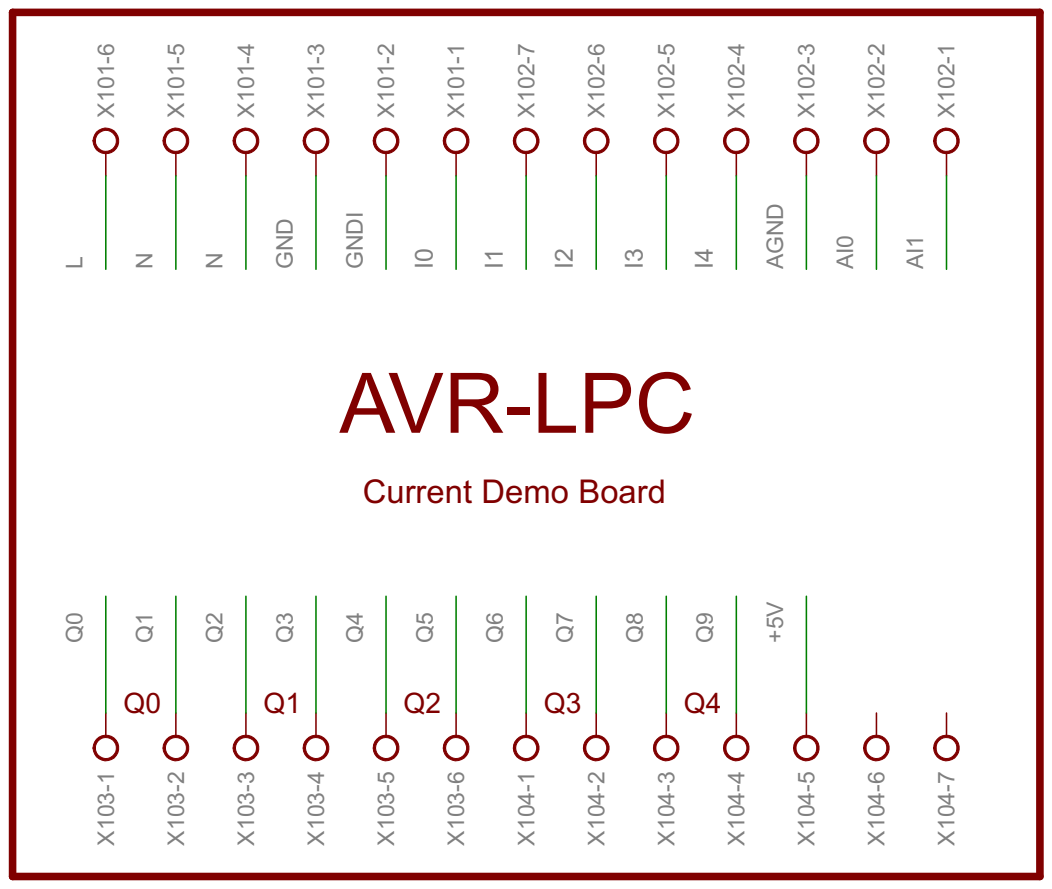
[picture p72: page 1]

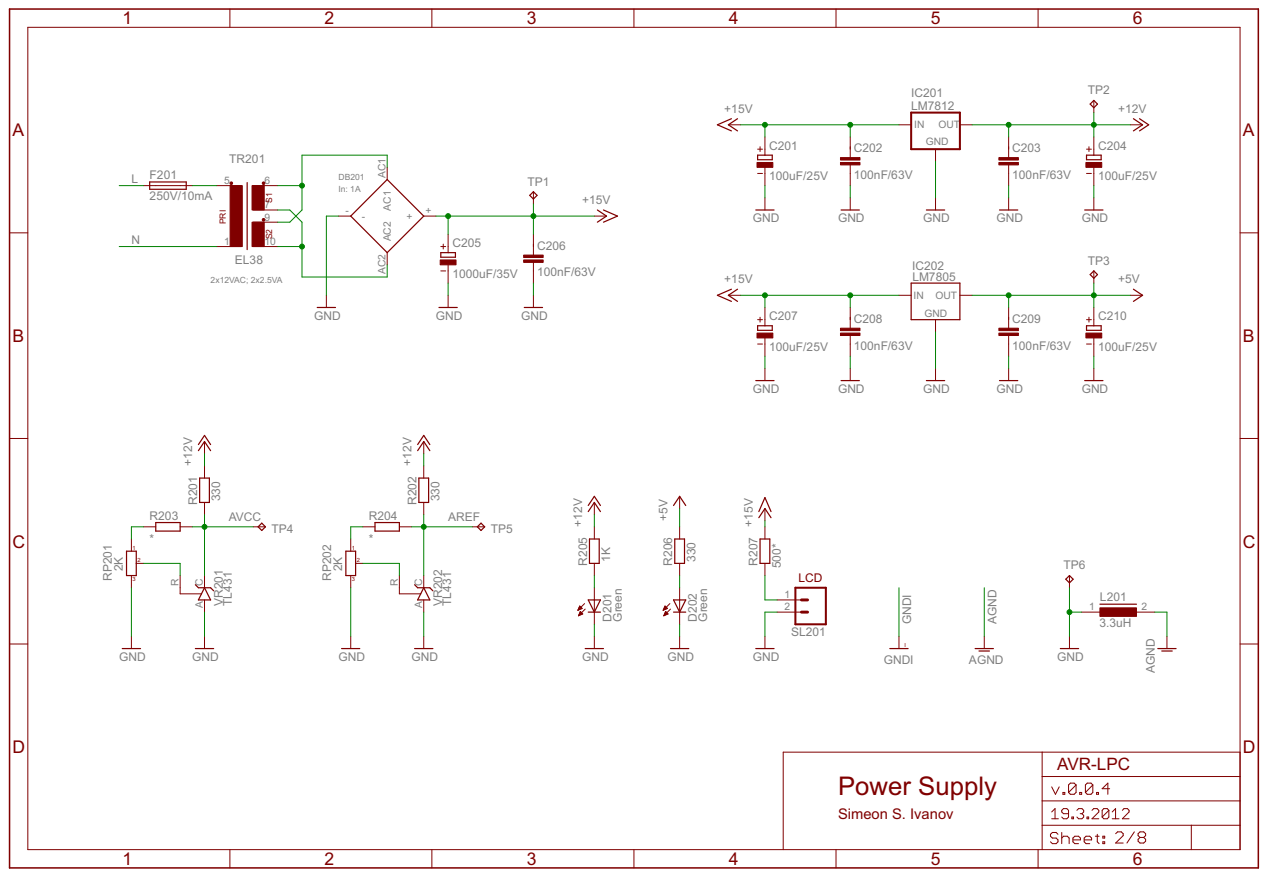
[picture p73: page 2]

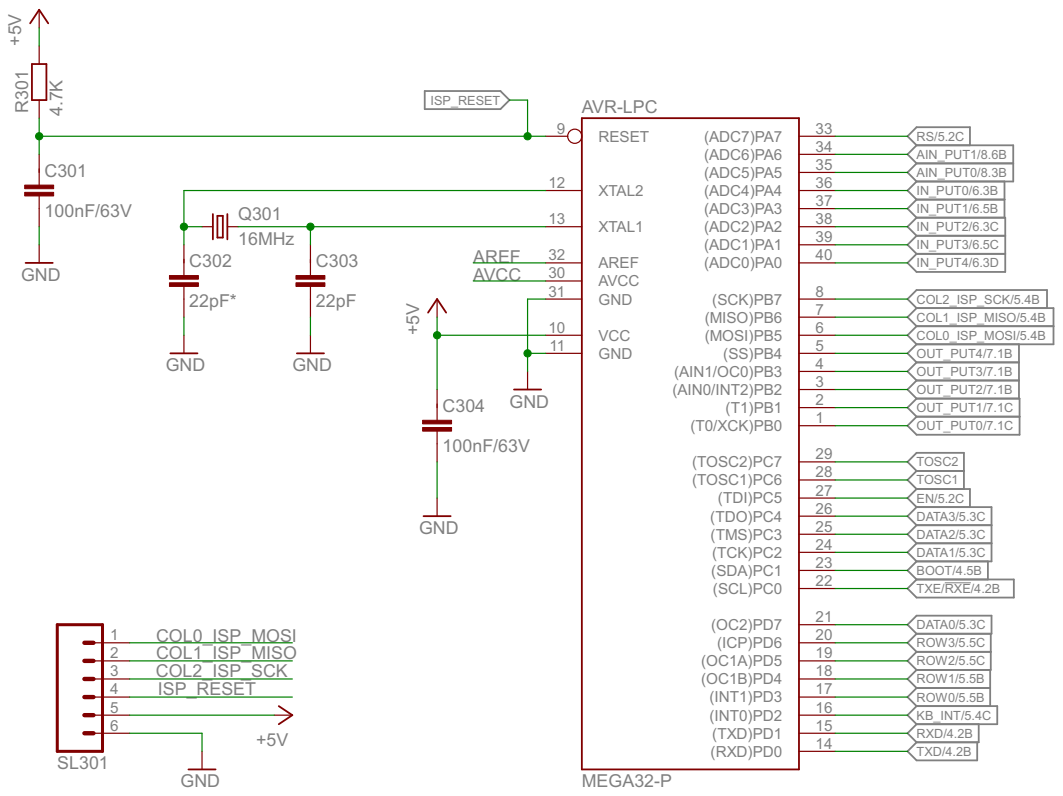
[picture p74: page 3]

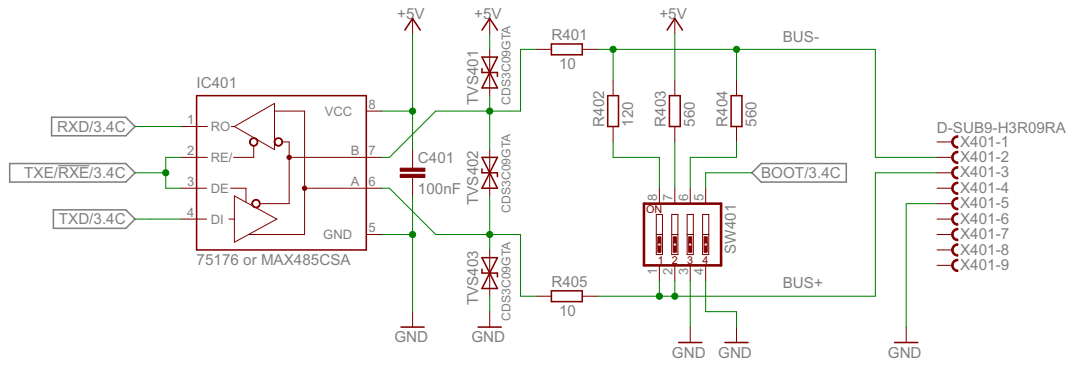
[picture p75: page 4]

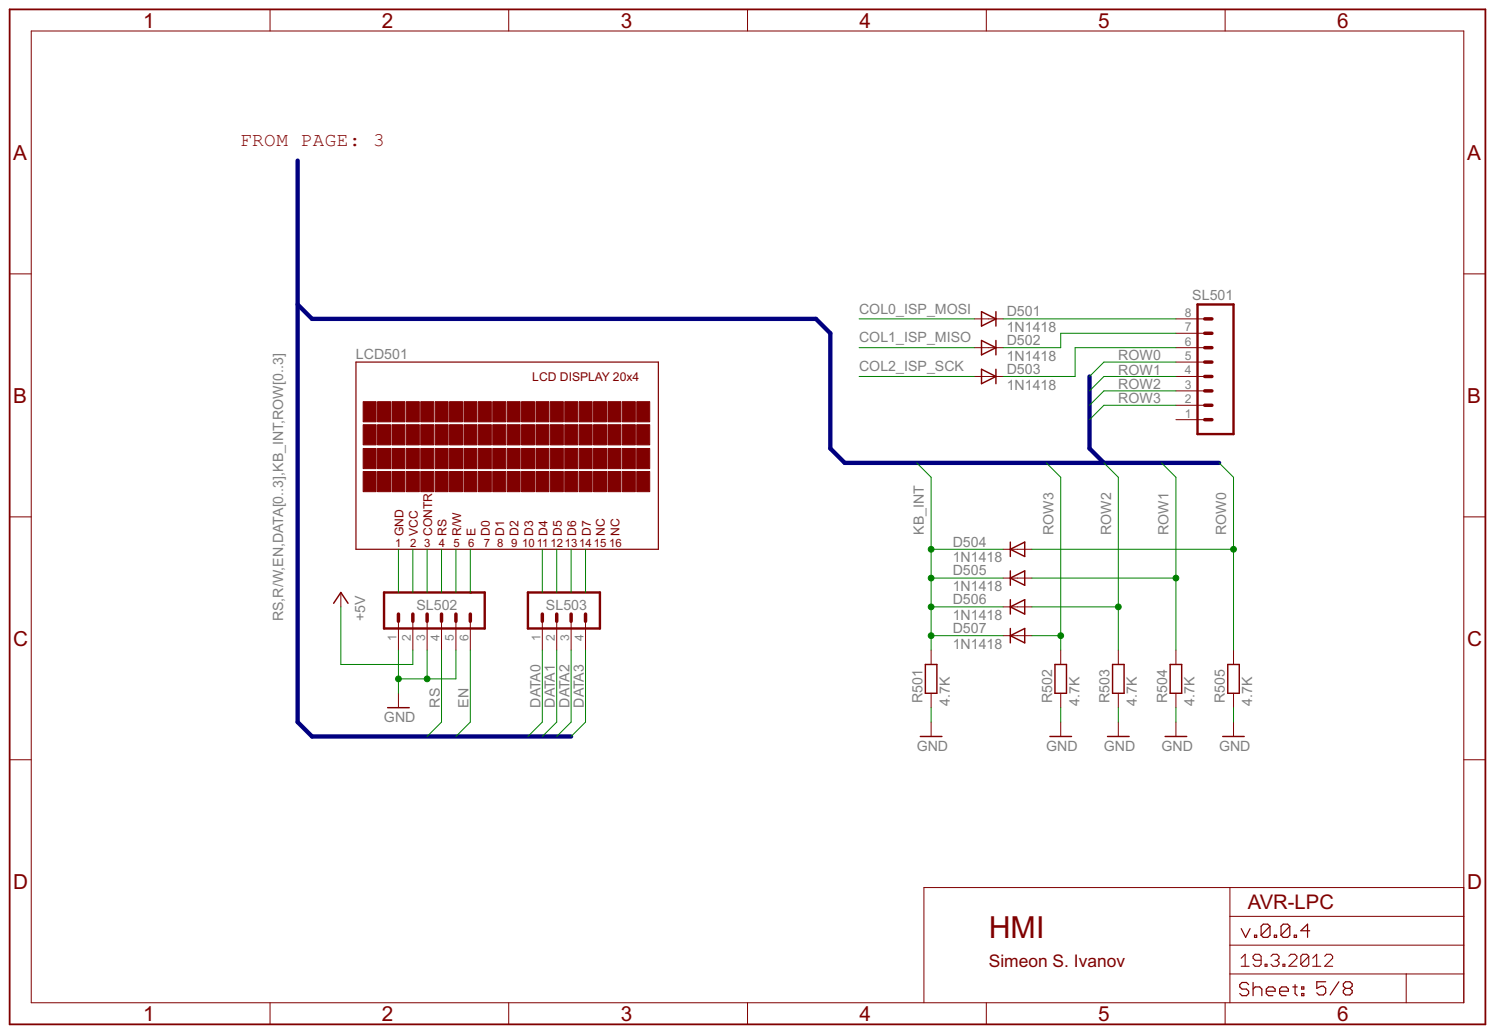
[picture p76: page 5]

RS,R/W,EN,DATA[0..3],KB_INT,RO

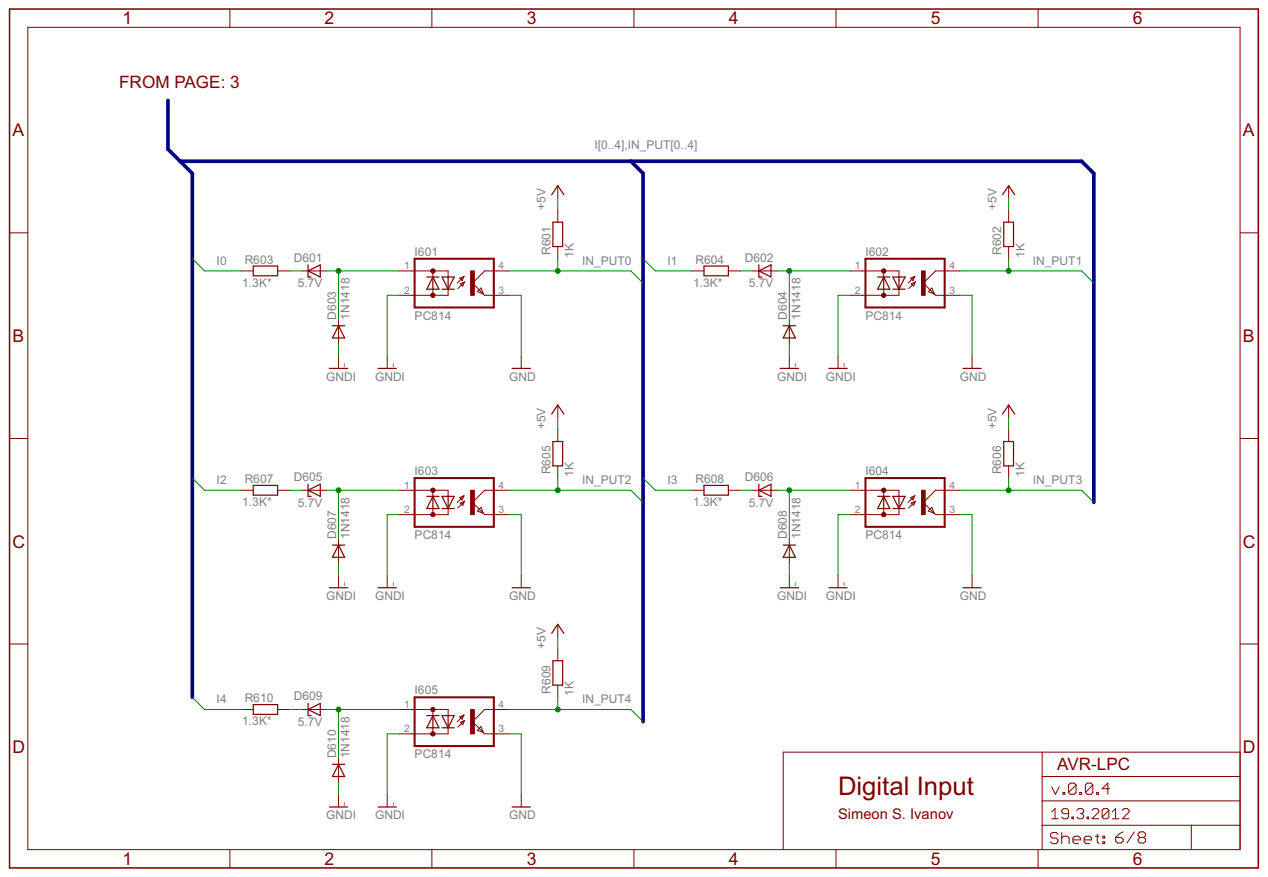
[picture p77: page 6]

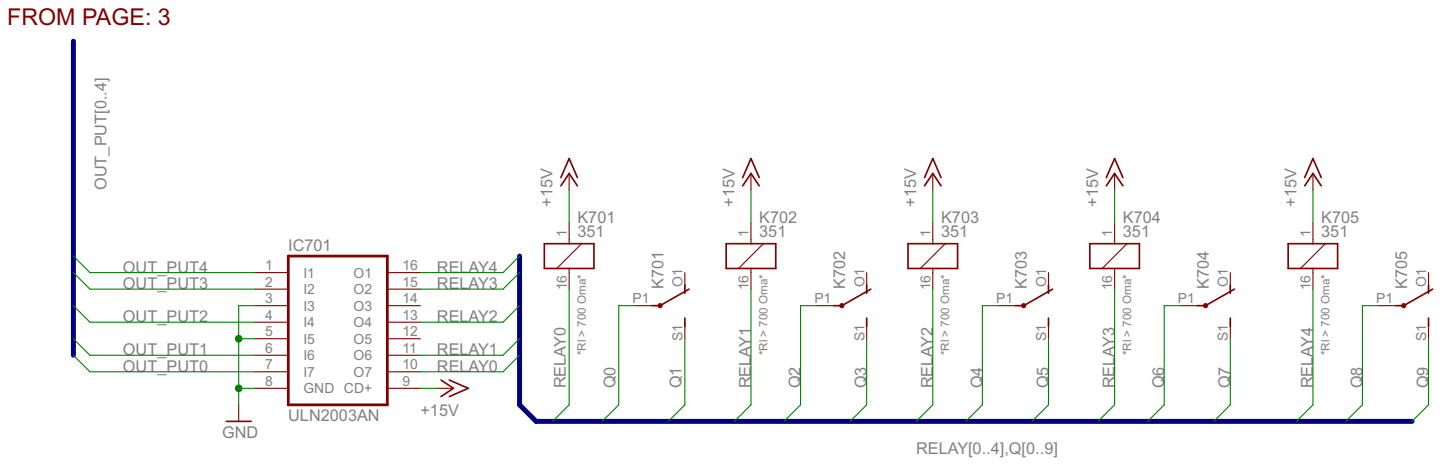
[picture p78: page 7]

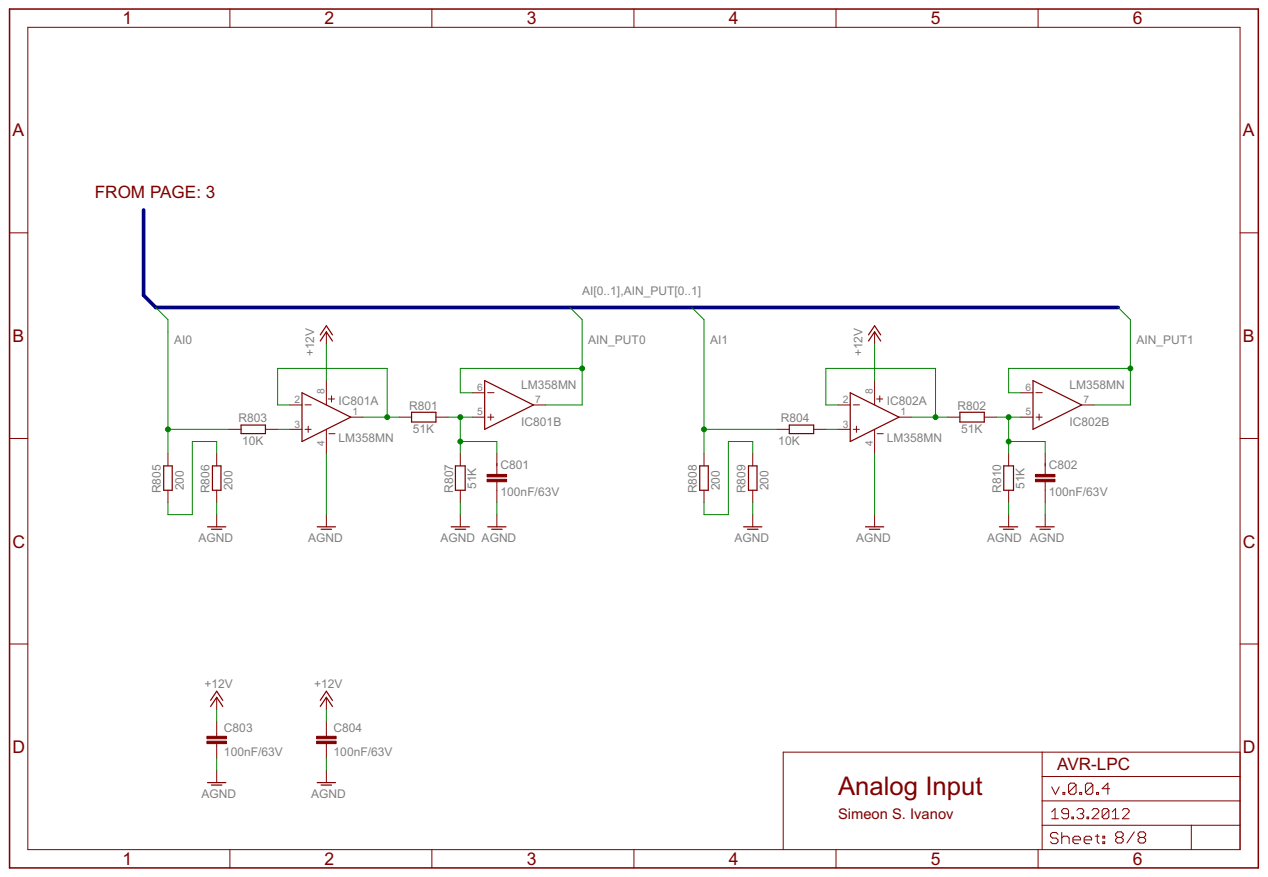
[picture p79: page 8]
